antondrroid/V_meter_013/soft_MCU/multimeter/drawings/Untitled 1.odt

# Описание работы импульсного блока бесперебойного питания

Архитектура блока основана на двойном преобразовании энергии — сначала сетевое напряжение 220 -90 В преобразуется в напряжение 5В, используемое для заряда Li+ion аккуммулятора, состоящего из параллельно подключенных элементов. Преимущество такого подключения в том, что

1. отсутствует необходимость балансировки последовательно подключенных аккуммуляторов.

2. Возможность наращивания емкости неограниченно без изменения конструкции.

Затем напряжение 5В преобразуется импульсным регулятором напряжения
