antondrroid/V_meter_013/soft_MCU/multimeter/Служебные/TZv1.odt

Проект ТЗ на доработку узла ТГС Н2

1. интегрировать Детектор Отбоя (ДО) в печатную плату (ПП)
2. Присвоить название новой ПП — Плата управления узлом ТГС Н2 и занятие децимального номера (МАВЦ 467291.011)
3. Заменить на русские электрорадиоэлементы (ЭРИ) из перечня разрешенных либо по возможности на просто русские.
4. изменить установку микросхемы D7 на верхнюю сторону платы для увеличения просвета между платами на 15 мм (С учетом п.9 высотой 7 мм)
5. предусмотреть установку дополнительных разьемов для подключения платы управления.
6. Вывод световой индикации на разьем (4 вывода)
7. Решить вопрос по выводу световой индикации состояния устройства на лицевую панель. Светодиоды «Пит» и «Соед»
  ( Надо ли их выводить ?)
8. Решить вопрос по выводу кнопки ручного управления отключением «Отбой» устройства на лицевую панель. ( Надо ли их выводить ?)
9. Предусмотреть пространство для прохода кабелей между платами
10. Размещение отверстия в корпусе коробки для радиоэлементов для вывода гермоввода кабелей на корпузе узла в связи с новой разводкой плат.
11. Доработка узла ТГС Н2 МАВЦ 467291.010
12. Изменить разводку потенциометров R33 “Динамик” и R34 “Микрофон”, чтобы опустить их на поверхность ПП, для увеличения просвета между ПП на 4 мм.
13. Подбор потенциометров, допускающих регулировку через отверстие в ПП для увеличения просвета между платами на 22 мм (с учетом п.3)
14. Существует ли необходимость их многократной регулировки при эксплуатации? Тогда можно установить потенциометры модели с открытой ползунковой поверхностью.
15. Изменение конструкции радиатора МАВЦ 467291.010 (в соотв. с п. 3)
