antondrroid/V_meter_013/soft_MCU/multimeter/Служебные/TZv2.odt

ТЗ на конструирование узла ТГС Н2

1. интегрировать Детектор Отбоя (ДО) в печатную плату (ПП)
2. Присвоить название новой ПП — Плата управления узлом ТГС Н2 и занятие децимального номера (МАВЦ 467291.011)
3. Заменить на русские электрорадиоэлементы (ЭРИ) из перечня разрешенных либо по возможности на просто русские.
4. изменить установку микросхемы D7 на верхнюю сторону платы для увеличения просвета между платами на 15 мм (С учетом п.9 высотой 7 мм)
5. предусмотреть установку дополнительных разьемов для подключения платы управления.
6. Предусмотреть пространство для прохода кабелей между платами
7. Размещение отверстия в корпусе коробки для радиоэлементов для вывода гермоввода кабелей на корпусе узла в связи с новой разводкой плат.
8. Доработать узел ТГС Н2 МАВЦ 467291.010
9. Изменить разводку потенциометров R33 “Динамик” и R34 “Микрофон”, чтобы опустить их на поверхность ПП, для увеличения просвета между ПП на 4 мм.
10. Изменить конструкцию радиатора МАВЦ 467291.010 (в соотв. с п. 3)
11. Схема Э3 и перечень элементов в приложении.

Разработал Михайлов

Согласовано Елкин

Утвердил Крысин
