antondrroid/V_meter_013/soft_MCU/multimeter/Служебные/~Z.ODT

Проект ТЗ на доработку узла ТГС Н2

1. интегрировать Детектор Отбоя (ДО) в печатную плату (ПП)
2. Присвоить название новой ПП — Плата управления узлом ТГС Н2 и занятие децимального номера
3. изменить установку микросхемы на верхнюю сторону платы для увеличения просвета между платами на 15 мм (С учетом п.9 высотой 7 мм)
4. предусмотреть установку дополнительных разьемов для подключения платы управления.
5. Решить вопрос по выводу световой индикации состояния устройства на лицевую панель.( Надо ли их выводить или эта функция повлечет за собой дополнительную переделку всего устройства?)
6. Решить вопрос по выводу кнопки ручного управления отключением устройства на лицевую панель.( Надо ли их выводить или эта функция повлечет за собой дополнительную переделку всего устройства?)
7. Предусмотреть пространство для прохода кабелей между платами
8. Размещение отверстия для вывода гермоввода кабелей на корпузе узла.
9. Изменить разводку потенциометров, чтобы опустить их на поверхность ПП, для увеличения просвета между ПП на 4 мм.
10. Подбор потенциометров, допускающих регулировку через отверстие в ПП для увеличения просвета между платами на 22 мм (с учетом п.3)
