antondrroid/V_meter_013/soft_MCU/multimeter/Служебные/закупка/467291.010_v1.odt

Генеральному директору

ООО «ЛОТЕС ТМ»

Стыскину Б.М.

Служебная записка

Прошу приобрести комплектующие изделия для изготовления опытного образца узла ТГС Н2 МАВЦ.467291.010

Количество комплектов: 2 (два).

Начальник ОРТС

________________ / Ю.Д.Крысин /

Приложение:

  Перечень элементов — 8 листов.
