antondrroid/V_meter_013/soft_MCU/multimeter/Служебные/закупка/Служебная закупка УК48-4С.odt

Ген. Директору ООО «Лотес ТМ»

Стыскину Б М

СЛУЖЕБНАЯ ЗАПИСКА

Устройство контактное УК48-4С необходимо в процессе отладки печатной платы с применением микроконтроллера 1887ве4у для его оперативной замены и программирования.

Это служебное оборудование и в изделие, поставляемое заказчику, оно устанавливаться не будет.

Ведущий инженер ОРТС С.И.Тимкин
