antondrroid/V_meter_013/soft_MCU/multimeter/Служебные/ЗАявка на монтаж/Бланк заявки на изготовление печатных плат1.odt

Начальнику производственного

управления ООО Лотес ТМ

Непорада Ю.А.

Служебная записка

Прошу изготовить опытный образец изделия «Модуль 1887»

Применяемость: ТГС Н2

Наименование: модуль 1887 МАВЦ.467291.012

Начальник ОРТС Крысин Ю Д _________

Приложение

1.Печатная плата 758725.032 = 1 шт.

2.Перечень элементов – 3 листа

3.Сборочный чертеж -1лист

4.Электрическая схема – 1 лист.
