antondrroid/V_meter_013/soft_MCU/multimeter/Служебные/ЗАявка на монтаж/изготовление OPTC758725001.odt

Начальнику производственного

управления ООО Лотес ТМ

Непорада Ю.А.

Служебная записка

Прошу дать указание изготовить опытный образец изделия .

Применяемость: УКС АОС

Наименование: ОРТС 758725.001 V3

Начальник ОРТС Крысин Ю Д _________

тел.155

Приложение

1.Печатная плата 758725.033 …………………………………………. 2 шт.

2.Перечень элементов ОРТС 758725.001 V3………………...1 лист

3.Сборочный чертеж ОРТС 758725.001 СБ……………………..1 листа

4.Электрическая схема ОРТС 758725.001 Э3…………………..1 листа
