antondrroid/V_meter_013/soft_MCU/multimeter/Служебные/ЗАявка на монтаж/изготовление печатных плат467291013.odt

Начальнику производственного

управления ООО Лотес ТМ

Непорада Ю.А.

Служебная записка

Прошу дать указание изготовить опытный образец изделия .

Применяемость: ТГС Н2

Наименование: Узел процессора ТГС Н2 МАВЦ.467291.013

Начальник ОРТС Крысин Ю Д _________

Приложение

1.Печатная плата 758725.033 …………………………………………. 1 шт.

2.Перечень элементов МАВЦ.467291.013ПЭ3………………...3 листа

3.Сборочный чертеж МАВЦ.467291.013СБ……………………..3 листа

4.Электрическая схема МАВЦ.467291.013Э3…………………..2 листа
