antondrroid/V_meter_013/soft_MCU/multimeter/Служебные/Протокол испытаний ТГС Н2/предложения по клавиатуре.odt

Утверждаю

Начальник ОРТС

Крысин Ю.Д.

Предложения

по вариантам исполнения подложки

для сенсорной клавиатуры

###### Разработал

###### Михайлов С.Л.

# 1. Технические требования.

## 1.1. Материалы используемые в подложке, должны обеспечивать срабатывание сенсора

## 1.2. Должна обеспечиваться видимость излучения светодиодов сквозь материал подложки.

  3. Должна обеспечиваться возможность записи имени абонента рукой, стирание текста и новая перезапись.
  4. Должна обеспечиваться возможность подкладывания заранее напечатанных этикеток с номерами абонента.
  5. Должна обеспечиваться защита надписей от случайного стирания и загрязнения.
  6. Должна обеспечиваться защита печатной платы с сенсорами от непосредственного контакта с пользователем.

2.Описание конструкции

2.1 Подложка изделия является многослойной и содержит 3 слоя:

а) наклейка из пластика предназначенного для печати на лазерном принтере, на которую наносится сетка с расположением сенсорных кнопок и выполнены просечки для пропускания света от диодов индикации.

Наклейка допускает возможность ручной записи маркером имени абонента в соответствующую ячейку и стирание при необходимости ватным тампоном со спиртовым раствором (специальными салфетками для ухода за оргтехникой)

При этом смываются только следы от маркера, в то время как лазерный порошок является нерастворимым в спирте и координатная сетка остается нетронутой.

Возможно также приклеивание к ней заранее напечатанных самоклеющихся этикеток с последующим многократным отклеиванием и приклеиванием.

б) опционально: бумажная одноразовая этикетка, повторяющая форму наклейки из пункта а) и предназначенная для заполнения пользователем на месте. Можно включить в комплект несколько штук.

в) Защитный прозрачный слой, толщиной 250-350 мкм, гладкий либо с пуклевками диаметром 12 мм для имитации нажатия.

Можно комплектовать изделие накладками обоих видов, по выбору пользователя.

2.2 Варианты защитного слоя с пуклевками

A. Пуклевка для нажатия расположенная по центру клавиши. Поверхность может быть прозрачная, либо матовая.
  Позволяет просматривать надписи на подложке без значительных искажений как на прозрачной, так и на покрытой матовым слоем поверхности.
B. Пуклевка для светодиода (рассеиватель) выполненный в виде множества мелких выпуклостей для увеличения светового пятна на поверхности панели.
C. Пуклевка для светодиода (рассеиватель) поднятая над поверхностью, для обеспечения более широкого угла обзора индикации (до 180о).

Нажимаемые пуклевки возможно изготовить на пленках толщиной до 300мкм, так как на более толстых пленках возможно обламывание при нажатии.

На пленках толщиной более 300мкм возможно изготовление ненажимаемых пуклевок для рассеивателей светового потока, при оставлении сенсорной площадки гладкой.

2.3 Толщина покрытия

Толщина покрытия 2000мкм препятствует срабатыванию сенсора, используемого в данной конструкции.

В макете использованы панели толщиной 500 — 2000 мкм, дающие представление о затруднении срабатывания с ростом толщины защитного слоя.

Приемлемое время срабатывания получается при толщине покрытия 500 — 1000 мкм, при толщине 1500мкм срабатывание затруднено, при 2000мкм срабатывание не происходит.

Таблица 1

Наименование испытаний и проверок | № пункта методики испытаний | Примечание
1 Проверка входящего вызова от абонента ТА к абоненту ТГС Н2 | 2.1
2 Проверка исходящего вызова от абонента ТГС Н2 к абоненту ТА | 2.2
3 Проверка отбоя соединения со стороны абонента ТА при изменении сопротивления абонентской линии | 2.3
4 Проверка отбоя соединения по таймеру при отсутствии голосовой активности | 2.4
5 Проверка входящего вызова от абонента ТА к ТГС Н2 при изменении амплитуды вызывного сигнала | 2.5
6. Проверка входного сопротивления ТГС Н2 в режиме «Соединение» | 2.6

Испытания проводятся рабочей группой, в составе представителей ОРТС ООО «ЛОТЕС ТМ» и по согласованию представителей ПУ.

Методики, условия и порядок проведения проверок могут уточняться и дополняться решением комиссии по проведению испытаний.

Допускается проведение проверок по отдельным компонентам и дополнительных тестов.

1.5. Условия и порядок проведения испытаний

Все испытания проводятся согласно пункту 1.4 в различных климатических условиях, с оформлением отдельного протокола по каждому пункту настоящего раздела.

- 1.5.1 в нормальных климатических условиях:
- температуры окружающего воздуха от 288 до 298 К (от плюс 15 до плюс 25 С);
- относительной влажности воздуха не более 75 % при температуре не выше 298 К (25 С);

атмосферного давления от 86 до 106 кПа (от 645 до 795 мм рт.ст.).

- 1.5.2 на пониженную температуру
- температуры окружающего воздуха от -40 ºС до - 10 С;
- 1.5.1 на повышенную температуру

- температуры окружающего воздуха от плюс 25 до плюс 40 С;

# 2. Методика испытаний.

Перед началом испытаний собрать схему согласно приложению 1.

## 2.1 Проверку входящего вызова от абонента ТА к абоненту ТГС Н2 проводят следующим методом:

а) установить на имитаторе линии ноль км;

б) Поднять трубку на ТА и набрать вызывной номер ТГС Н2. Должно установиться соединение;

в) Абонент ТА передает сообщение абоненту ТГС Н2. Контролировать воспроизведение этого сообщения в динамике ТГС Н2;

г) нажать и удерживать кнопку «Микрофон» на ТГС Н2. Абонент ТГС Н2 передает сообщение абоненту ТА. Контролировать воспроизведение этого сообщения в динамике трубки ТА.

д) положить трубку на ТА. Контролировать что через время не более 4 с должен произойти отбой соединения, воспроизведение акустического сигнала «Отбой» в динамике ТГС Н2 должно прекратиться;

Изделие считают выдержавшим проверку если:

- при входящем вызове на ТГС Н2 соединение автоматически устанавливается;

- контрольный текст прослушивается без искажений, провалов и изменения тембра;

- отбой соединения со стороны абонента ТА производится за время не более 4 с.

## 2.2 Проверку исходящего вызова от абонента ТГС Н2 к абоненту ТА проводят следующим методом:

а) установить на имитаторе линии 0 км;

б) нажать кнопку на ТГС Н2 «Вызов», контролировать наличие акустического сигнала «Ответ станции»;

в) через время приблизительно 10с контролировать наличие акустического сигнала «Отбой». Контролировать что через время не более 4 с должен произойти отбой соединения, воспроизведение акустического сигнала «Отбой» в динамике ТГС Н2 должно прекратиться.

г) повторить проверку по п.п. б) и в) для сопротивления линии 1-8 км

Изделие считают выдержавшим проверку если:

- при исходящем вызове на ТГС Н2 прослушивается сигнал «Ответ станции»;

- отбой соединения со стороны абонента ТГС производится за время не более 4 с.

## 2.3 Проверку входящего вызова от абонента ТА к ТГС Н2 при изменении (снижении) амплитуды вызывного сигнала в связи с увеличением длины линии и отбоя соединения со стороны абонента ТА при изменении сопротивления абонентской линии (далее - АЛ) проводят следующим методом:

а) установить на имитаторе линии 1 км;

б) провести проверку согласно п.2.1 а), б), д);

в) последовательно устанавливая на имитаторе линии от 2 до 8 км, повторить проверку согласно п.2.1 а), б), д);

Изделие считают выдержавшим проверку если отбой соединения производится за время не более 4 с.

## 2.4 Проверку отбоя соединения по таймеру при отсутствии голосовой активности проводят следующим методом:

а) установить на имитаторе линии 0 км;

б) поднять трубку на ТА и набрать вызывной номер ТГС Н2. Должно установиться соединение;

в) если в течении 1 минуты на ТГС Н2 не нажимают кнопку «Микрофон», а на ТА отключен (приглушен) микрофон, то соединение должно отбиться, абонент ТА должен услышать акустический сигнал «Отбой» (короткие гудки);

г) положить трубку на ТА;

д) установить на имитаторе линии 8 км и повторить проверку по п.п.2.4 б) - г).

Изделие считают выдержавшим проверку если при отсутствии голосовой активности в режиме соединения автоматический отбой соединения производится за время не более 60 с.

2.5 Проверку входного сопротивления ТГС Н2 в режиме «Соединение» проводят следующим методом:

а) установить сопротивление линии 0 км;

б) установить исходящее соединение, нажав на ТГС Н2 кнопку «Вызов»;

г) измерить напряжение постоянного тока на входе ТГС Н2;

д) вычислить входное сопротивление по формуле: Rвх =U/Iлин, где Iлин=20 мА.

Изделие считают выдержавшим проверку, если значение Rвх от 300 до 850 Ом.

# Протокол испытаний 1.5.1

Узла процессора ТГС Н2 МАВЦ.467291.013

Пункт | № попытки | Расстояние (эквивалент линии, км)
| | 0 | 1 | 2 | 3 | 4 | 5 | 6 | 7 | 8 | 9 | 10
2.1 | 1
2.2 | 1
2.3 | 1
2.4 | 1
2.5 | 1 | Uвх = ……...В Rвх = ……....В / 20 мA = ….…...Ом

Вывод:

Изделие МАВЦ.467291.013 узел процессора ТГС Н2 соответствует требованиям

- ТЗ на ТГС Н2;
- Технические требования на ПО ТГС Н2
- ПМИ ТГС Н2.

Может быть внедрено для серийного производства.

Испытания изделия проводила комиссия в составе :

Кротов Б.Г. — председатель комиссии…………………………./ /

Михайлов С.Л. - член комиссии…………………………………/ /

ТГС Н2 зав.№____________

Протокол № 1.5.2

Испытания на пониженную температуру

## 1 Время проведения испытаний

- Дата 28.05.18 г. Начало испытаний 09-40 Завершение испытаний 18-00

## 2 Состав испытываемого оборудования

СЧ изделия участвующие в испытаниях вне климатической камеры:

Наименование и обозначение изделия | Кол-во (шт.) | Группа исполн. (ВВФ) | Зав.№
1.1 Терминал громкоговорящей связи «НАБАТ» Н2, МАВЦ.465482.016 (ТГС Н2) | 1 | 1.3

- Модуль базовый «НАБАТ» А2,

- Аппарат телефонный ВЕКТОР ST-555/01

- СОДС «Набат»

## 3 Этапы испытаний:

1) НКУ – проверка;

2) Предельная пониженная температура – выдержка в выключенном состоянии 3 ч;

3) Рабочая пониженная температура – выдержка в выключенном состоянии 3 ч – включение –проверка;

4) НКУ – выдержка в выключенном состоянии 3 ч – включение – проверка.

## 4 Результаты испытаний

Вид проверки | Содержание проверки | Этапы испытаний и время проверки | | | | | Примеч.
| | 1 НКУ | 2 -40 ºС | | 3 -10 ºС | 4 НКУ
Связь с ТГС Н2 | Вызов, | + | НП | | + | +
| соединение | + | НП | | + | +
| отбой | + | НП | | - | -

Замечания

Испытания проводили: Испытатель

ТГС Н2 зав.№____________

Протокол № 1.5.3

Испытания на повышенную температуру

## 1 Время проведения испытаний

- Дата 28.05.18 г. Начало испытаний 09-40 Завершение испытаний 18-00

## 2 Состав испытываемого оборудования

СЧ изделия участвующие в испытаниях вне климатической камеры:

Наименование и обозначение изделия | Кол-во (шт.) | Группа исполн. (ВВФ) | Зав.№
1.1 Терминал громкоговорящей связи «НАБАТ» Н2, МАВЦ.465482.016 (ТГС Н2) | 1 | 1.3

- Модуль базовый «НАБАТ» А2,

- Аппарат телефонный ВЕКТОР ST-555/01

- СОДС «Набат»

## 3 Этапы испытаний:

1) НКУ – проверка;

2) Рабочая повышенная температура – выдержка во включенном состоянии 2 ч – проверка;

3) Предельная повышенная температура – выдержка в выключенном состоянии 2 ч;

4) Рабочая повышенная температура – выдержка 2 ч – включение – проверка;

5) НКУ – выдержка во включенном состоянии 2 ч – проверка.

## 4 Результаты испытаний

Вид проверки | Содержание проверки | Этапы испытаний и время проверки | | | | | Примеч.
| | 1 НКУ | 2 +40 ºС | 3 +40 ºС | 4 +40 ºС | 5 НКУ
Связь с ТГС Н2 | Вызов, | + | НП | | + | +
| соединение | + | НП | | + | +
| отбой | + | НП | | - | -

Замечания

Испытания проводили: Испытатель

Приложение 2

Протокол cравнительных испытаний

# ТГС Н2 Версия 1 (с установленным модулем DCPC1)

# ТГС Н2 Версия 2 (с контроллером 1887ВЕ4У)

Пункт методики | | Расстояние (эквивалент линии, км)
| | 0 | 1 | 2 | 3 | 4 | 5 | 6 | 7 | 8 | 9 | 10
2.1 | 1
| 2
| 3
| 1
| 2
| 3
2.2 | 1
| 2
| 3
| 1
| 2
| 3
2.3 | 1
| 2
| 3
| 1
| 2
| 3
2.4 | 1
| 2
| 3
| 1
| 2
| 3
2.5 | 1
