antondrroid/V_meter_013/stend_e3/stend_main4_dummy/~D/~02_PE3/element_list_v0.odt

| | | | | xxxx.xxxxxx.xxxПЭ3
Изм. | Лист | № докум. | Подп. | Дата
Разраб. | | | | | Перечень элементов | Лит. | | | Лист | Листов
Пров. | | | | | | | | | 1 | 5
Н.контр.
Утв.

Подп. и дата
Инв. № дубл.
Взам. инв. №
Подп. и дата
Инв. № подл.

Перв. примен. | xxxx.xxxxxx.xxx
Справ. №

Зона | Поз. обозначе- ние | Наименование | Кол. | Примечание
| | | Утвержден
| | | xxxx.xxxxxx.xxx -УД

Копировал

Формат А4

| | | | | xxxx.xxxxxx.xxxПЭ3 | Лист
| | | | | | 2
Изм. | Лист | № докум. | Подп. | Дата

Подп. и дата
Инв. № дубл.
Взам. инв. №
Подп. и дата
Инв. № подл.

Зона | Поз. обозначе- ние | Наименование | Кол. | Примечание

Копировал

Формат А4

| | | | | xxxx.xxxxxx.xxxПЭ3 | Лист
| | | | | | 3
Изм. | Лист | № докум. | Подп. | Дата

Подп. и дата
Инв. № дубл.
Взам. инв. №
Подп. и дата
Инв. № подл.

Зона | Поз. обозначе- ние | Наименование | Кол. | Примечание

Копировал

Формат А4

| | | | | xxxx.xxxxxx.xxxПЭ3 | Лист
| | | | | | 4
Изм. | Лист | № докум. | Подп. | Дата

Подп. и дата
Инв. № дубл.
Взам. инв. №
Подп. и дата
Инв. № подл.

Зона | Поз. обозначе- ние | Наименование | Кол. | Примечание

Копировал

Формат А4

| | | | | xxxx.xxxxxx.xxxПЭ3 | Лист
| | | | | | 5
Изм. | Лист | № докум. | Подп. | Дата

Подп. и дата
Инв. № дубл.
Взам. инв. №
Подп. и дата
Инв. № подл.

Копировал

Формат А4

Лист регистрации изменений
Изм. | Номера листов (страниц) | | | | Всего листов (страниц) в докум. | № докум. | Входящий № сопрово- дительного докум. и дата | Подп. | Дата
| изме- ненных | заме- ненных | новых | аннули- рованных
