antondrroid/V_meter_013/voltmeter_docs/M3500A_DM.pdf

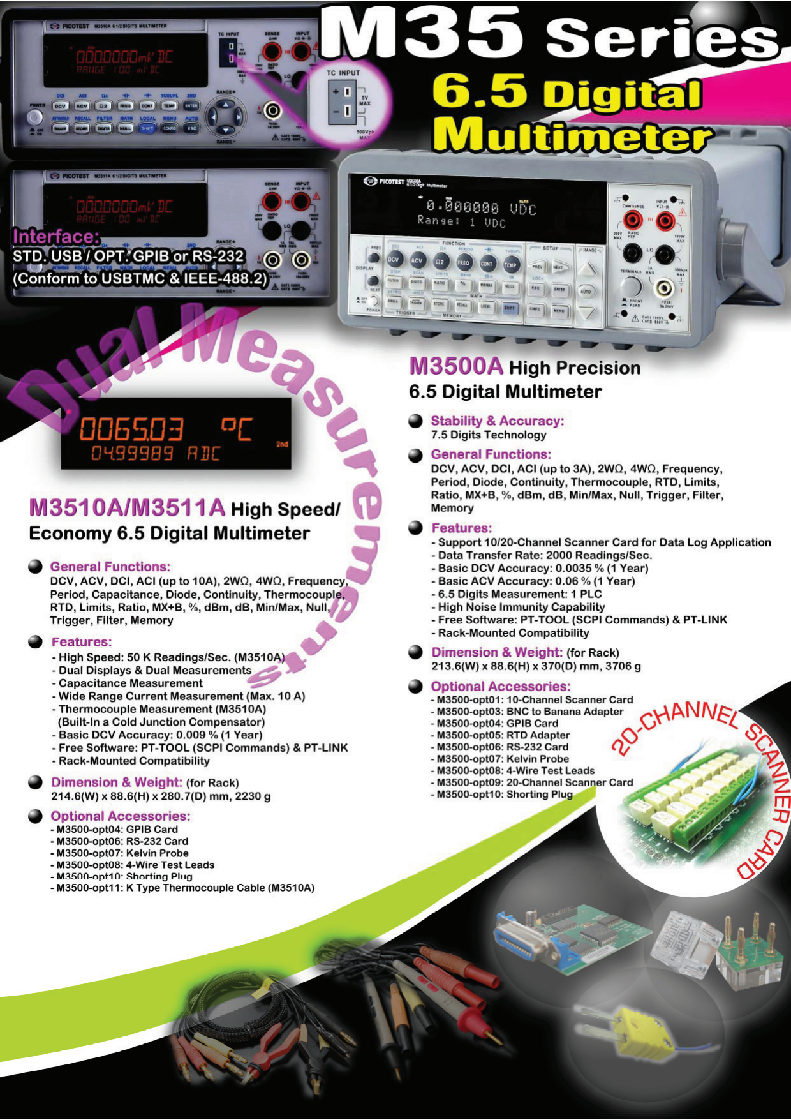
[picture p3: page 1]
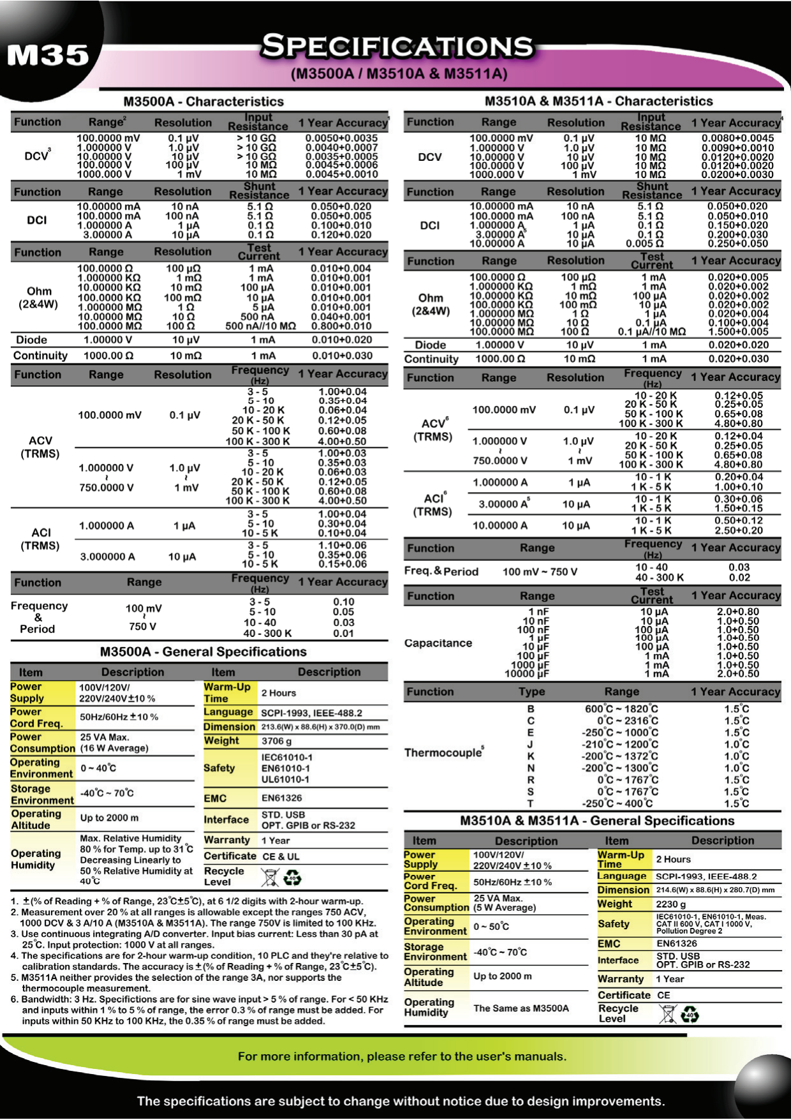
[picture p4: page 2]
