antondrroid/V_meter_013/samples/file sample.jpg

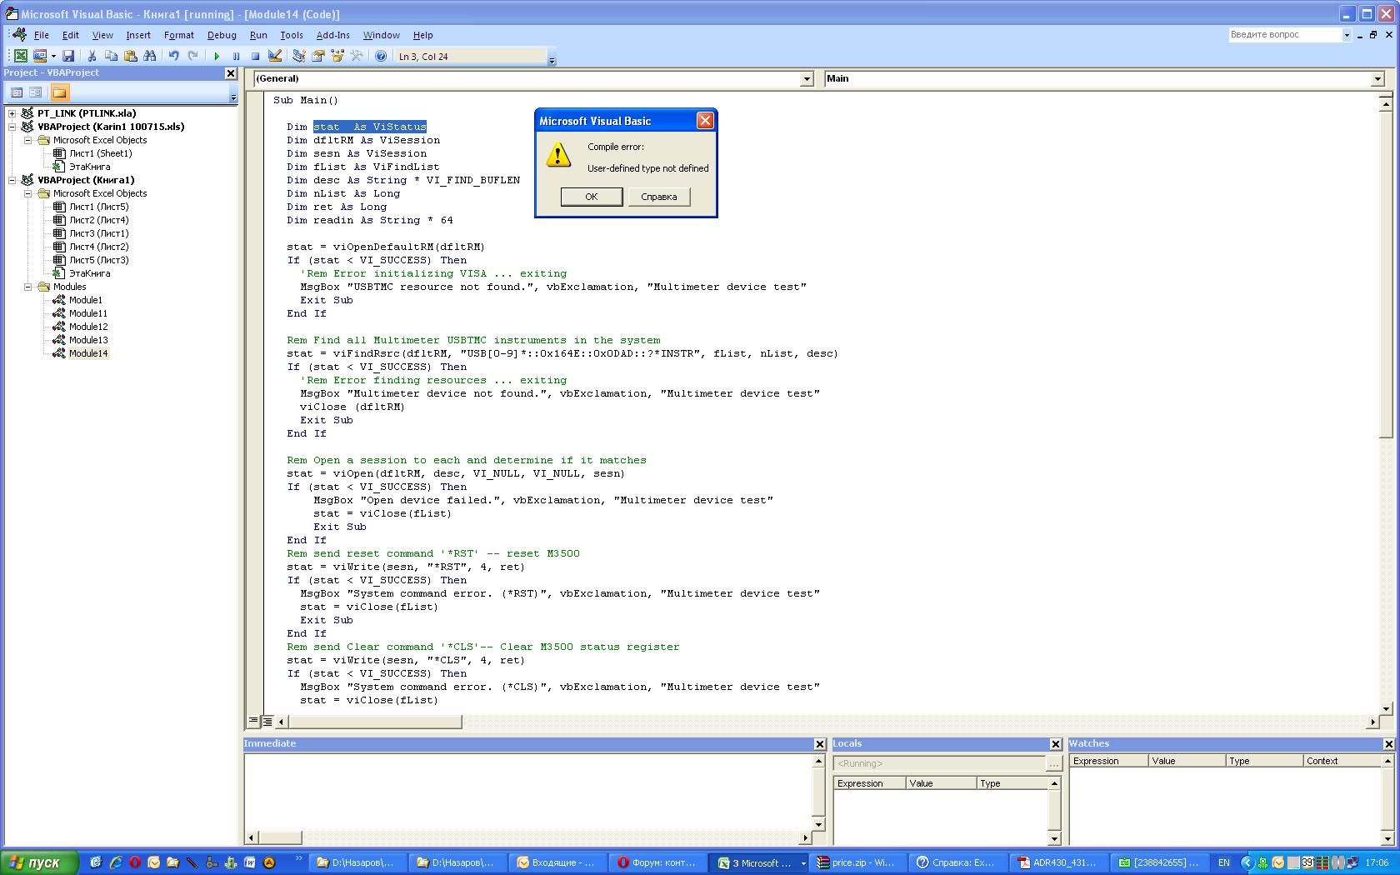
samples/file sample.jpg
