antondrroid/V_meter_013/screen/2021-07-02 12_02_32-NI-VISA - NI — Mozilla Firefox.png

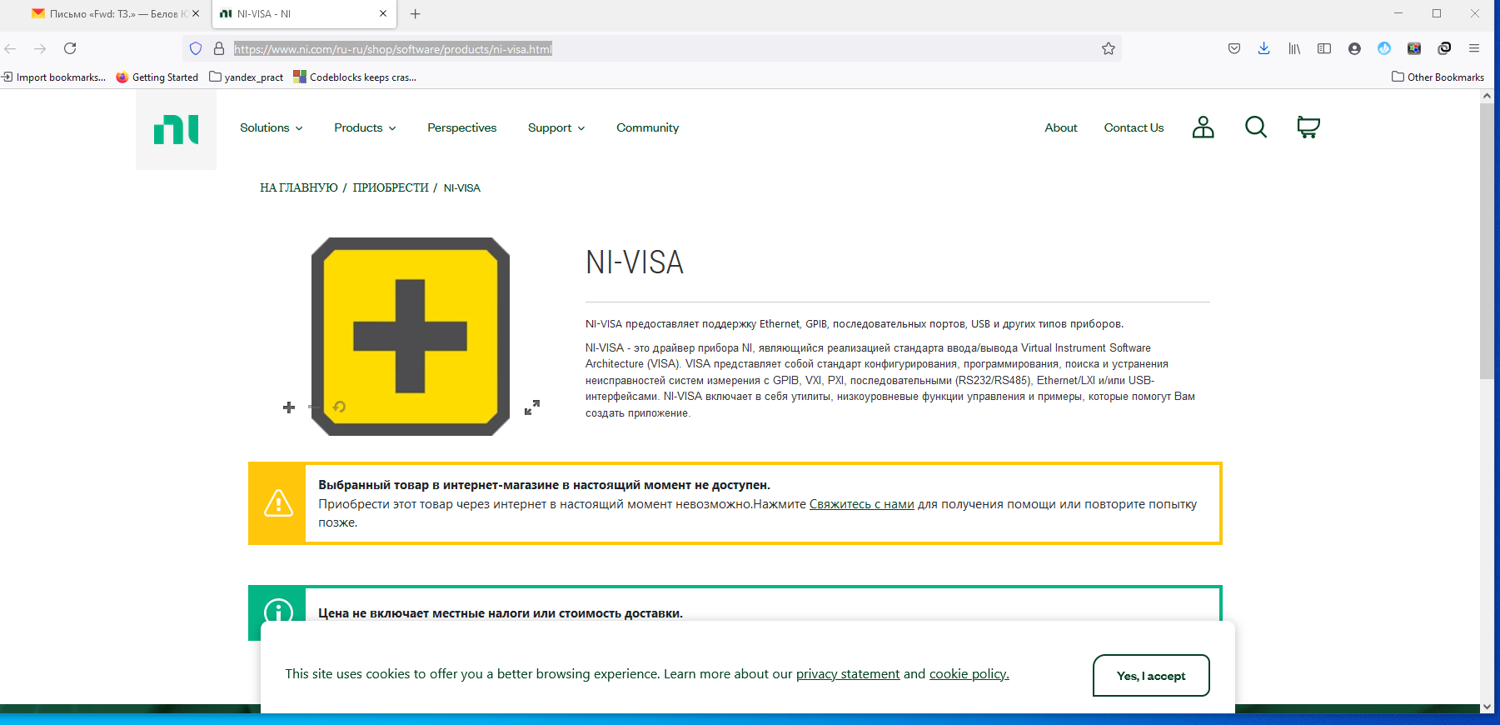
screen/2021-07-02 12_02_32-NI-VISA - NI — Mozilla Firefox.png
