antondrroid/V_meter_013/screen/2021-07-02 12_22_44-Письмо «Fwd_ ТЗ.» — Белов Юрий Максимович — Яндекс.Почта — Mozilla Firefox.png

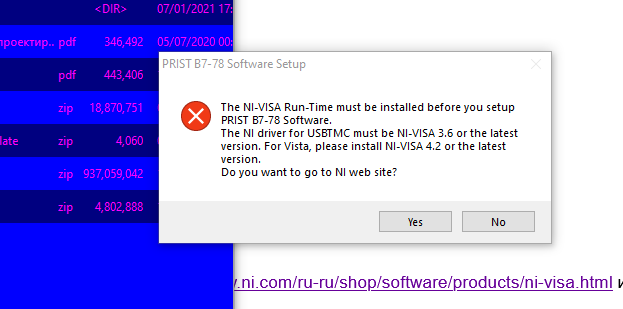
screen/2021-07-02 12_22_44-Письмо «Fwd_ ТЗ.» — Белов Юрий Максимович — Яндекс.Почта — Mozilla Firefox.png
