antondrroid/V_meter_013/screen/2021-07-09 12_47_10-Найди пару - BrainApps.ru — Mozilla Firefox.png

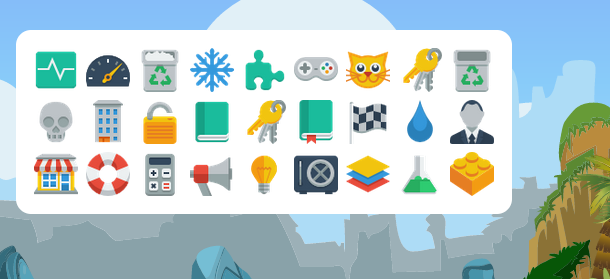
screen/2021-07-09 12_47_10-Найди пару - BrainApps.ru — Mozilla Firefox.png
