antondrroid/V_meter_013/screen/2021-08-05 19_15_09-Total Commander (x64) 9.51 - NOT REGISTERED.png

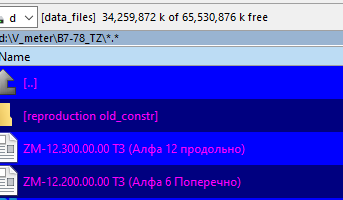
screen/2021-08-05 19_15_09-Total Commander (x64) 9.51 - NOT REGISTERED.png
