antondrroid/V_meter_013/screen/2021_08_03_13_34_38_Письмо_Re_производство_старой_конструкции._Белов_Юрий_Максимович_Яндекс.П.png

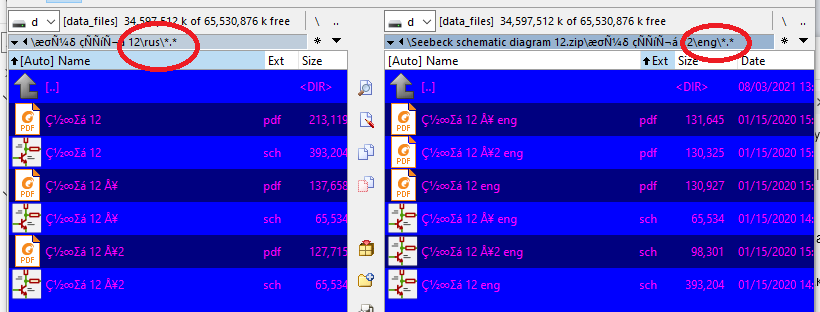
screen/2021_08_03_13_34_38_Письмо_Re_производство_старой_конструкции._Белов_Юрий_Максимович_Яндекс.П.png
