antondrroid/V_meter_013/screen/didnt_reset.png

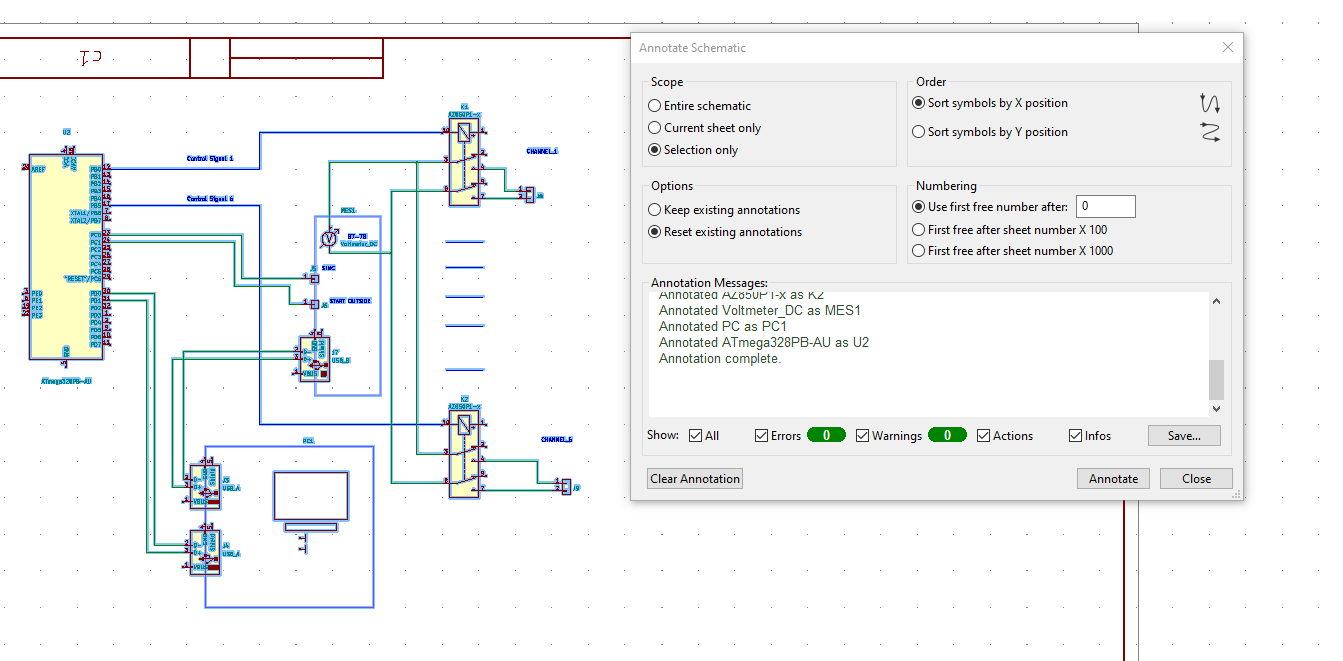
screen/didnt_reset.png
