antondrroid/V_meter_013/screen/~ithub/2021-09-30 17_05_55-GitHub Desktop.png

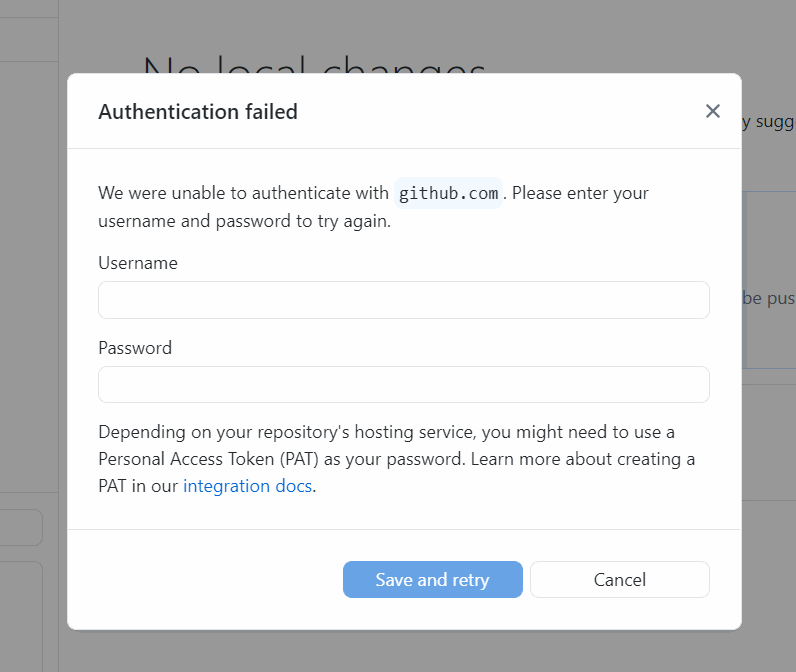
screen/~ithub/2021-09-30 17_05_55-GitHub Desktop.png
