antondrroid/V_meter_013/screen/~ithub/~atal.png

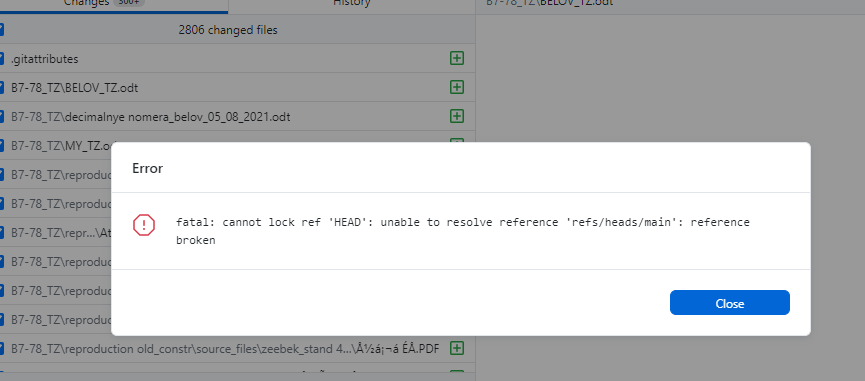
screen/~ithub/~atal.png
