antondrroid/V_meter_013/soft_PC/2021-08-24 23_07_46-ResourceVisa-2.vi Block Diagram.png

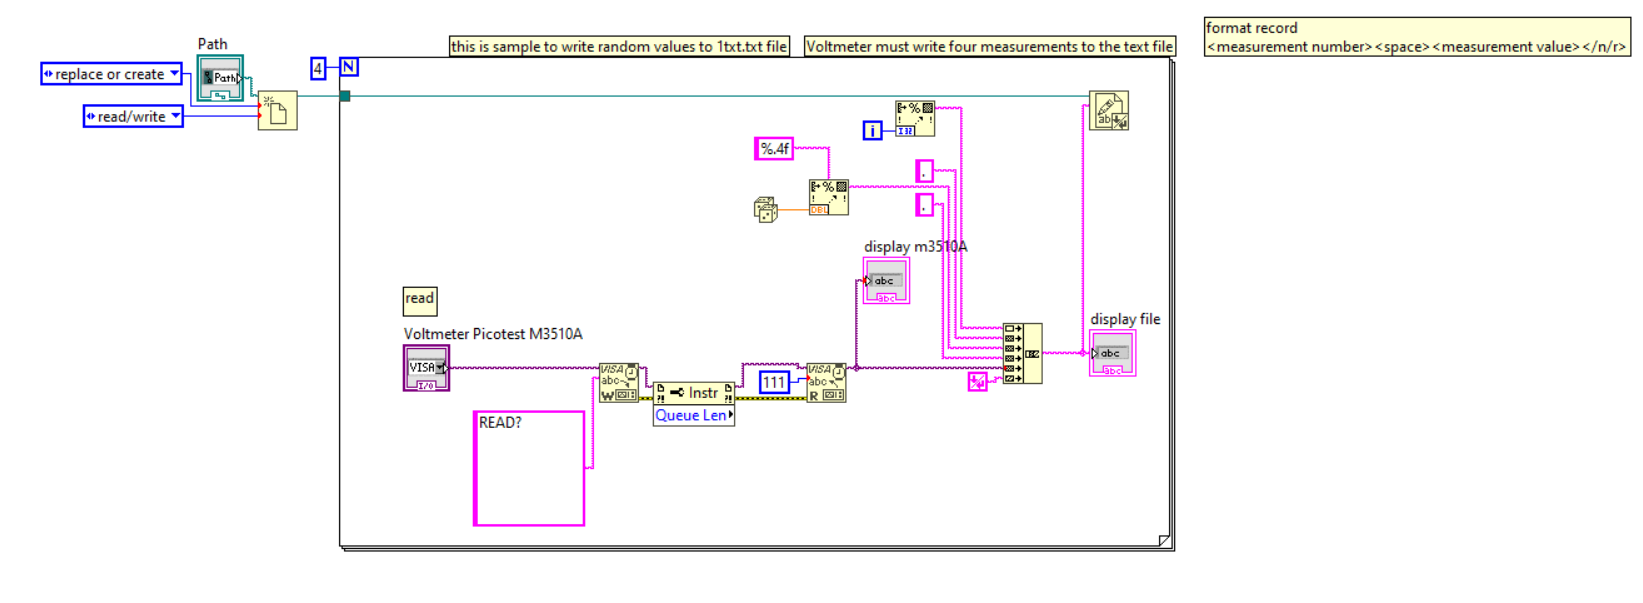
soft_PC/2021-08-24 23_07_46-ResourceVisa-2.vi Block Diagram.png
