antondrroid/V_meter_013/soft_PC/labview/labview_projects/~CREEN/2021-08-02 11_19_23-ResourceVisa.vi Block Diagram _.png

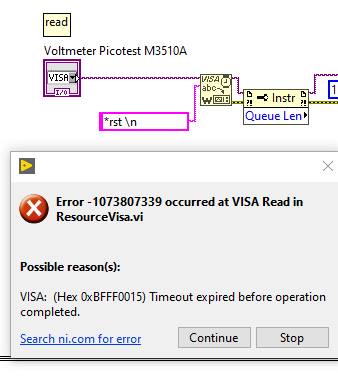
soft_PC/labview/labview_projects/~CREEN/2021-08-02 11_19_23-ResourceVisa.vi Block Diagram _.png
