antondrroid/V_meter_013/soft_PC/labview/labview_projects/~CREEN/2021-08-02 11_25_46-ResourceVisa.vi Block Diagram _.png

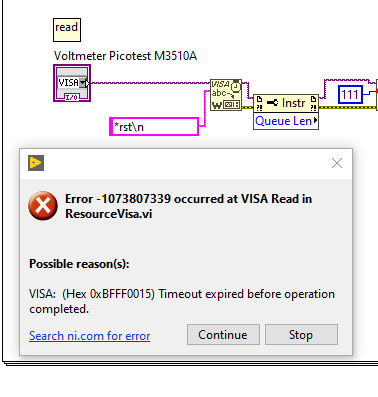
soft_PC/labview/labview_projects/~CREEN/2021-08-02 11_25_46-ResourceVisa.vi Block Diagram _.png
