antondrroid/V_meter_013/soft_PC/labview/labview_projects/~CREEN/2021-08-02 16_50_31-ResourceVisa_write_read_to_txt.vi Block Diagram _.png

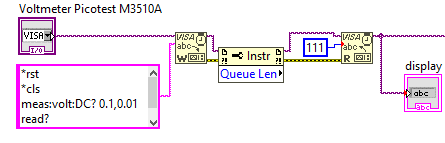
soft_PC/labview/labview_projects/~CREEN/2021-08-02 16_50_31-ResourceVisa_write_read_to_txt.vi Block Diagram _.png
