antondrroid/V_meter_013/soft_PC/labview/labview_projects/~CREEN/2021-08-02 17_37_37-PICOTEST M351XA Series.lvlib_Read (Single Point).vi Block Diagram _.png

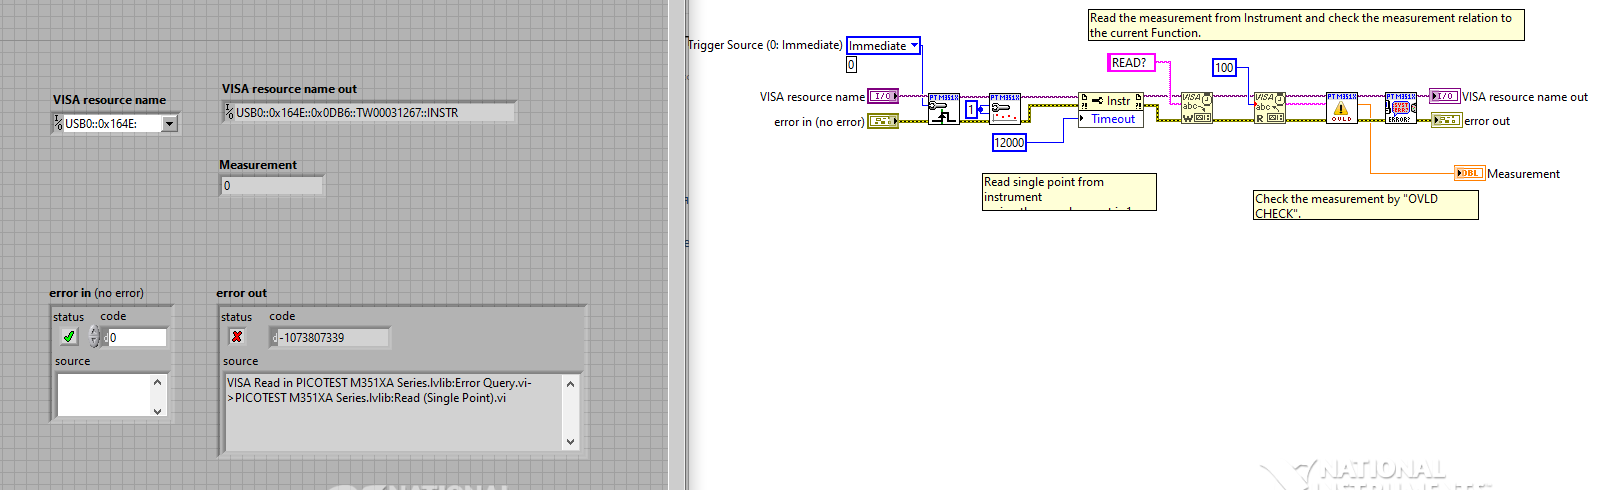
soft_PC/labview/labview_projects/~CREEN/2021-08-02 17_37_37-PICOTEST M351XA Series.lvlib_Read (Single Point).vi Block Diagram _.png
