antondrroid/V_meter_013/soft_PC/labview/labview_projects/~CREEN/2021-08-02 19_30_19-Mozilla Firefox.png

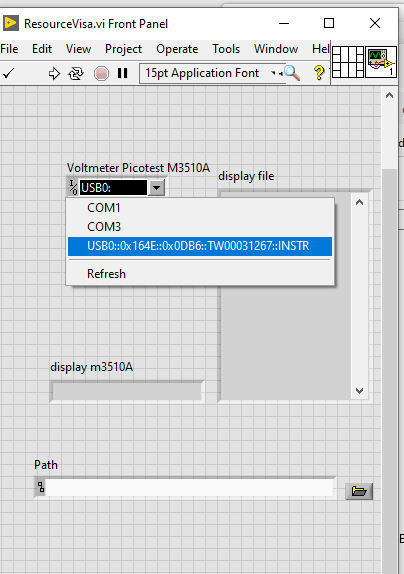
soft_PC/labview/labview_projects/~CREEN/2021-08-02 19_30_19-Mozilla Firefox.png
