antondrroid/V_meter_013/soft_PC/labview/labview_projects/~CREEN/2021-08-03 22_58_19-ResourceVisa.vi Block Diagram _.png

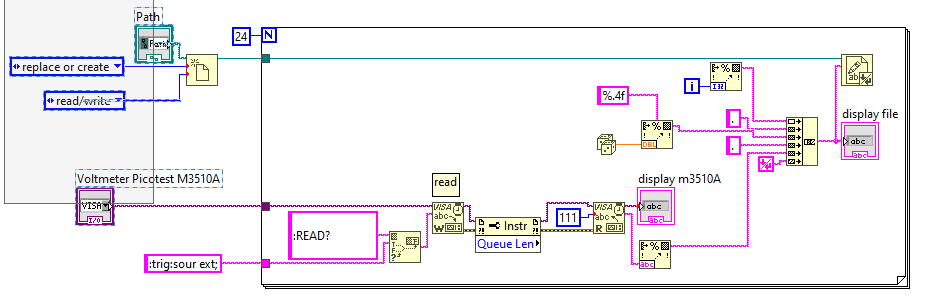
soft_PC/labview/labview_projects/~CREEN/2021-08-03 22_58_19-ResourceVisa.vi Block Diagram _.png
