antondrroid/V_meter_013/soft_PC/labview/labview_projects/~CREEN/2021-08-03 23_07_04-PICOTEST M351XA Series.lvlib_Configure Trigger.vi Block Diagram _.png

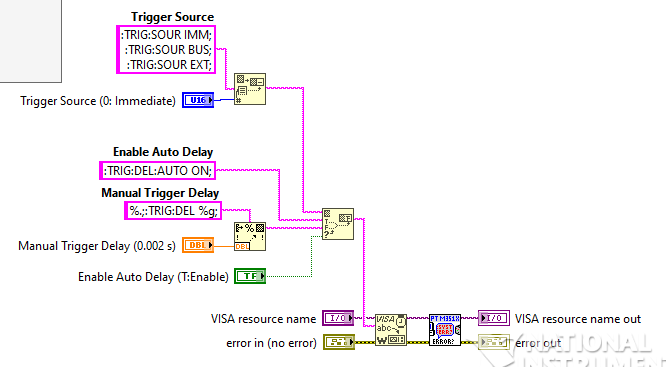
soft_PC/labview/labview_projects/~CREEN/2021-08-03 23_07_04-PICOTEST M351XA Series.lvlib_Configure Trigger.vi Block Diagram _.png
