antondrroid/V_meter_013/soft_PC/labview/labview_projects/~CREEN/2021-08-05 19_05_42-Total Commander (x64) 9.51 - NOT REGISTERED.png

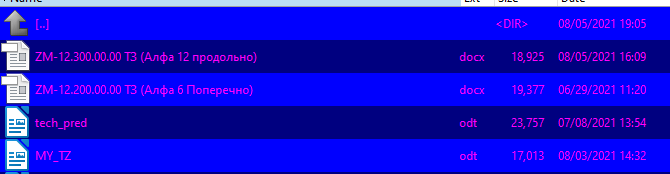
soft_PC/labview/labview_projects/~CREEN/2021-08-05 19_05_42-Total Commander (x64) 9.51 - NOT REGISTERED.png
