antondrroid/V_meter_013/soft_PC/labview/labview_projects/~CREEN/public data.png

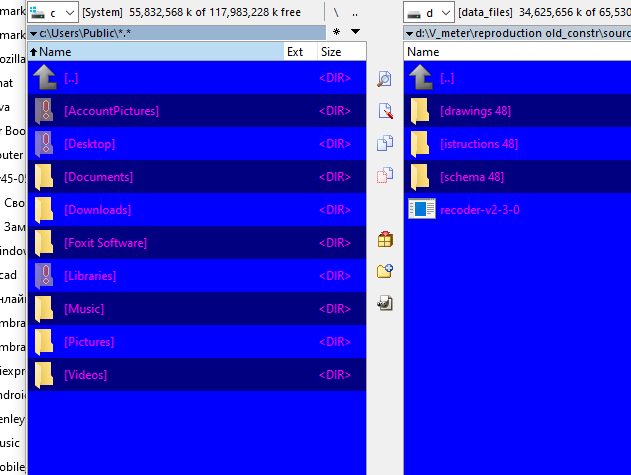
soft_PC/labview/labview_projects/~CREEN/public data.png
