antondrroid/V_meter_013/soft_PC/Soft_choice/activation/2021-07-18 12_49_21-Window.png

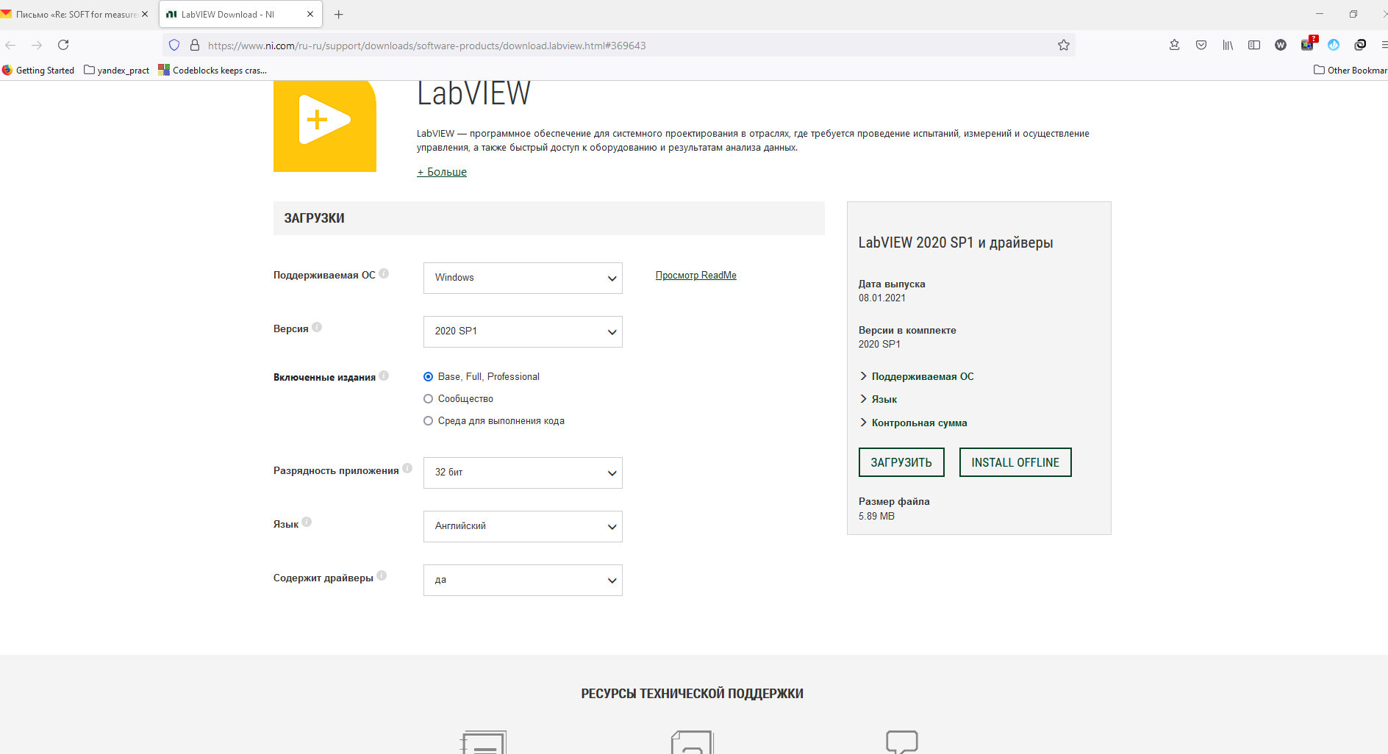
soft_PC/Soft_choice/activation/2021-07-18 12_49_21-Window.png
