antondrroid/V_meter_013/stend_e3/stend_main1/~rawings/plugin error2.png

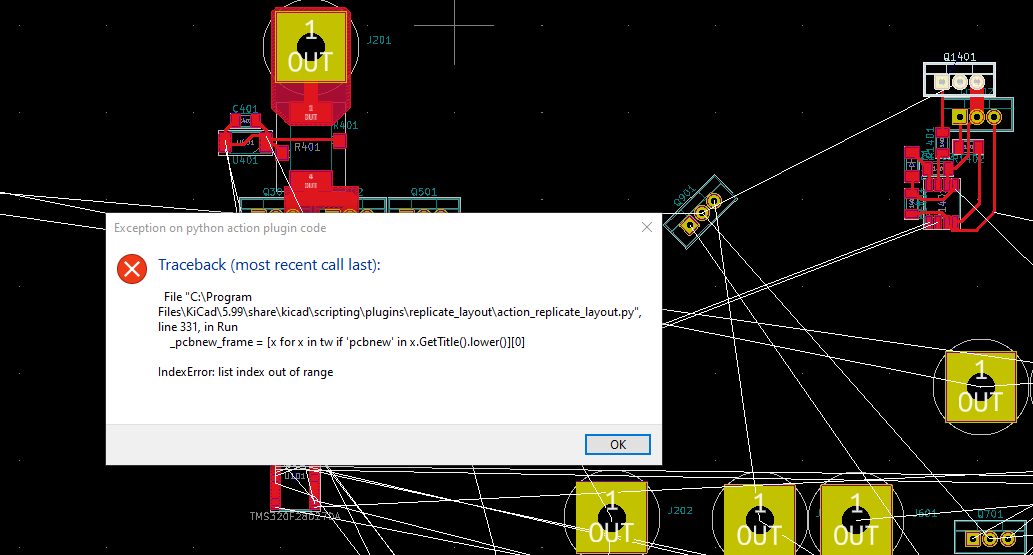
stend_e3/stend_main1/~rawings/plugin error2.png
