antondrroid/V_meter_013/stend_e3/stend_main1/~rawings/plugin error.png

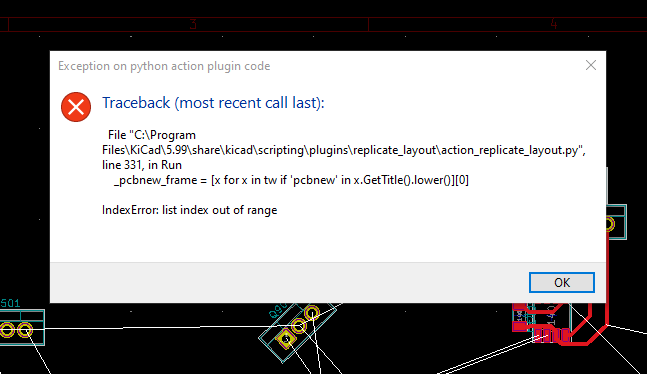
stend_e3/stend_main1/~rawings/plugin error.png
