antondrroid/V_meter_013/stend_e3/stend_main1/~rawings/replication_layout/20_4_sheets_superposition.png

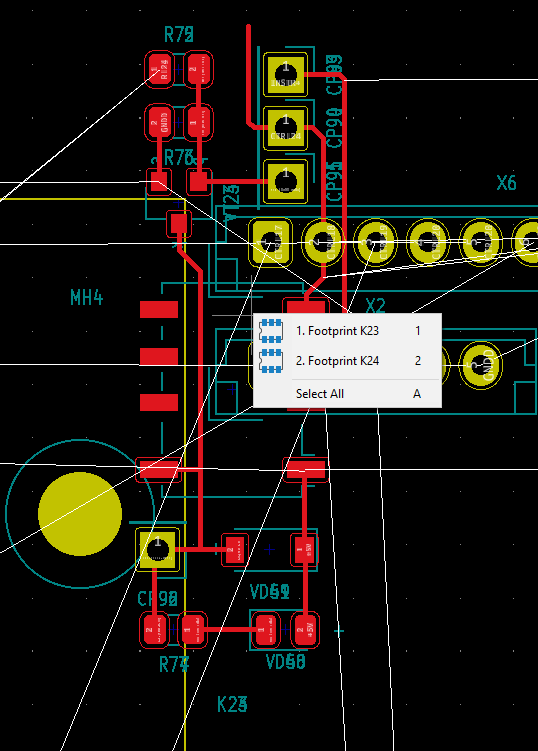
stend_e3/stend_main1/~rawings/replication_layout/20_4_sheets_superposition.png
