antondrroid/V_meter_013/stend_e3/stend_main1/~rawings/replication_layout/23_turn_around.png

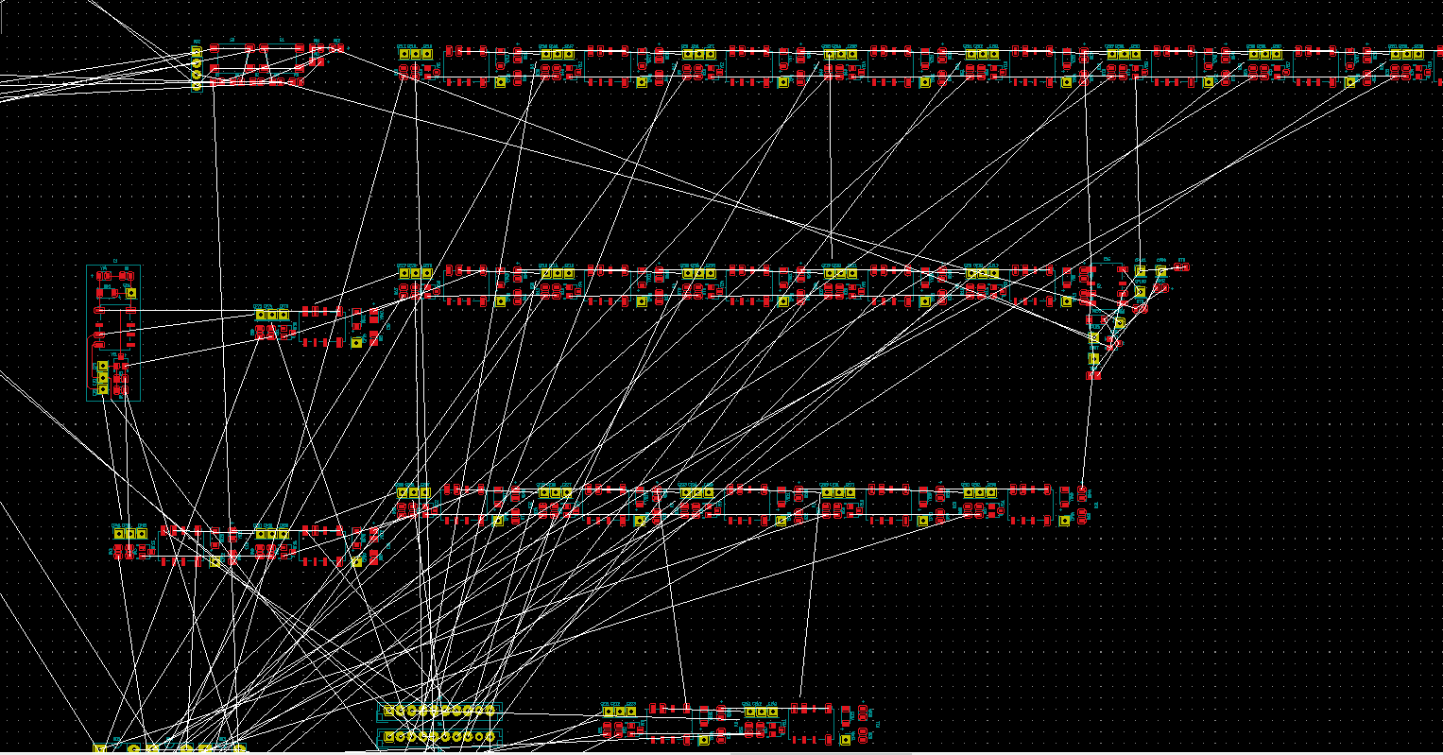
stend_e3/stend_main1/~rawings/replication_layout/23_turn_around.png
