antondrroid/V_meter_013/stend_e3/stend_main1/~rawings/replication_layout/24_tracksd.png

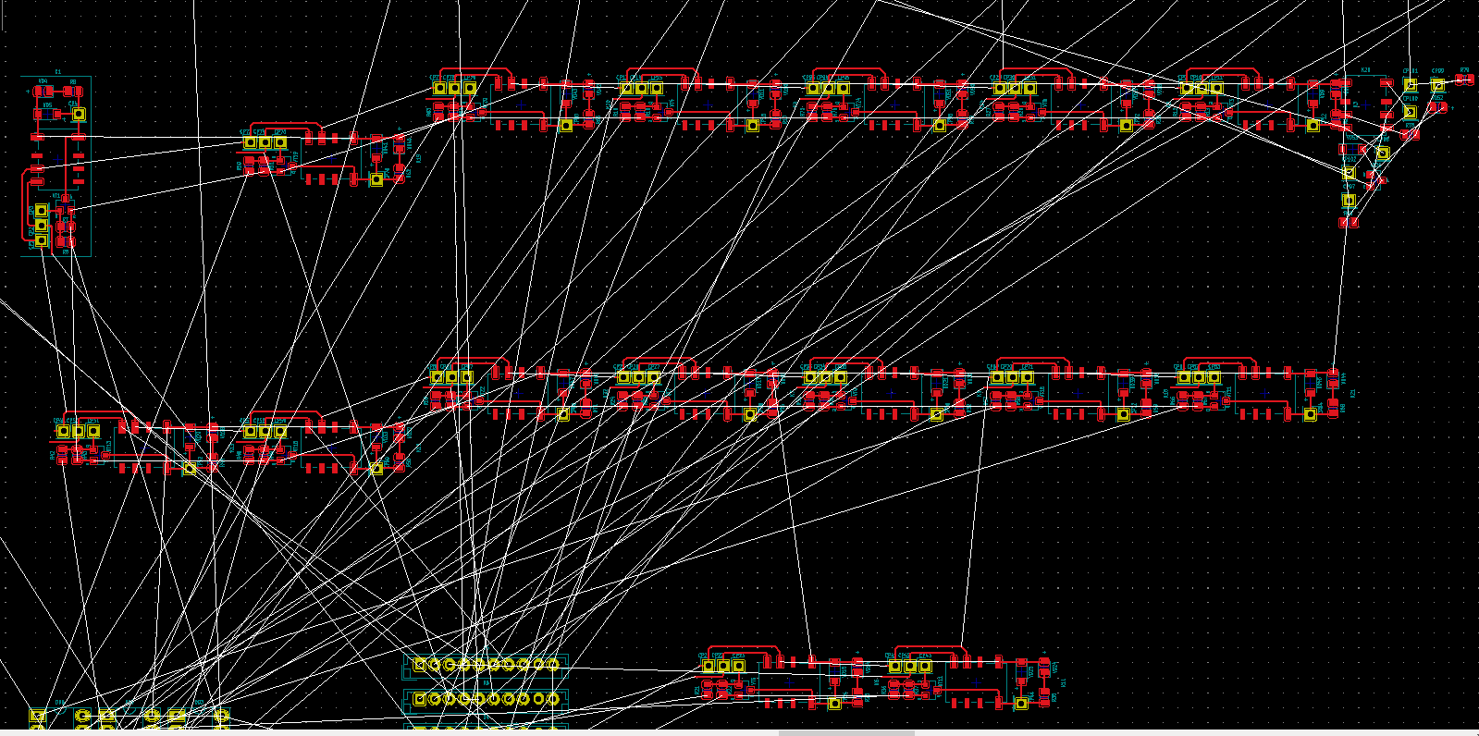
stend_e3/stend_main1/~rawings/replication_layout/24_tracksd.png
