antondrroid/V_meter_013/stend_e3/stend_main1/~rawings/replication_layout/layout_sample1250x560mils.bmp

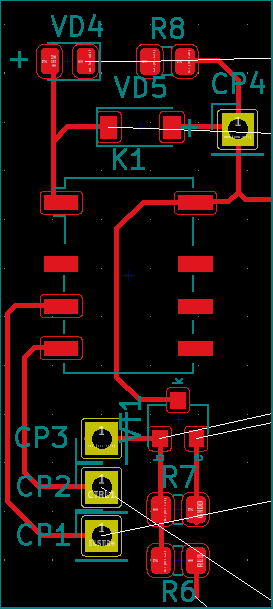
stend_e3/stend_main1/~rawings/replication_layout/layout_sample1250x560mils.bmp
