antondrroid/V_meter_013/stend_e3/stend_main1/~rawings/replication_layout/tracks remained.png

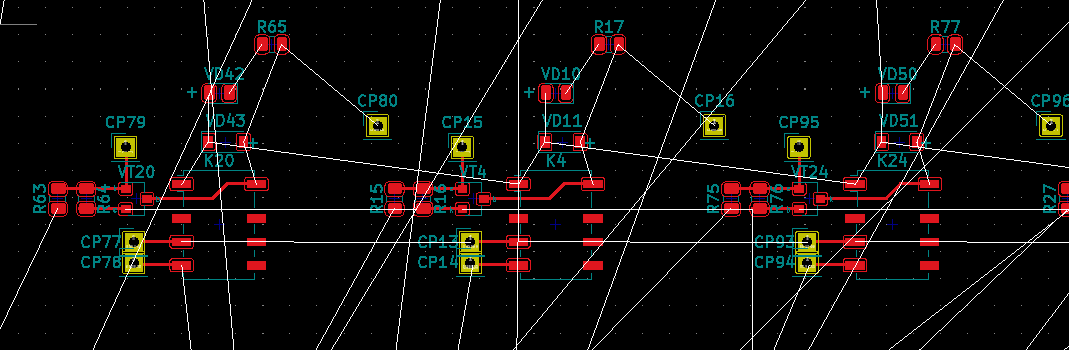
stend_e3/stend_main1/~rawings/replication_layout/tracks remained.png
