antondrroid/V_meter_013/stend_e3/stend_main1/~rawings/replication_layout/~4_error.png

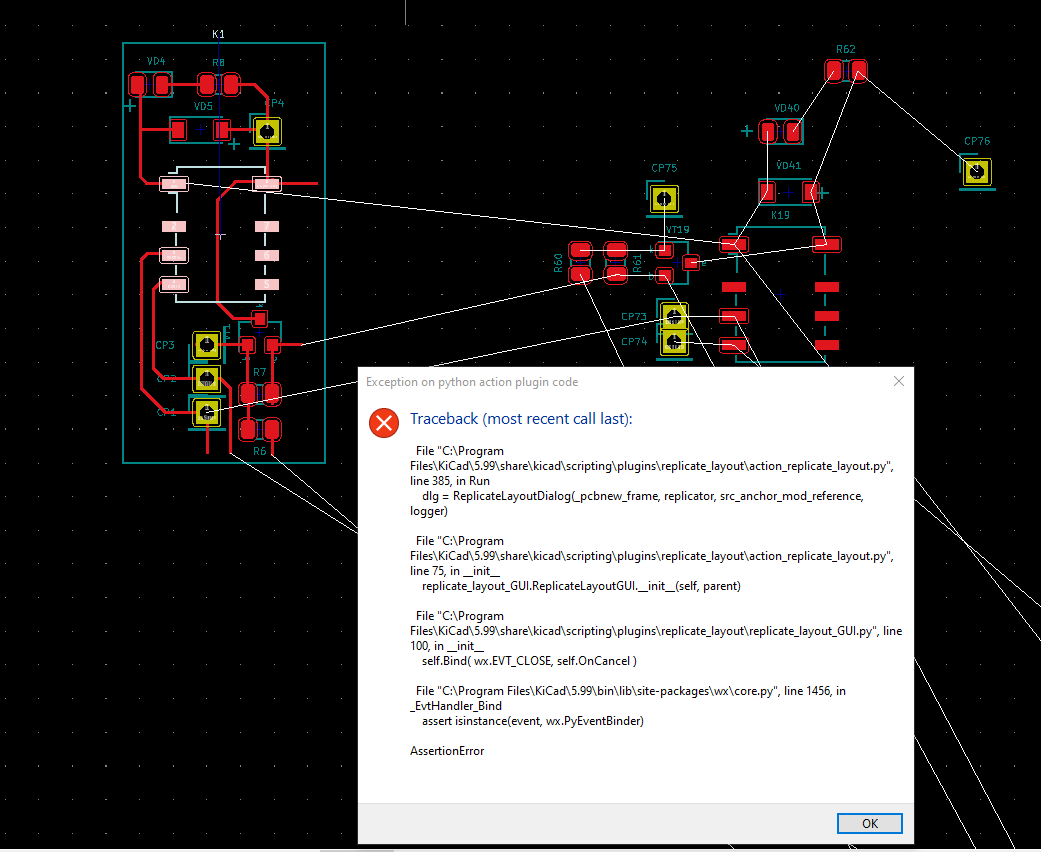
stend_e3/stend_main1/~rawings/replication_layout/~4_error.png
