antondrroid/V_meter_013/stend_e3/stend_main1/~rawings/replication_layout/~5.PNG

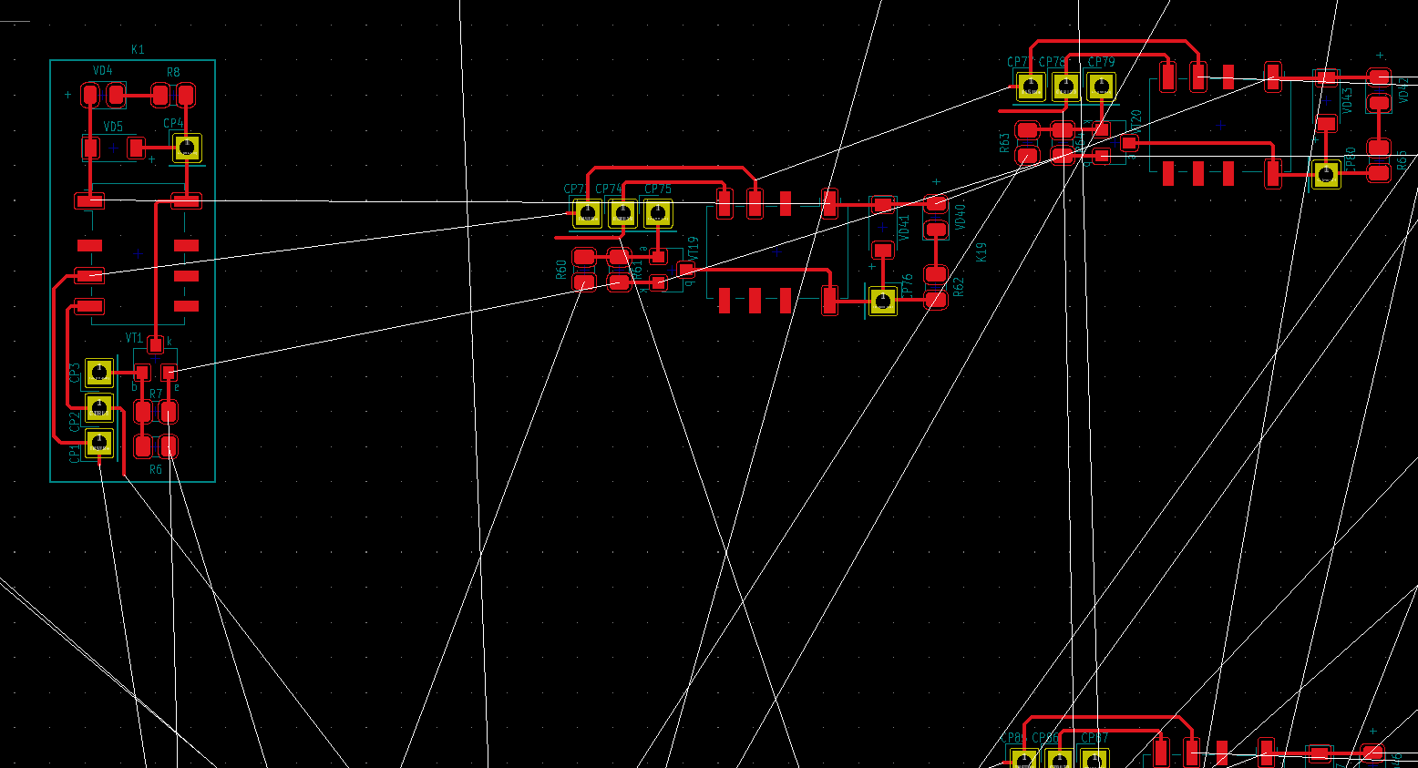
stend_e3/stend_main1/~rawings/replication_layout/~5.PNG
