antondrroid/V_meter_013/stend_e3/stend_main1/~rawings/SW_symbol.png

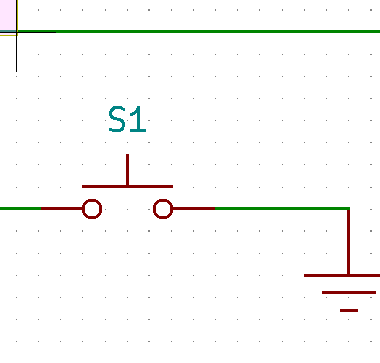
stend_e3/stend_main1/~rawings/SW_symbol.png
