antondrroid/V_meter_013/stend_e3/stend_main1/~rawings/~RROR_2.PNG

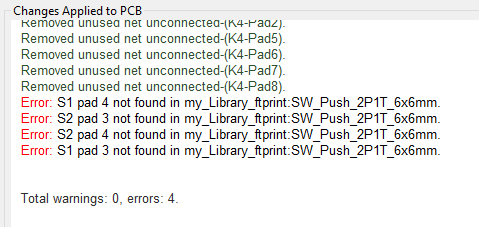
stend_e3/stend_main1/~rawings/~RROR_2.PNG
