antondrroid/V_meter_013/stend_e3/stend_main1/~rawings/~stsheet.png

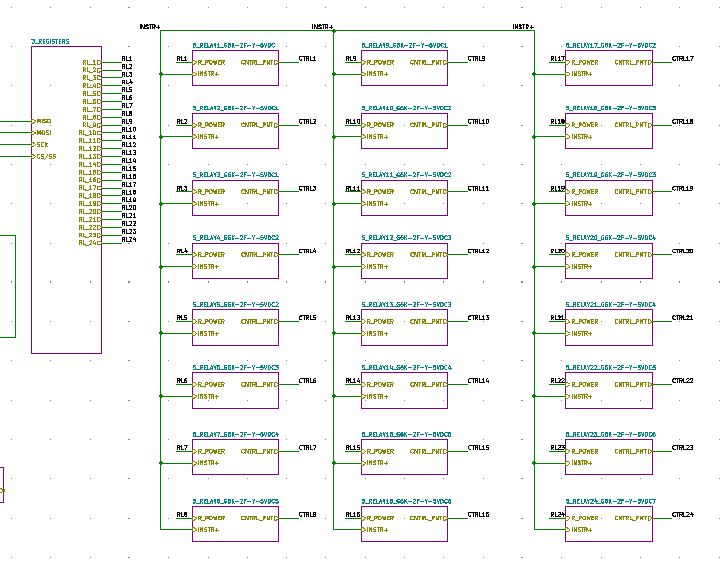
stend_e3/stend_main1/~rawings/~stsheet.png
