antondrroid/V_meter_013/stend_e3/stend_main1/~rawings/~W.PNG

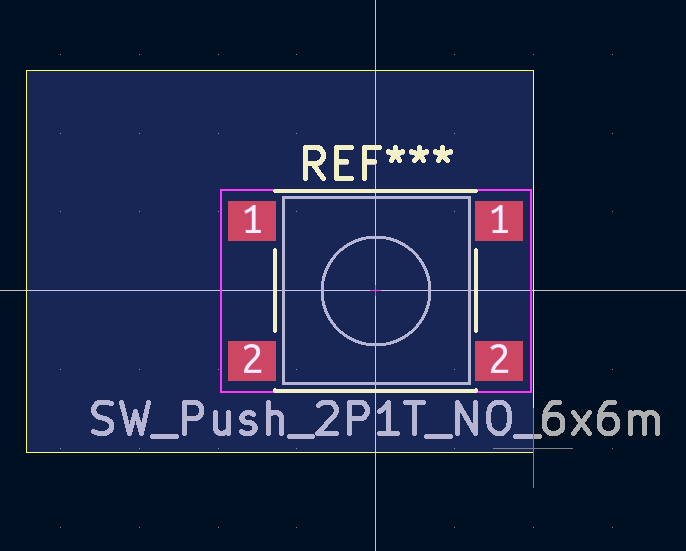
stend_e3/stend_main1/~rawings/~W.PNG
