antondrroid/V_meter_013/stend_e3/stend_main3/~rawings/~illing/3_after_filling.png

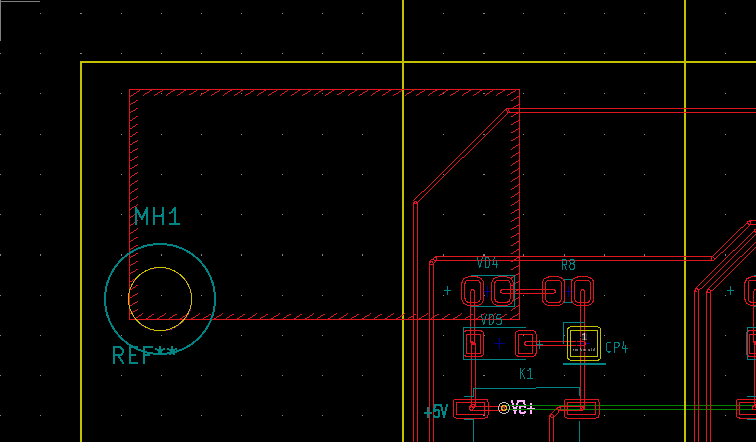
stend_e3/stend_main3/~rawings/~illing/3_after_filling.png
