antondrroid/V_meter_013/stend_e3/stend_main3/~rawings/~illing/3_allowed_all.png

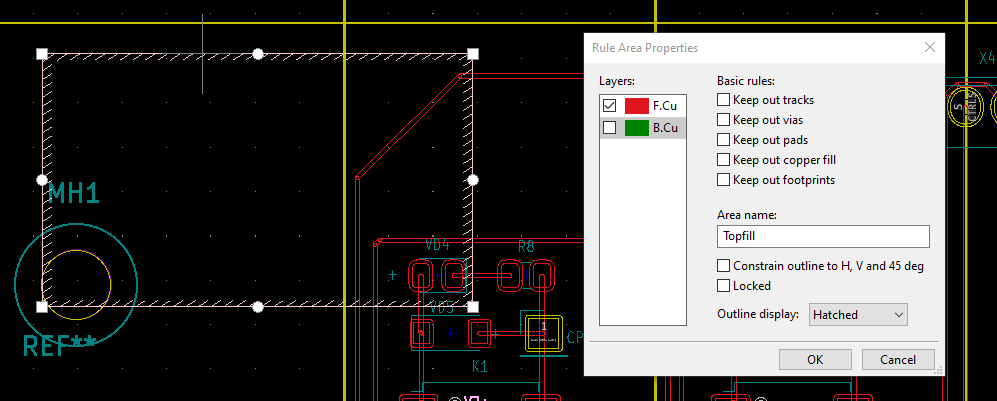
stend_e3/stend_main3/~rawings/~illing/3_allowed_all.png
