antondrroid/V_meter_013/stend_e3/stend_main3/~rawings/~illing/5_fill_F_silck.png

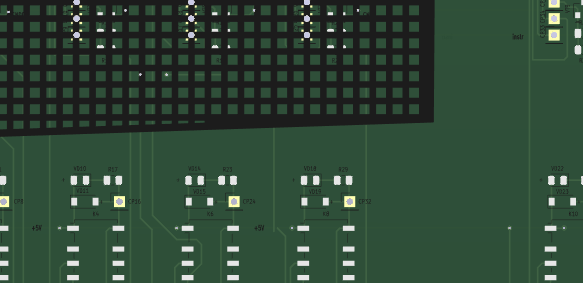
stend_e3/stend_main3/~rawings/~illing/5_fill_F_silck.png
