antondrroid/V_meter_013/stend_e3/stend_main3/~rawings/~illing/6_filling zone iside rule zone.png

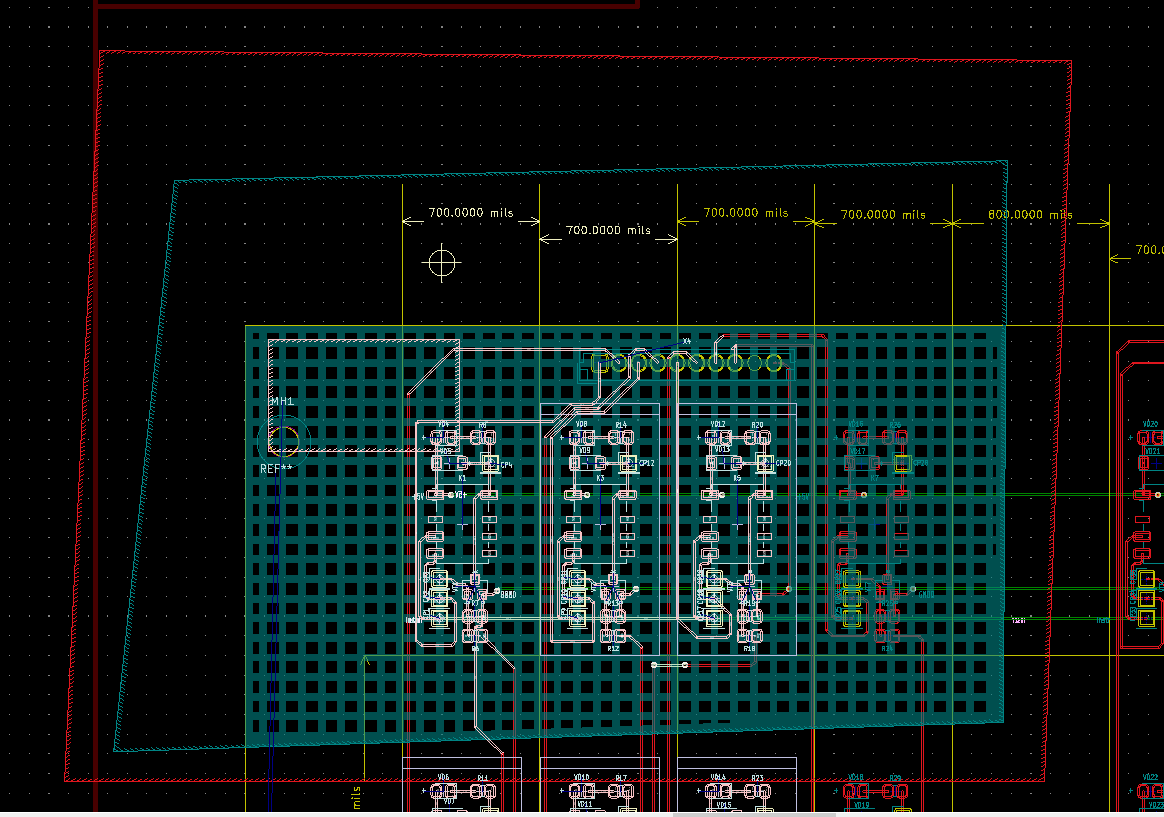
stend_e3/stend_main3/~rawings/~illing/6_filling zone iside rule zone.png
