antondrroid/V_meter_013/stend_e3/stend_main3/~rawings/~illing/7_filling _triangle y_by cutout.png

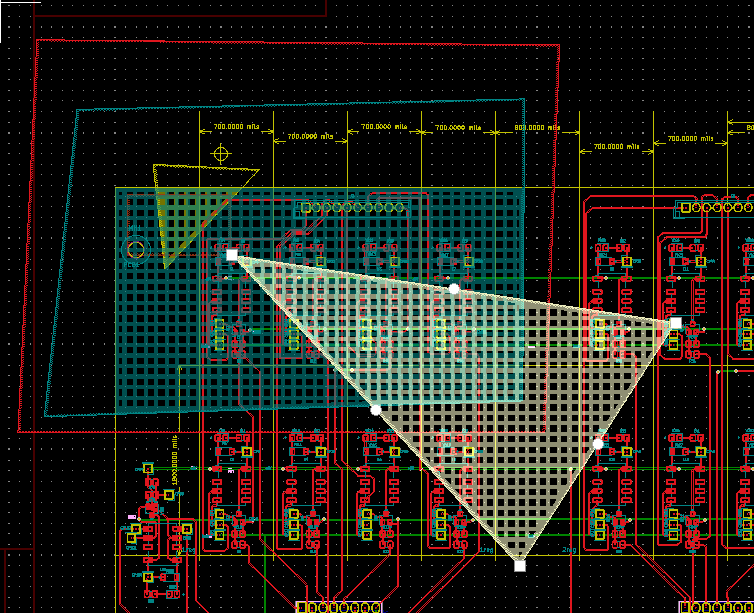
stend_e3/stend_main3/~rawings/~illing/7_filling _triangle y_by cutout.png
