antondrroid/V_meter_013/stend_e3/stend_main3/~rawings/~illing/8_success.png

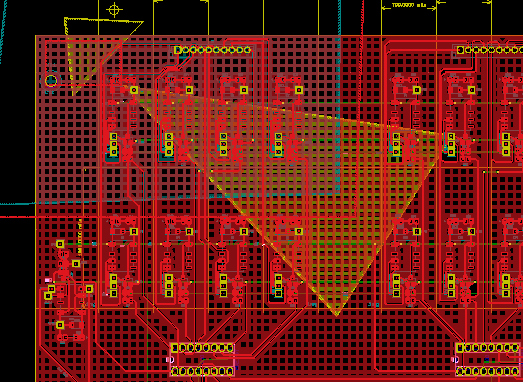
stend_e3/stend_main3/~rawings/~illing/8_success.png
