antondrroid/V_meter_013/stend_e3/stend_main3/~rawings/~illing/rules checks1.png

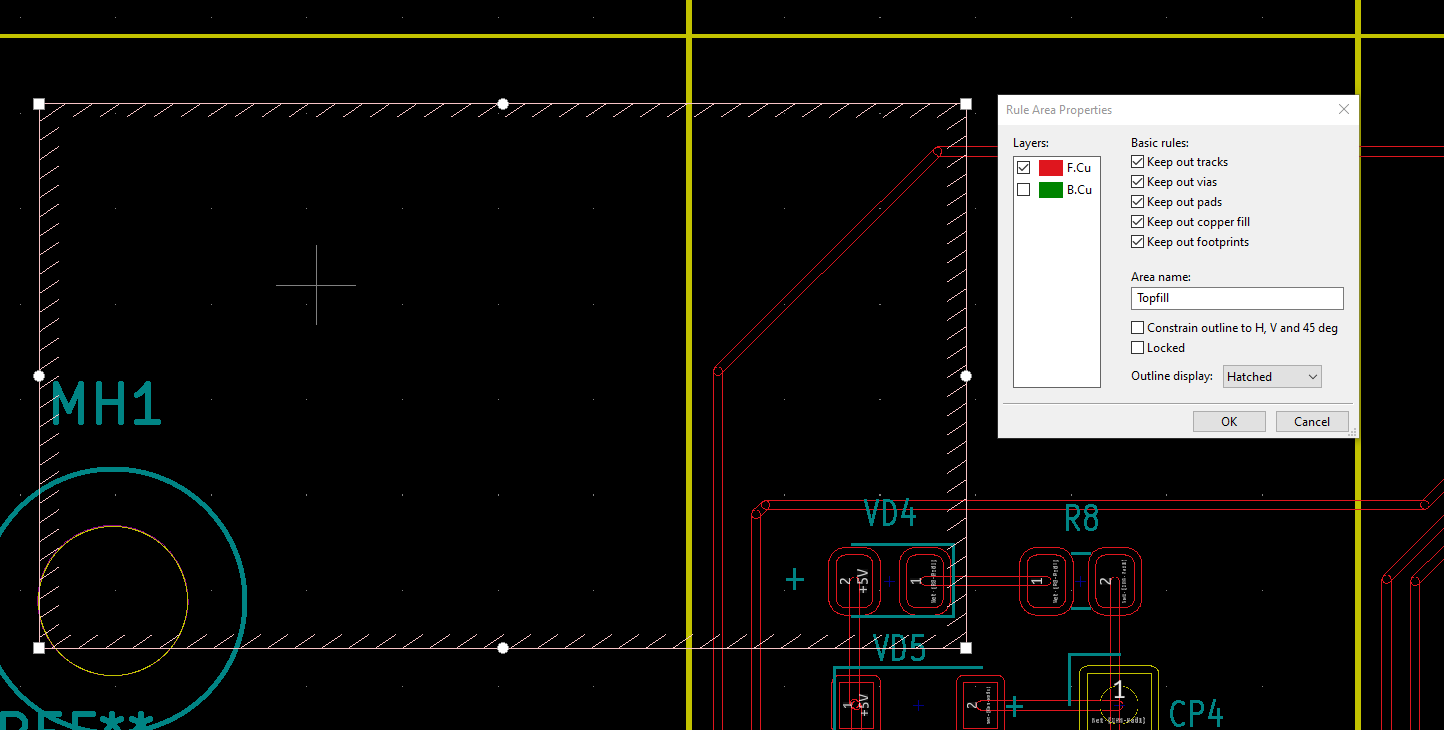
stend_e3/stend_main3/~rawings/~illing/rules checks1.png
