antondrroid/V_meter_013/stend_e3/stend_main3/~rawings/~lcpcb.png

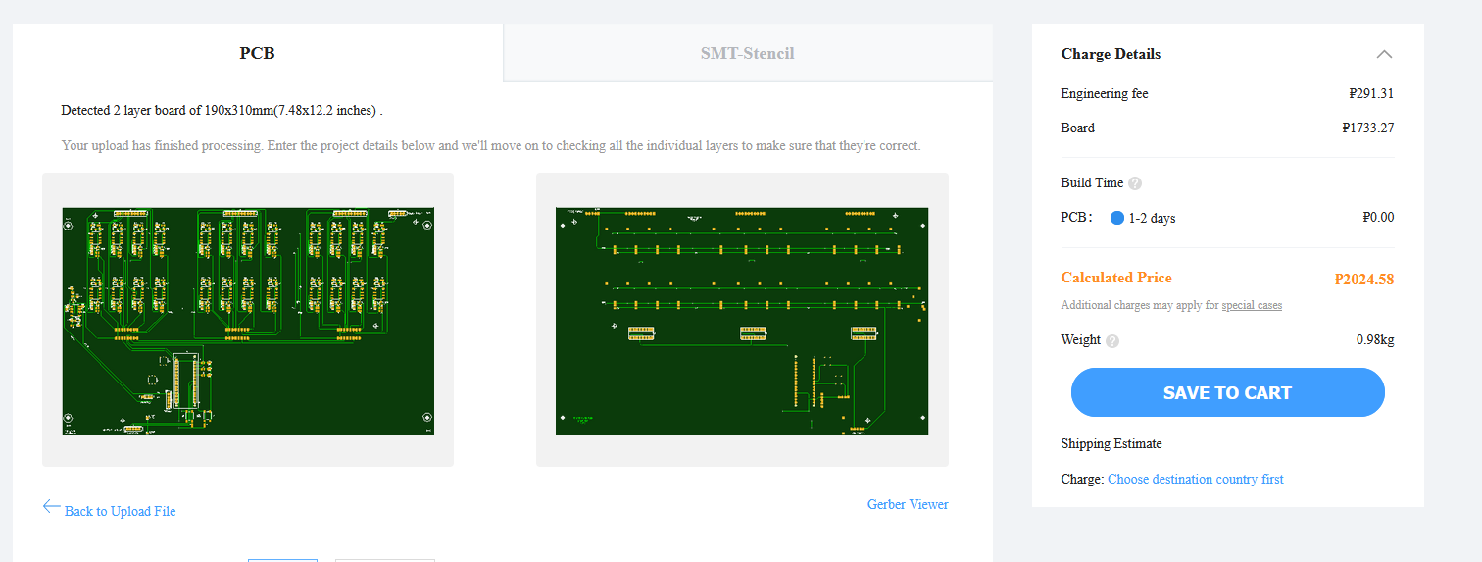
stend_e3/stend_main3/~rawings/~lcpcb.png
