antondrroid/V_meter_013/stend_e3/stend_main4_dummy/~rawings/resistor over head value/2021-09-22 09_53_16-Window.png

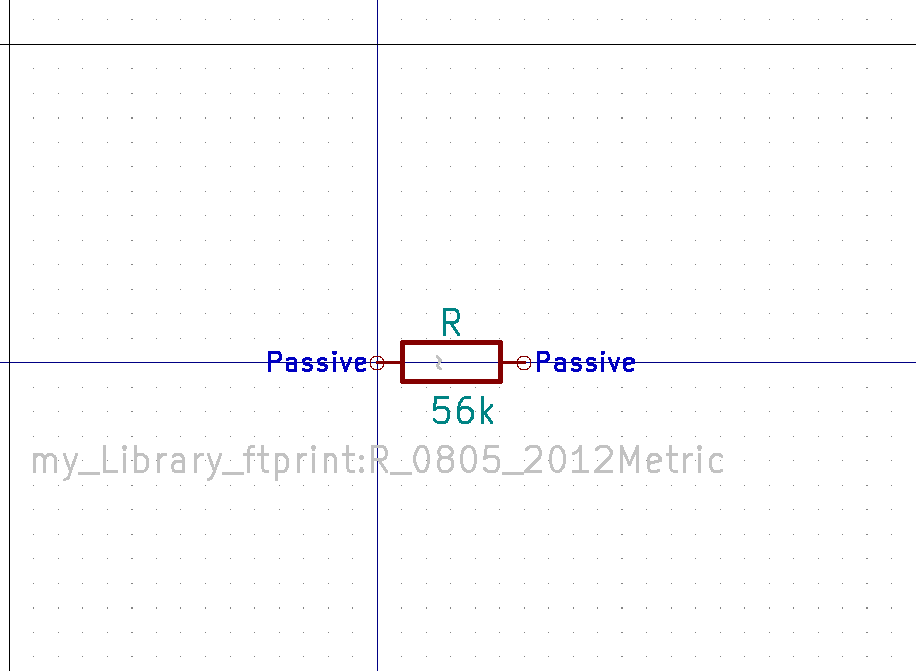
stend_e3/stend_main4_dummy/~rawings/resistor over head value/2021-09-22 09_53_16-Window.png
