antondrroid/V_meter_013/stend_e3/stend_main4_dummy/~rawings/spare_screenshots/~.PNG

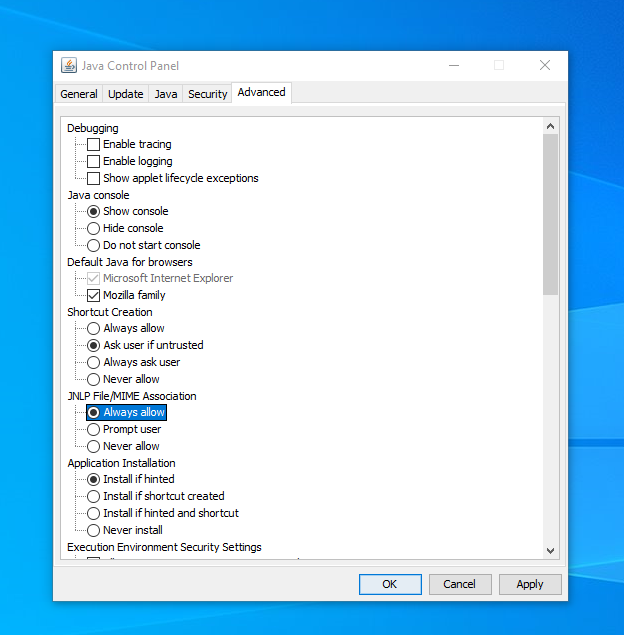
stend_e3/stend_main4_dummy/~rawings/spare_screenshots/~.PNG
