antondrroid/V_meter_013/stend_e3/stend_main4_dummy/~rawings/~3/registers.png

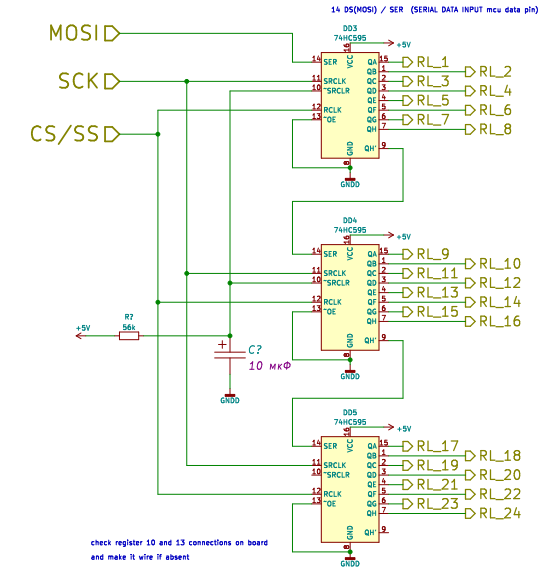
stend_e3/stend_main4_dummy/~rawings/~3/registers.png
