antondrroid/V_meter_013/stend_e3/stend_main/~rawings/replication_layout/layout_sample.png

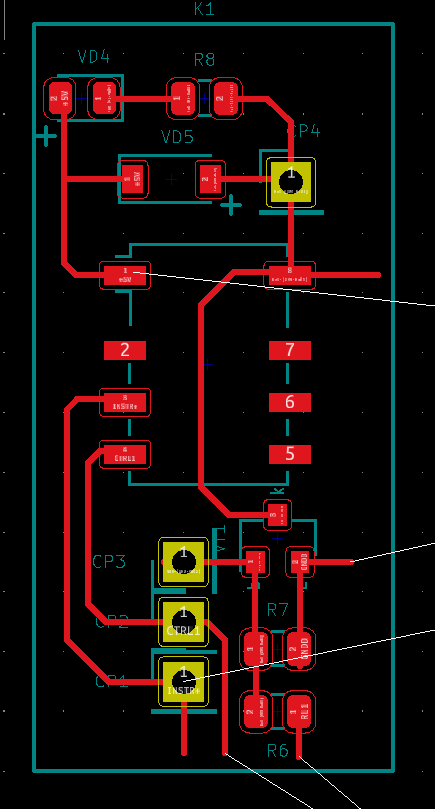
stend_e3/stend_main/~rawings/replication_layout/layout_sample.png
