antondrroid/V_meter_013/Spare_parts/orders _china_1st_board/order2_china_corrected_2.pdf

order2

Page 1

## Заказ 2

назначение | изделие RUST.ZM-12.402.00.00
наименование | Кол-во Цена руб
Модуль микроконтроллера | 2 | 520
Разьем BNC male | 5 | 262
кабель USB/USB B | 1 | 159
resistor 12kom 2 kom SMD (1 набор 300шт) | 1 | 130
resistor 12kom 2 kom углеродные (1 набор400шт)1 | 1 | 140
транзистор 2sc1815HF SOT23 набор 100шт1 | 1 | 105
| 1 | 147
XH2.54 /5/10 p 2,54 мм комплект разъем JST 10шт | 1 | 160
всего: | 1623

10 штук Разъем PBS-1x16 (PBS-16)шаг 2.54 мм
