antondrroid/V_meter_013/screen/~roteus/Component.png

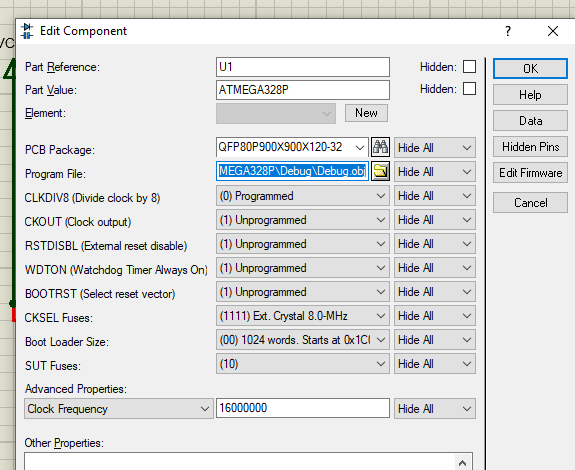
screen/~roteus/Component.png
