antondrroid/V_meter_013/Spare_parts/chipdip_vs_ali/2021-09-12 16_38_40-Window.png

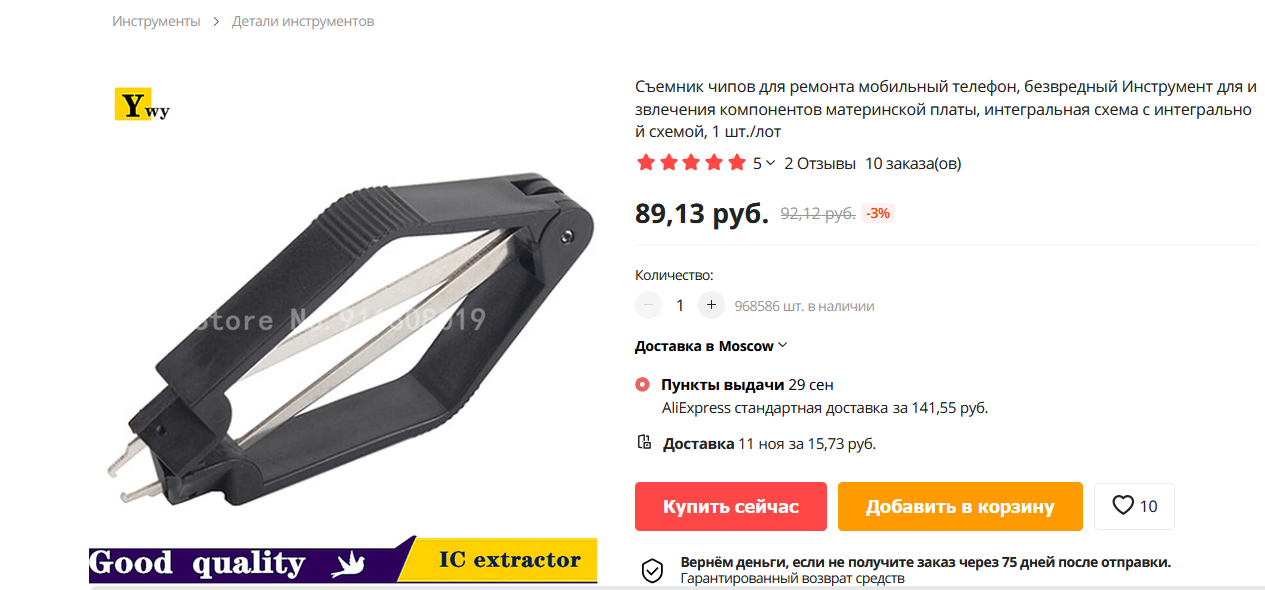
Spare_parts/chipdip_vs_ali/2021-09-12 16_38_40-Window.png
