antondrroid/V_meter_013/Spare_parts/orders _china_1st_board/2021-09-09 19_03_33-Припой Goot SE-06006 0,6 мм 60% олово 40% свинец 100г 48м, VNB _ купить в розниц.png

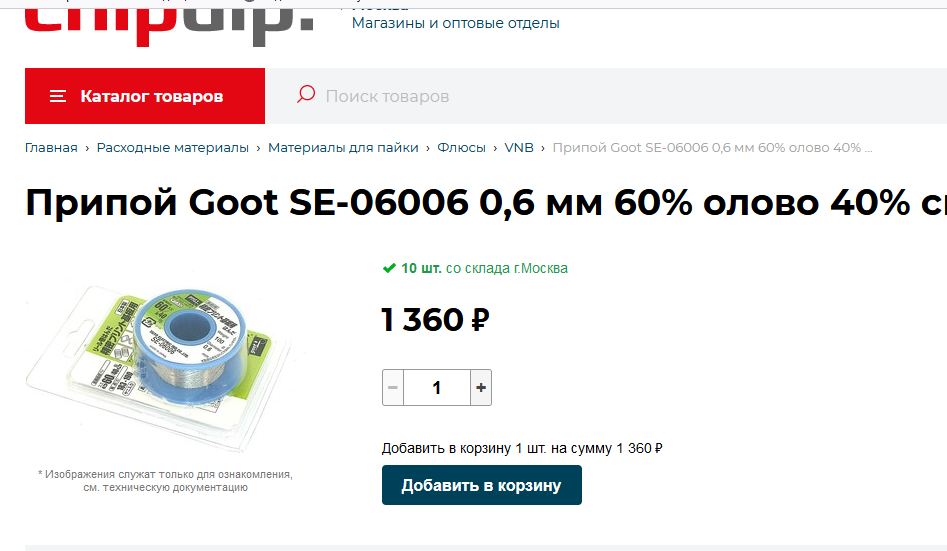
Spare_parts/orders _china_1st_board/2021-09-09 19_03_33-Припой Goot SE-06006 0,6 мм 60% олово 40% свинец 100г 48м, VNB _ купить в розниц.png
