antondrroid/V_meter_013/Spare_parts/orders _china_1st_board/2021-09-09 19_05_35-My AliExpress _ Manage Orders — Mozilla Firefox.png

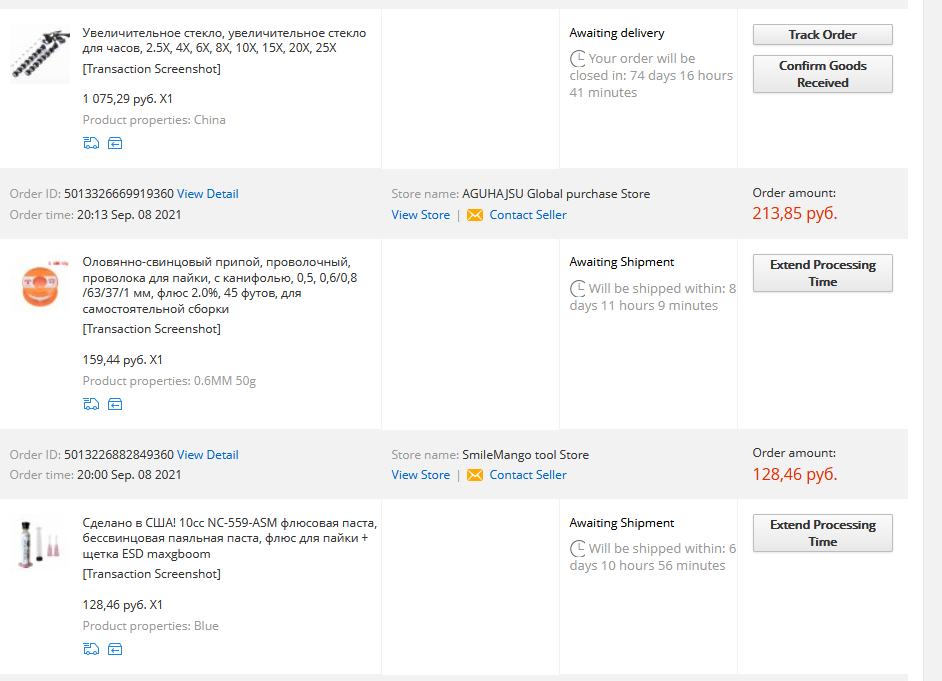
Spare_parts/orders _china_1st_board/2021-09-09 19_05_35-My AliExpress _ Manage Orders — Mozilla Firefox.png
