antondrroid/V_meter_013/Spare_parts/orders _china_1st_board/order2_russia.png

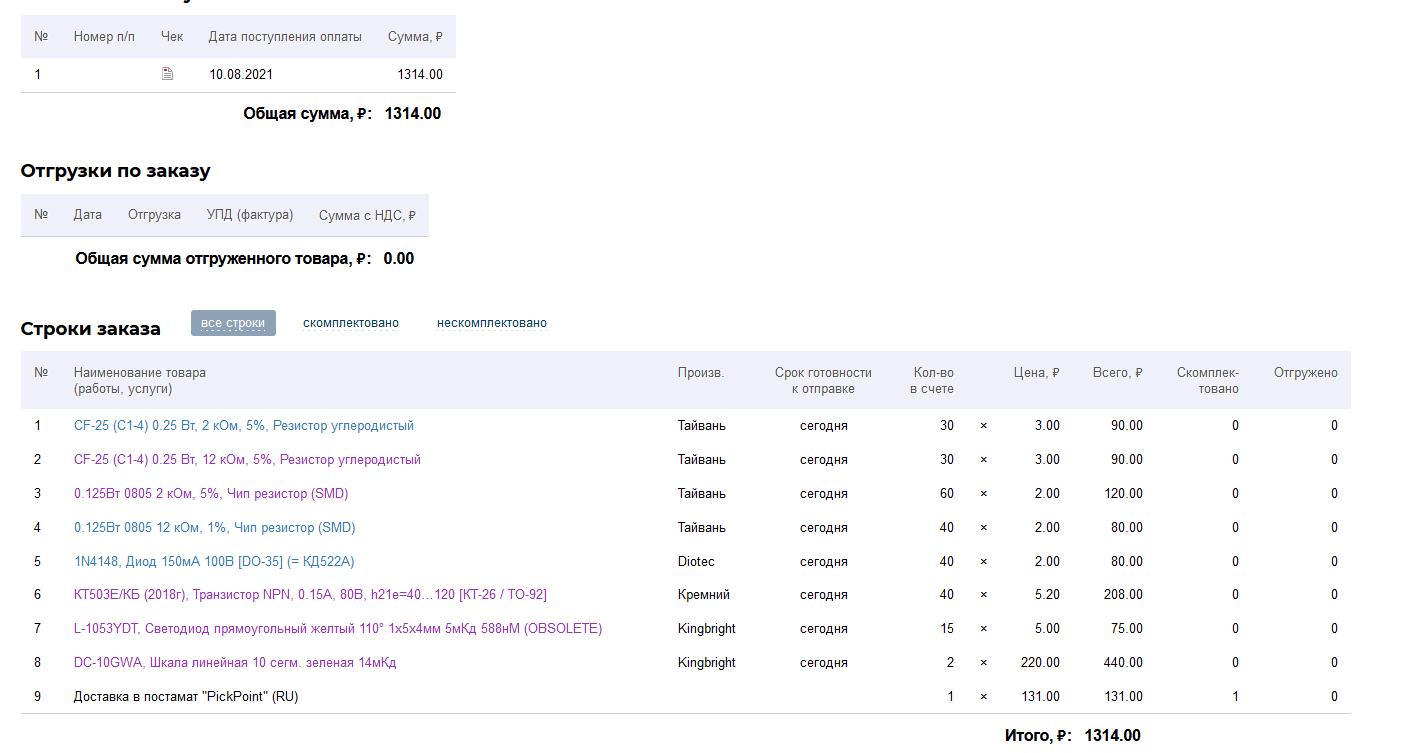
Spare_parts/orders _china_1st_board/order2_russia.png
