antondrroid/V_meter_013/Spare_parts/orders_china_2and3_boards/~3r.png

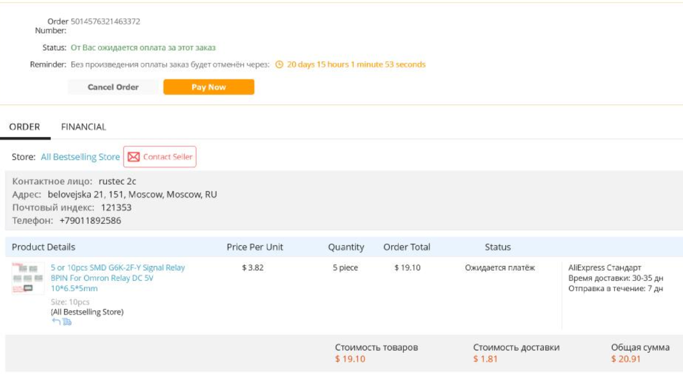
Spare_parts/orders_china_2and3_boards/~3r.png
