antondrroid/V_meter_013/Spare_parts/orders_china_2and3_boards/~nv.png

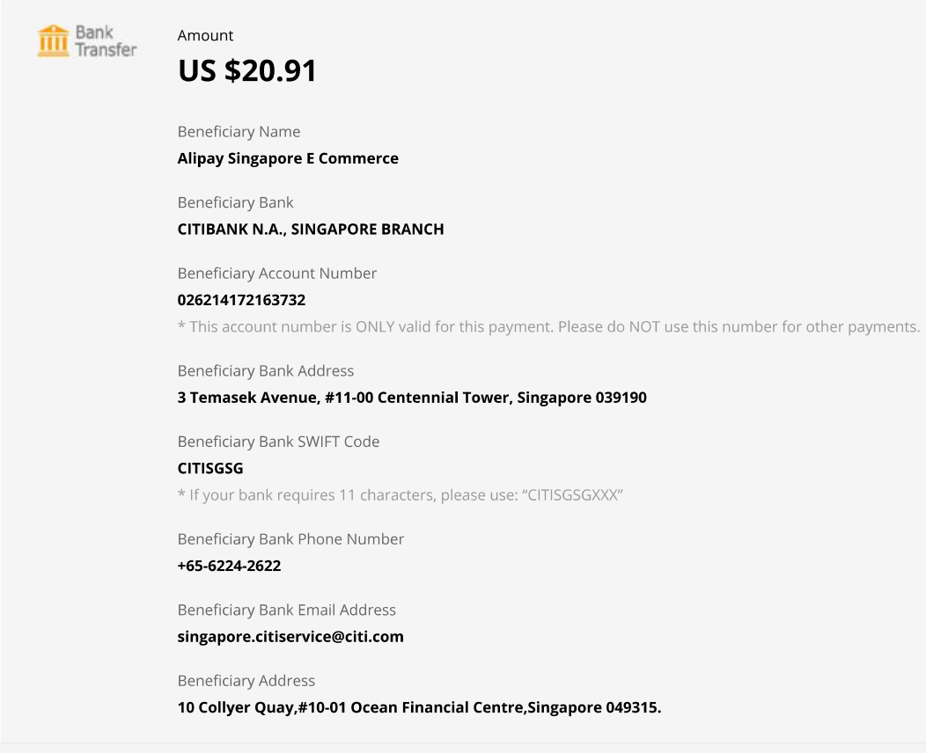
Spare_parts/orders_china_2and3_boards/~nv.png
