antondrroid/V_meter_013/Spare_parts/zacaz plat/board_china/invoice_sample.png

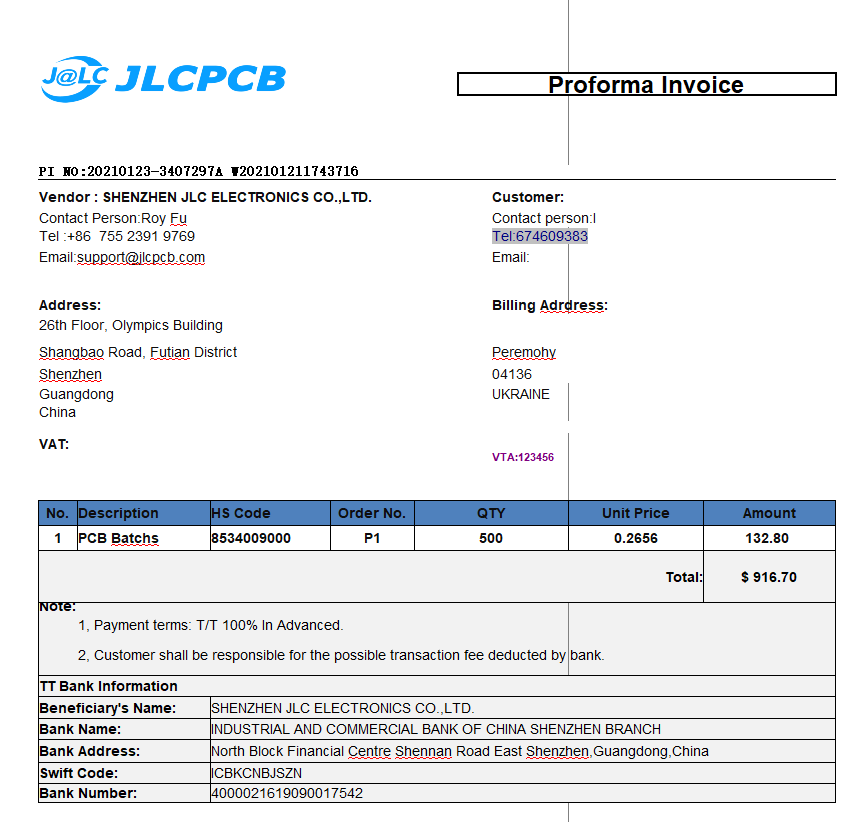
Spare_parts/zacaz plat/board_china/invoice_sample.png
