antondrroid/V_meter_013/Spare_parts/zacaz plat/board_china/screen_68_order.png

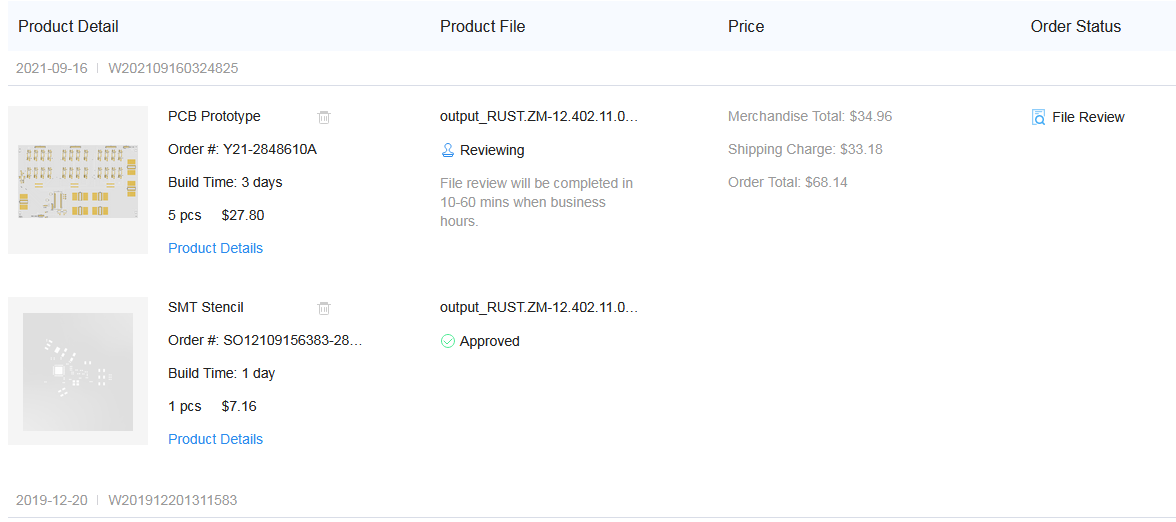
Spare_parts/zacaz plat/board_china/screen_68_order.png
