antondrroid/V_meter_013/Spare_parts/zacaz plat/invoice_resonit/invoice_resonit.png

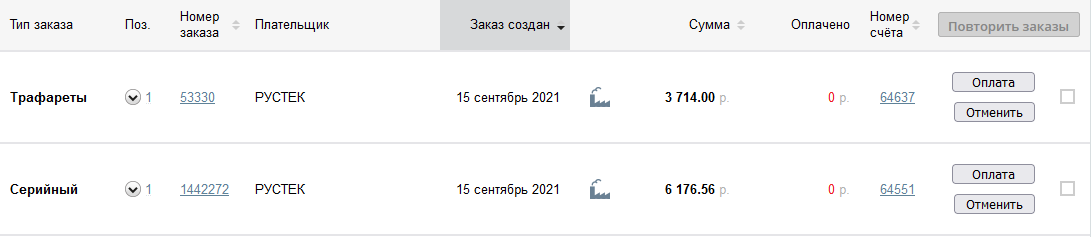
Spare_parts/zacaz plat/invoice_resonit/invoice_resonit.png
