antondrroid/V_meter_013/stend_e3/stend_main3/~rawings/order for choise/~lt.png

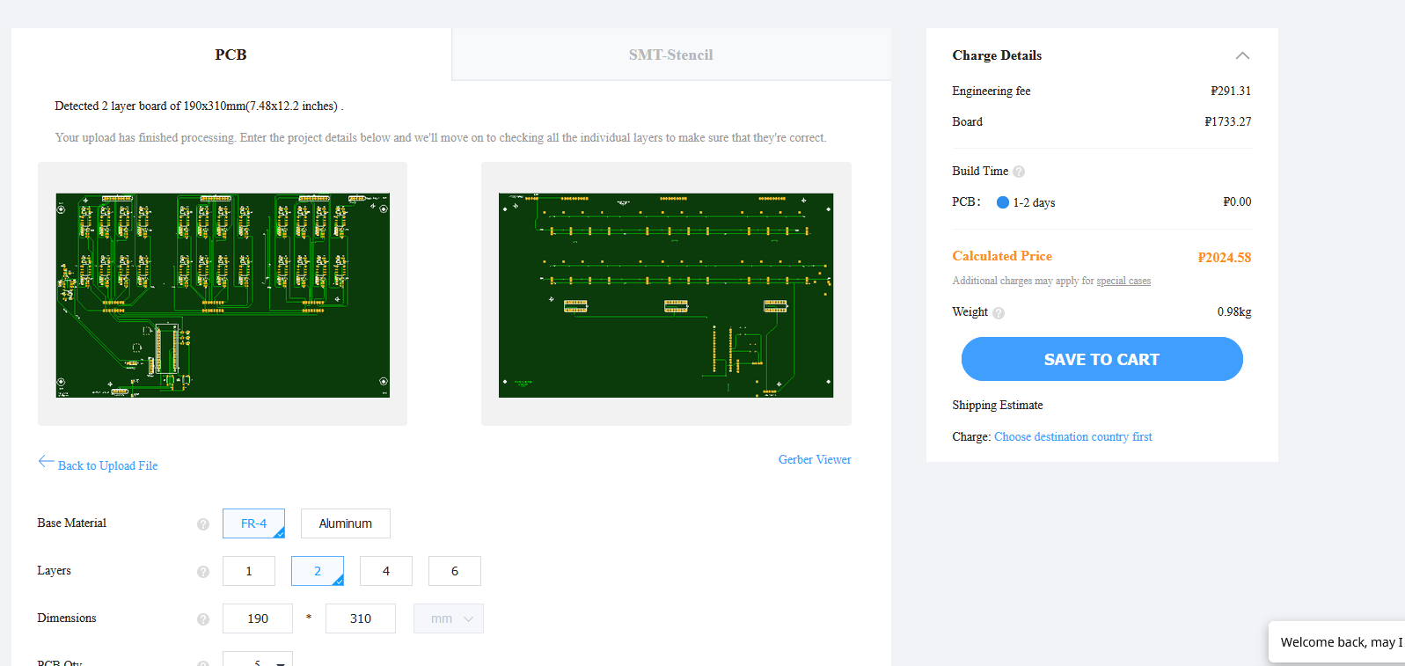
stend_e3/stend_main3/~rawings/order for choise/~lt.png
