antondrroid/V_meter_013/stend_e3/stend_main3_stencil/~rawings/order for choise/2021-09-15 19_34_15-Window.png

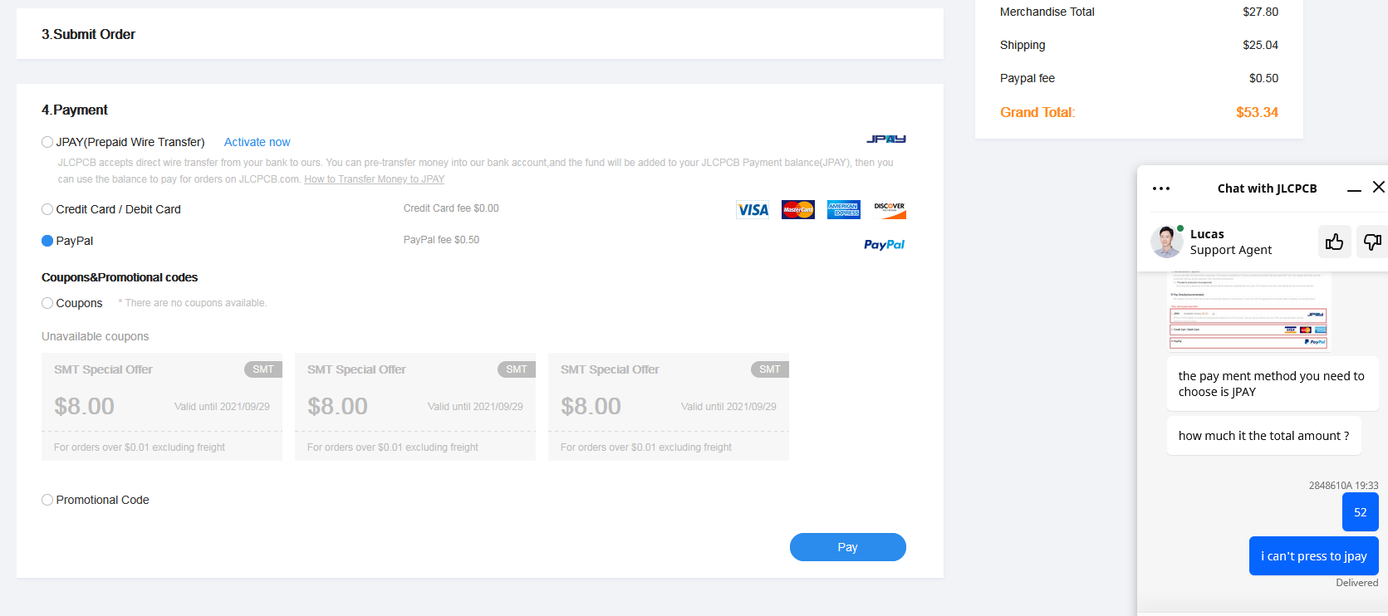
stend_e3/stend_main3_stencil/~rawings/order for choise/2021-09-15 19_34_15-Window.png
