antondrroid/V_meter_013/stend_e3/stend_main3_stencil/~rawings/order for choise/~rders.png

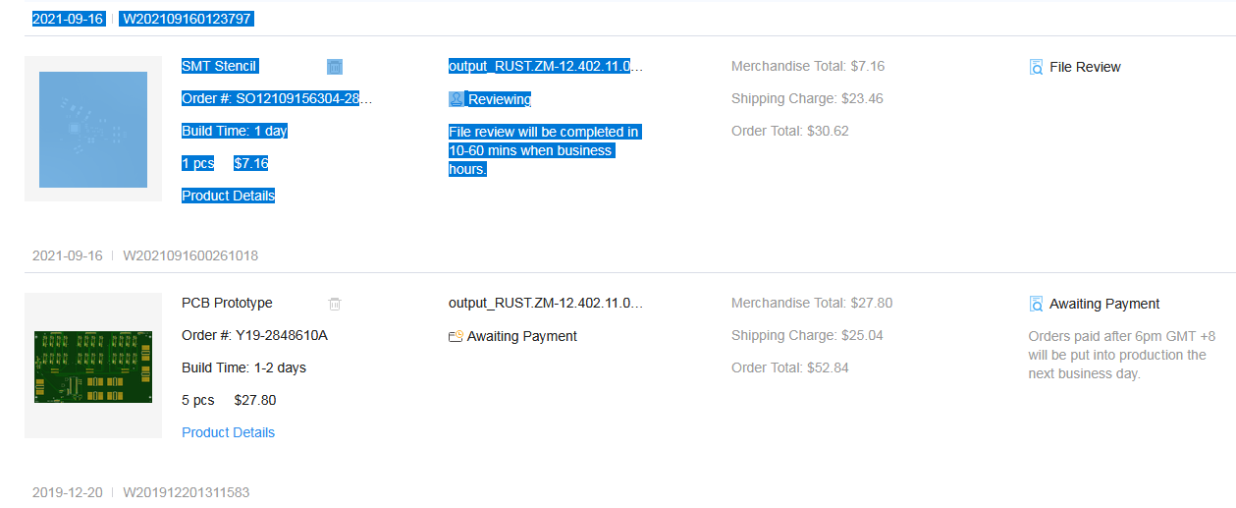
stend_e3/stend_main3_stencil/~rawings/order for choise/~rders.png
