antondrroid/V_meter_013/DATA/Register/758725.013Э3_V6.pdf

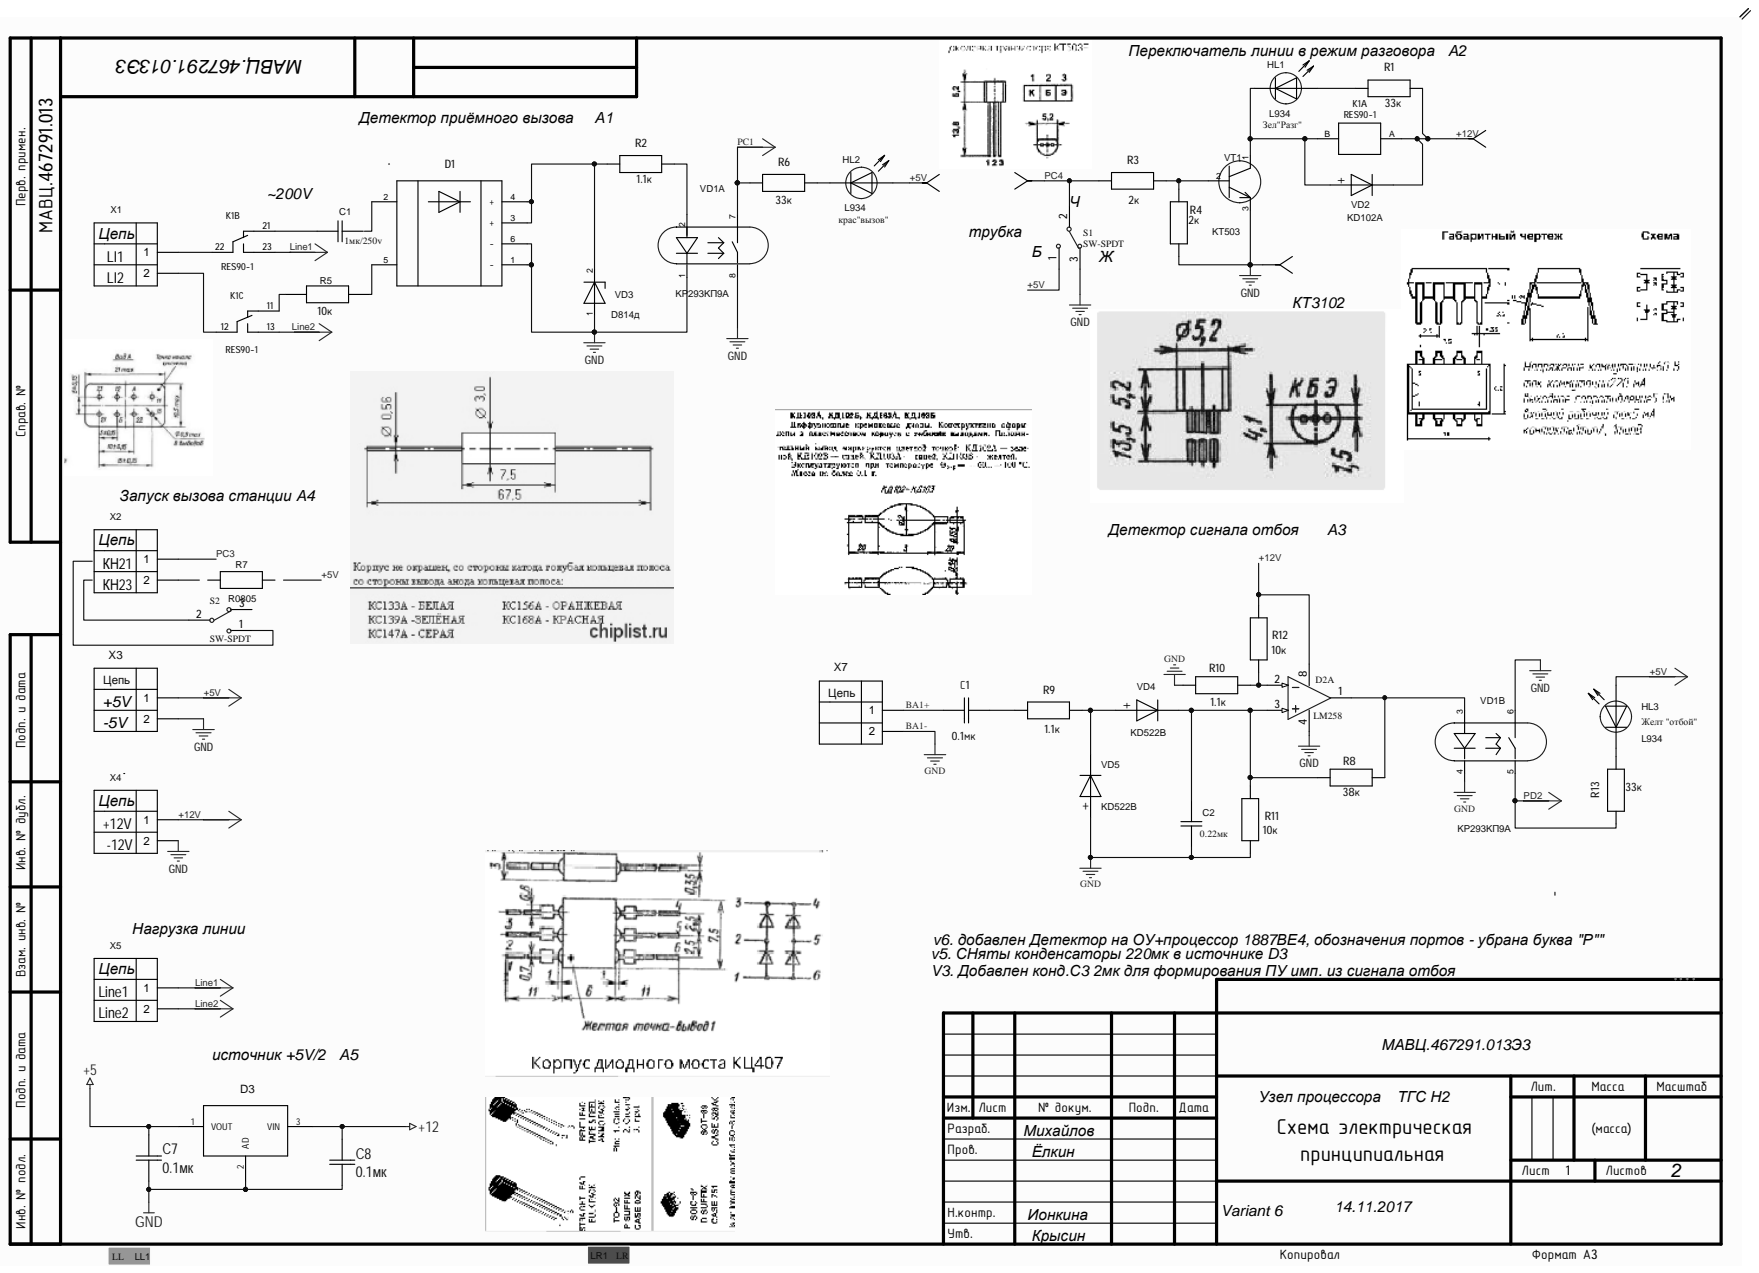
[picture p109: page 1]

Переключатель линии в режим разговора

Инв. № подл. Инв. № дубл. Подп. и дата Взам. инв. № Подп. и дата Перв. примен. Справ. №

Цепь
LI1 | 1
LI2 | 2

КН21 | 1
КН23 | 2

+5V | 1
-5V | 2

+12V | 1
-12V | 2

v6. добавлен Детектор на ОУ+процессор 1887ВЕ4, обозначения портов - убрана буква "Р""
v5. СНяты конденсаторы 220мк в источнике D3
V3. Добавлен конд.С3 2мк для формирования ПУ имп. из сигнала отбоя

Line1 | 1
Line2 | 2

МАВЦ.467291.013Э3

Узел процессора ТГС Н2 Схема электрическая принципиальная | Лит. | Масса | Масштаб

Изм. | Лист | № докум. | Подп. | Дата | | | | | (масса)
Разраб. | | Михайлов
Пров. | | Ёлкин

Лист 1 | 2 Листов

Н.контр. | Ионкина
Утв. | Крысин

14.11.2017 Variant 6
