antondrroid/V_meter_013/Spare_parts/orders_china_2and3_boards/relays_for2and3_boards.pdf

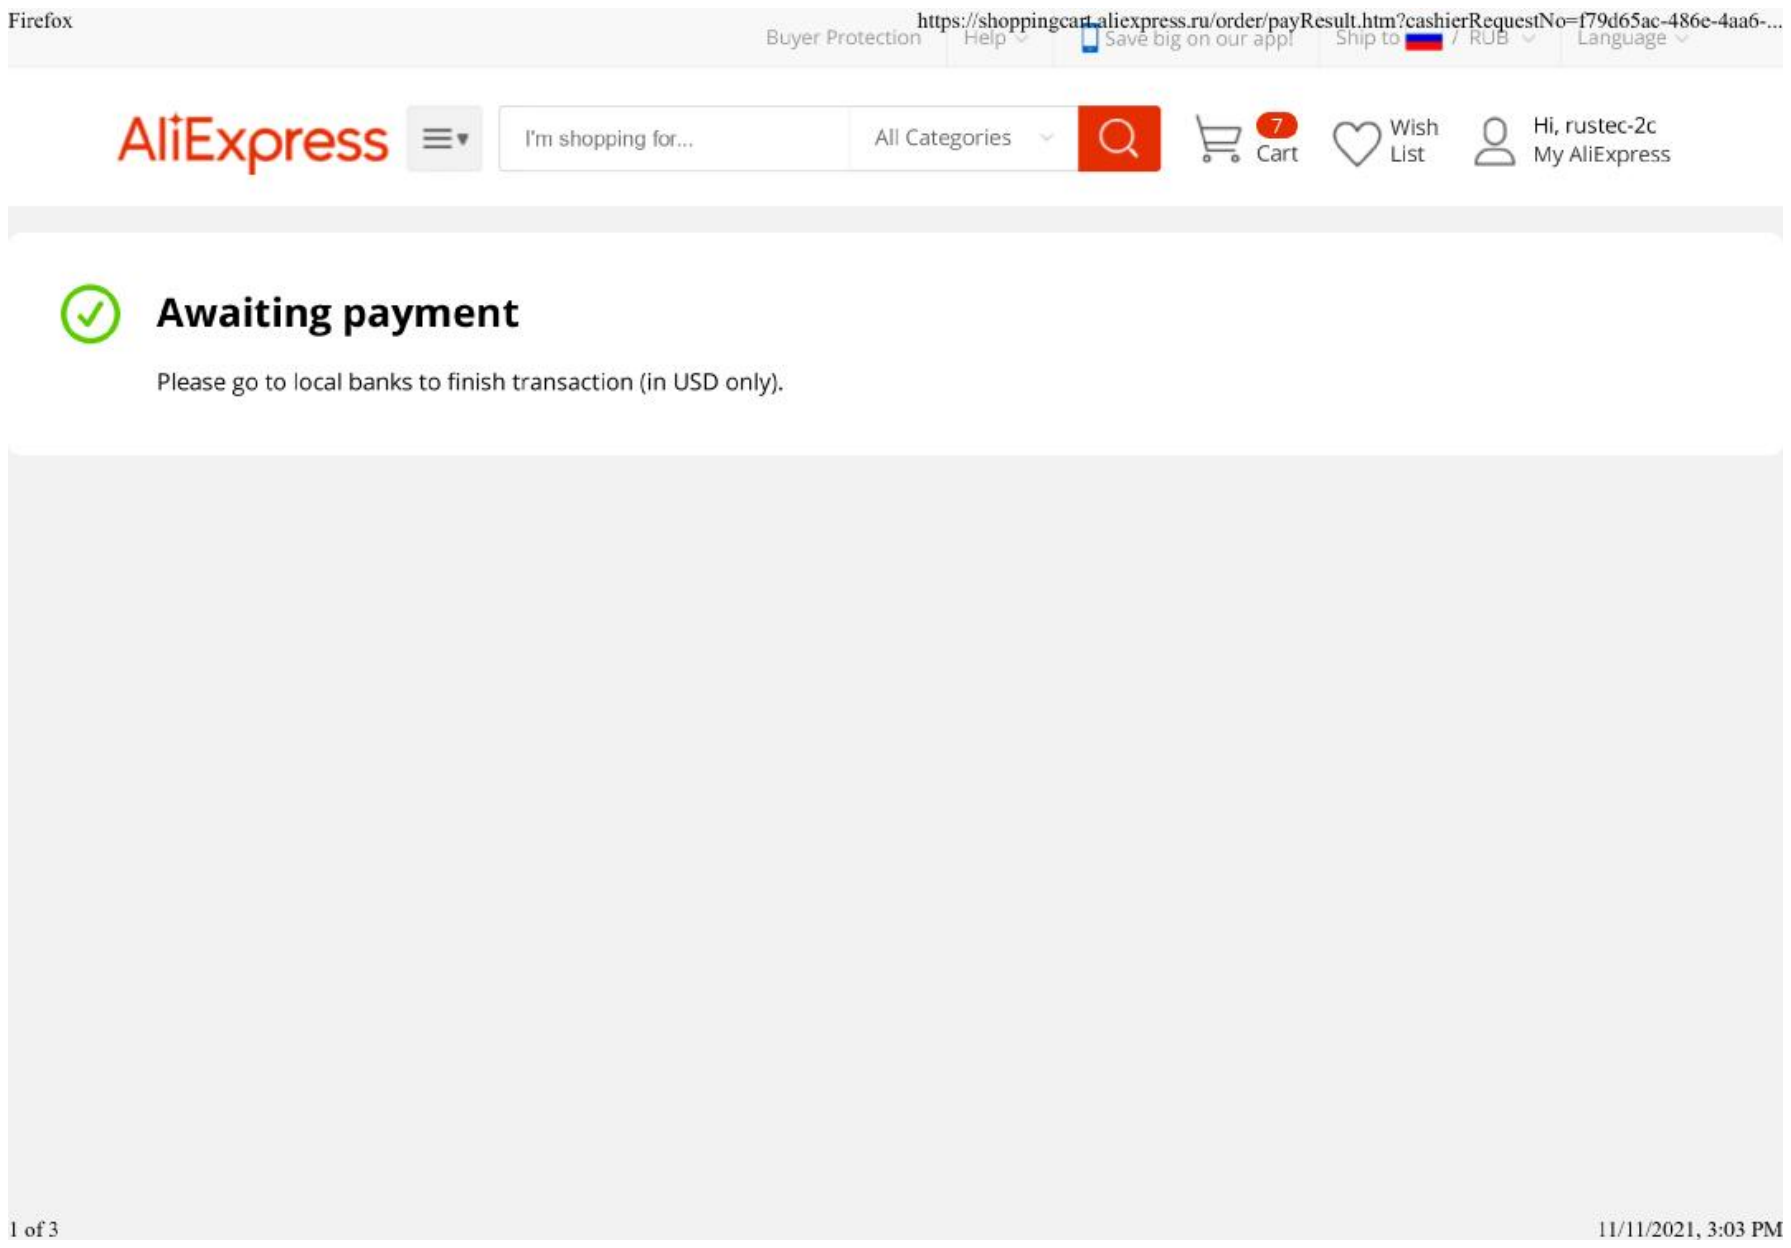
[picture p110: page 1]

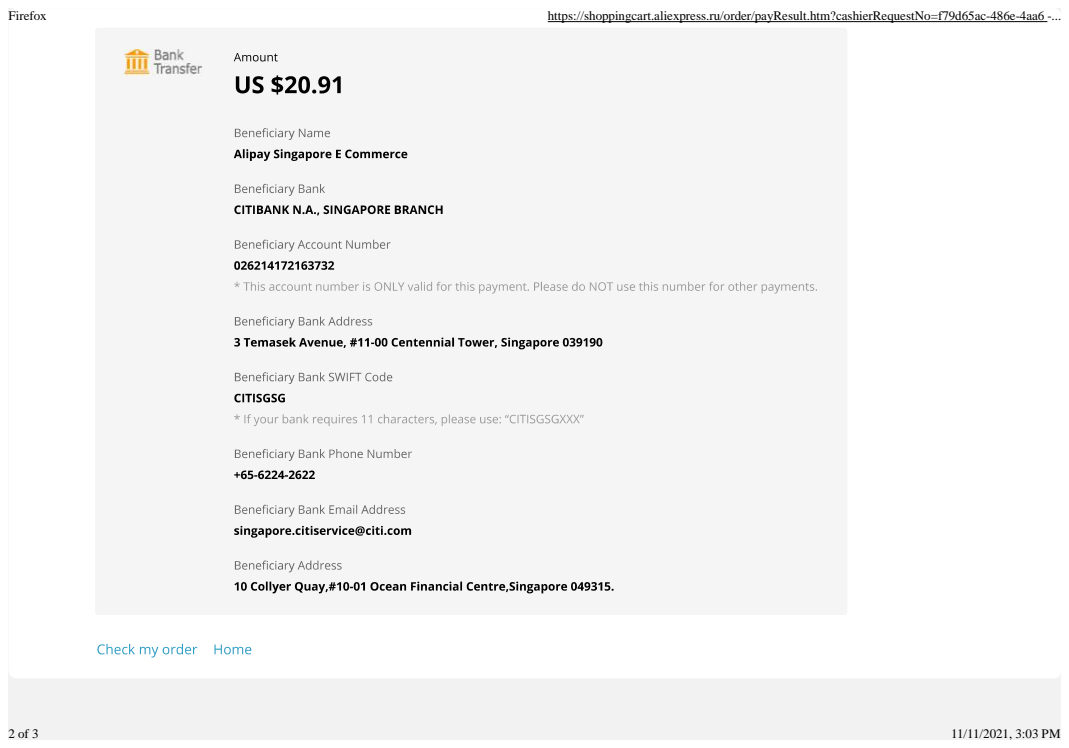
[picture p111: page 2]
Firefox; https://shoppingcart.aliexpress.ru/order/payResult.htm?cashierRequestNo=f79d65ac-486e-4aa6 -...

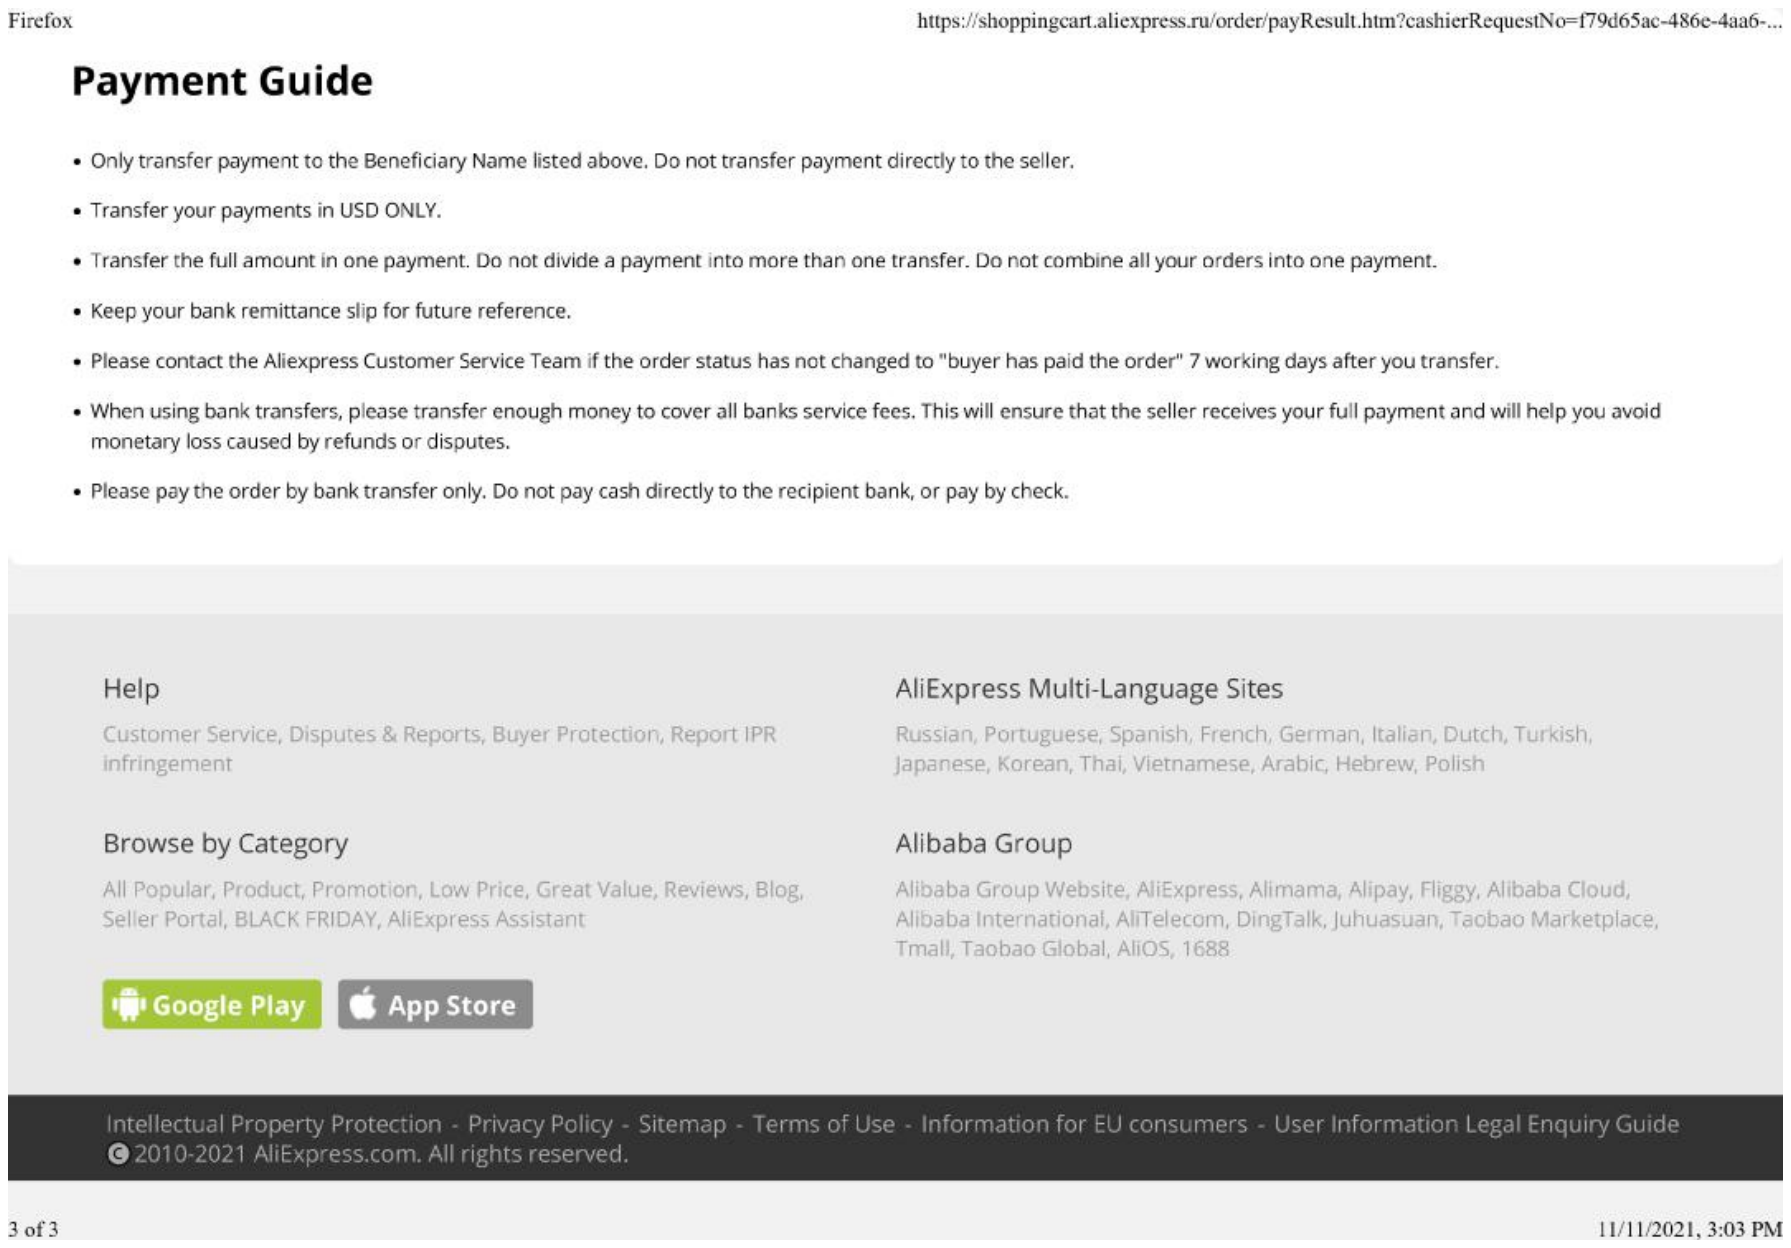
[picture p112: page 3]
