antondrroid/V_meter_013/Spare_parts/orders_china_2and3_boards/relays_for2and3_boards_withorder.pdf

Firefox; https://shoppingcart.aliexpress.ru/order/payResult.htm?cashierRequestNo=f79d65ac-486e-4aa6 -...


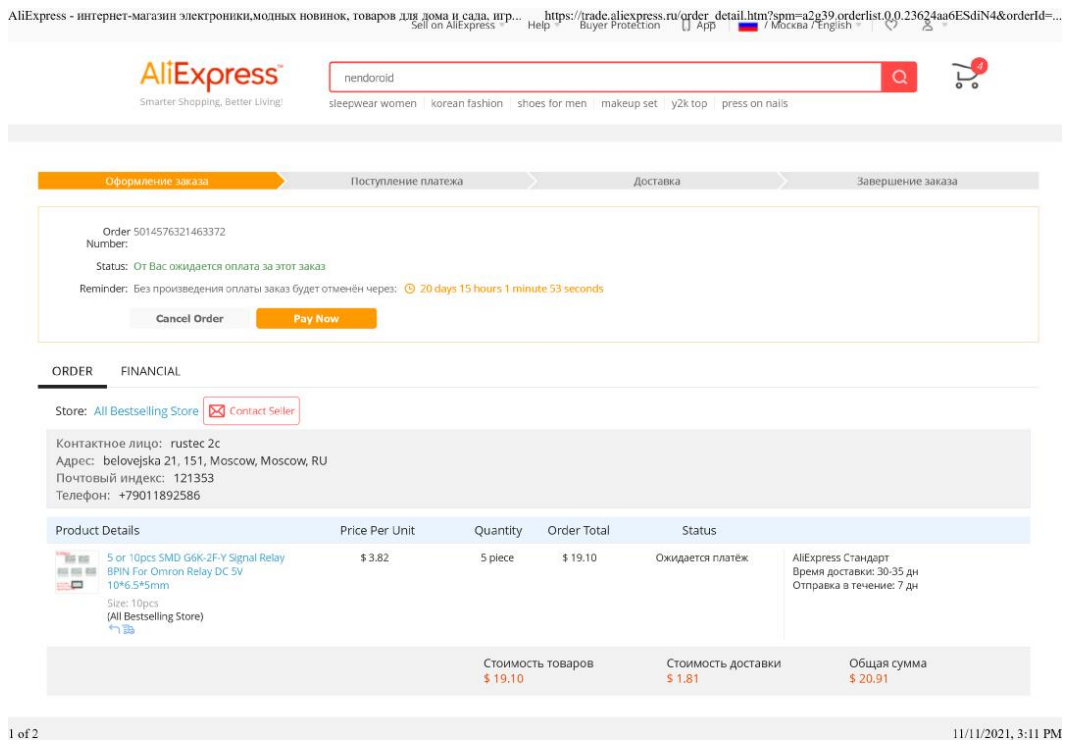
[picture p113: page 4]
Cancel Order; Pay Now

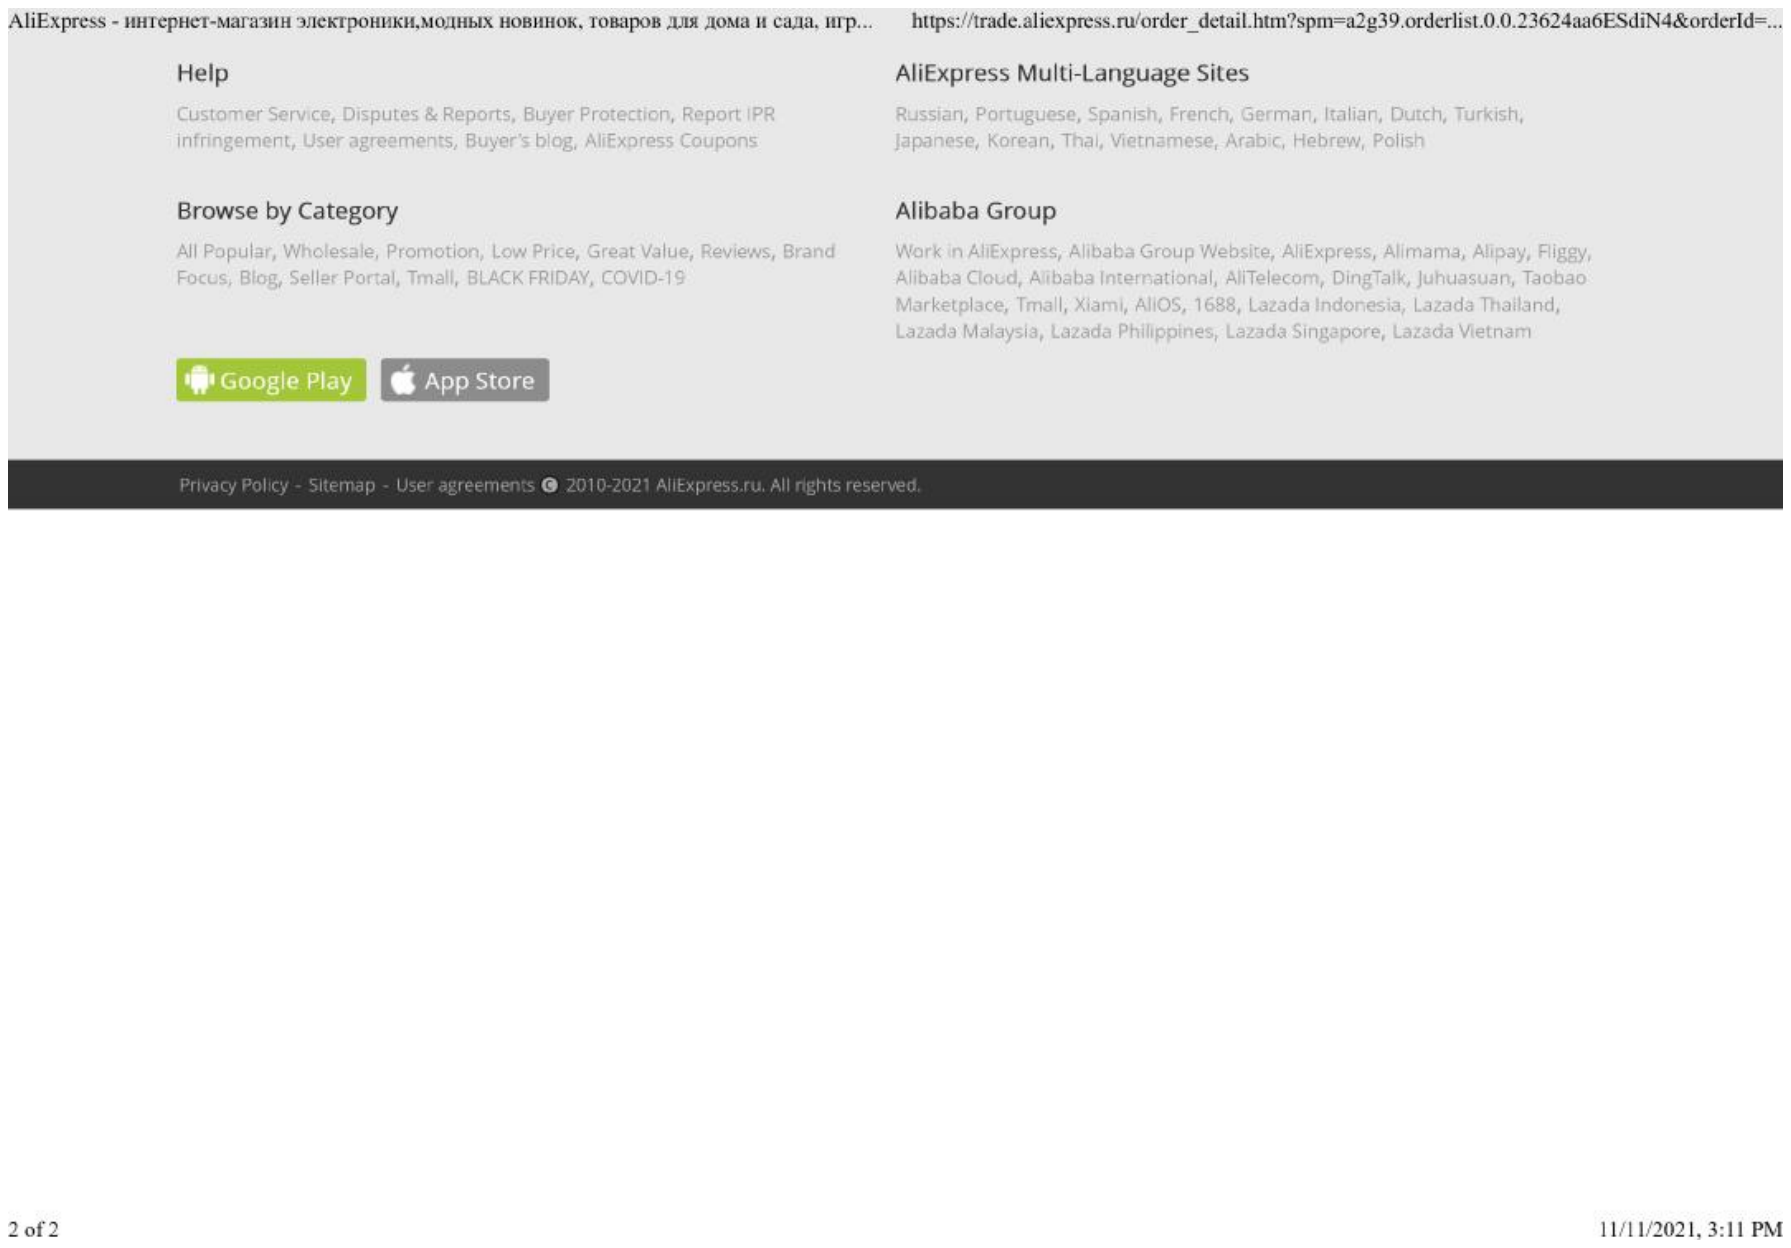
[picture p114: page 5]
