antondrroid/V_meter_013/stend_e4/pdf/stend_Schematic_v0.pdf

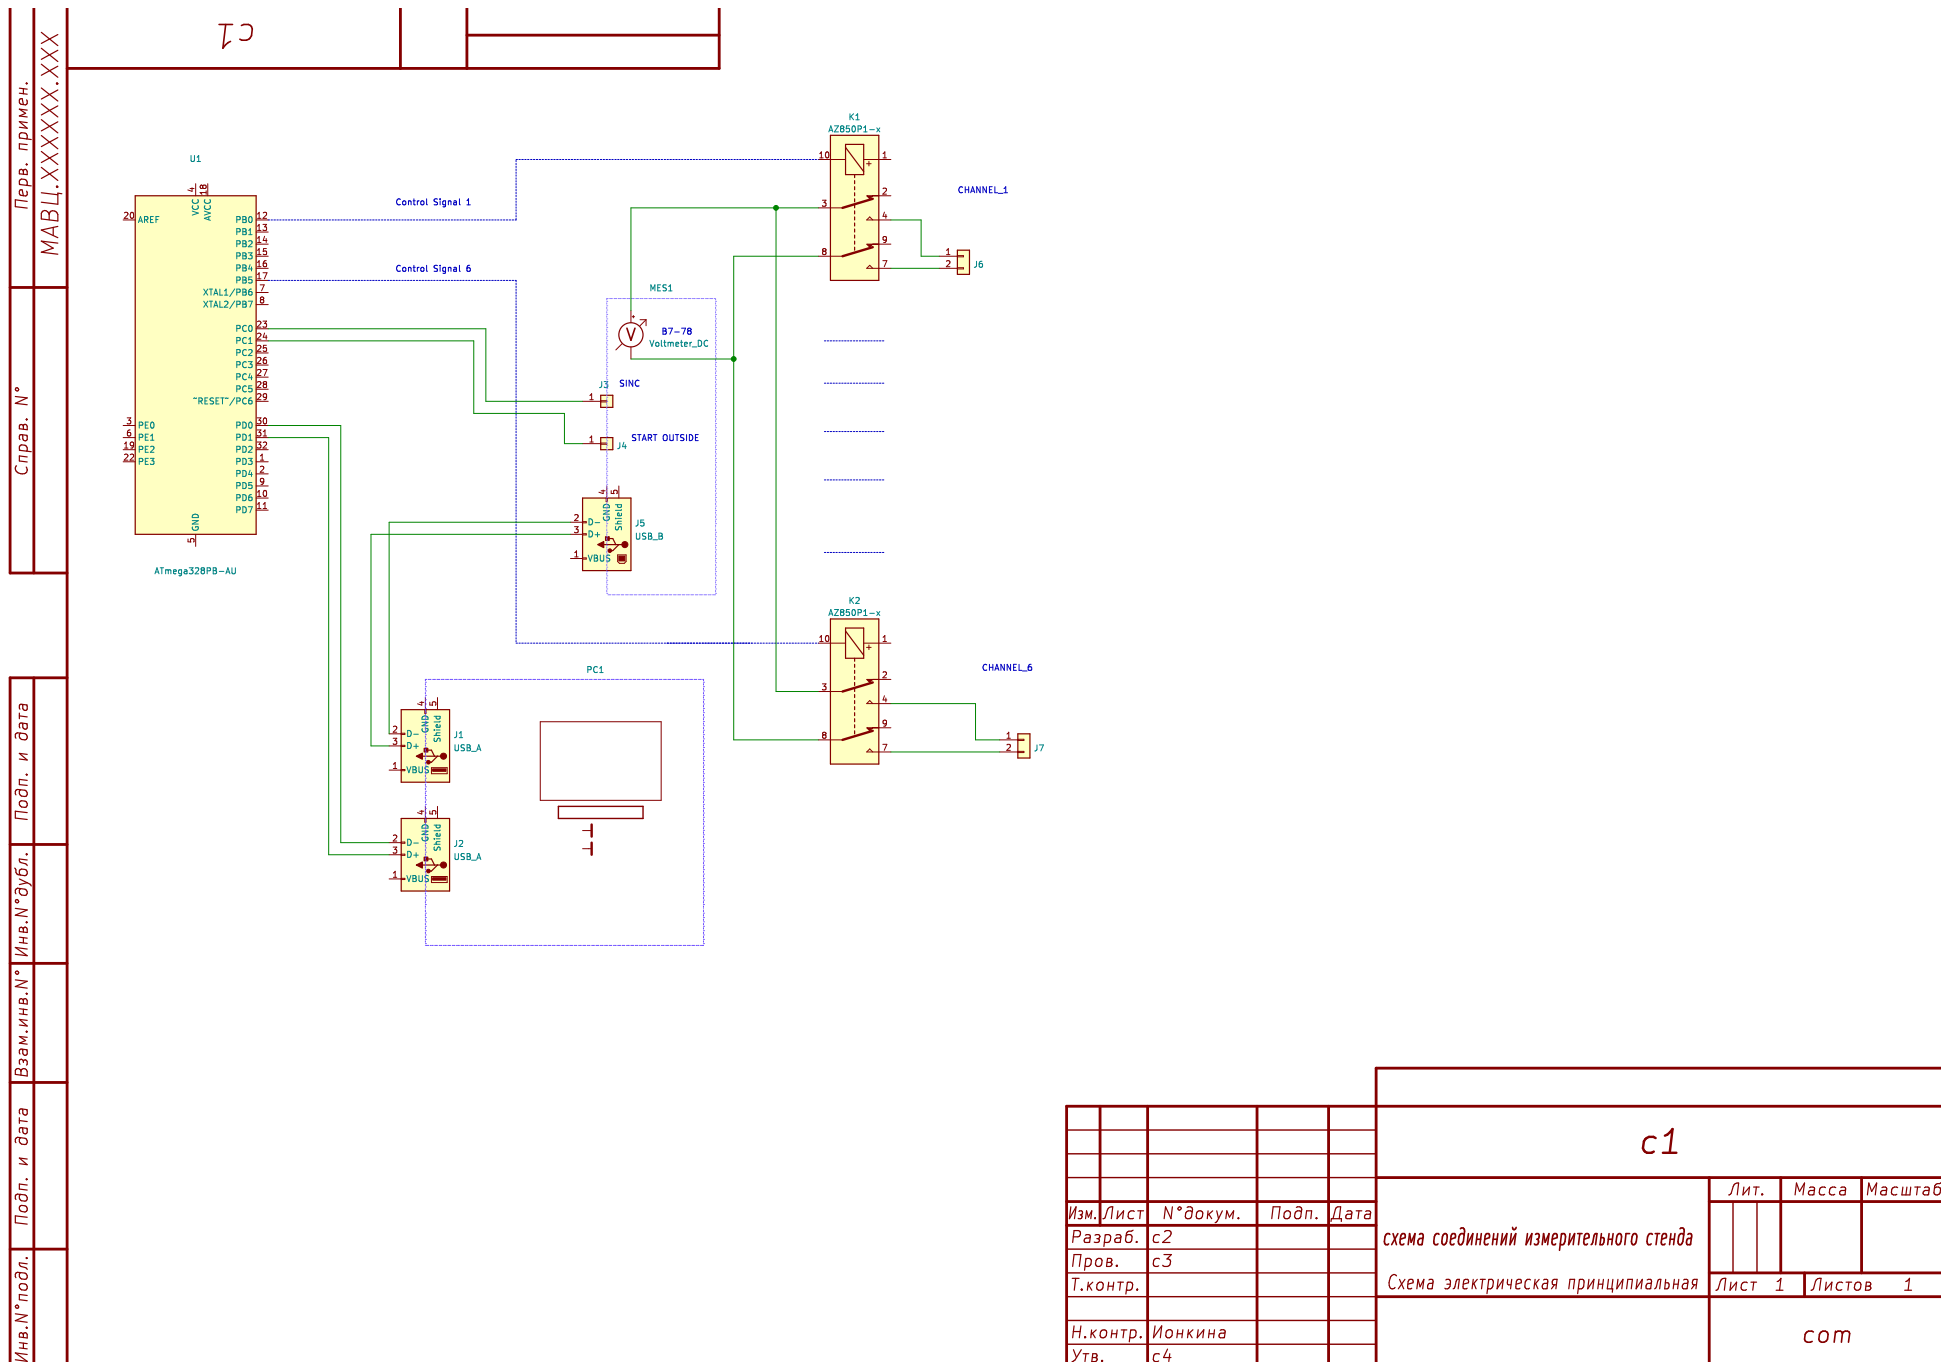
[picture p115: page 1]
