antondrroid/V_meter_013/stend_e4/pdf/stend_Schematic_wo_title_v0.pdf

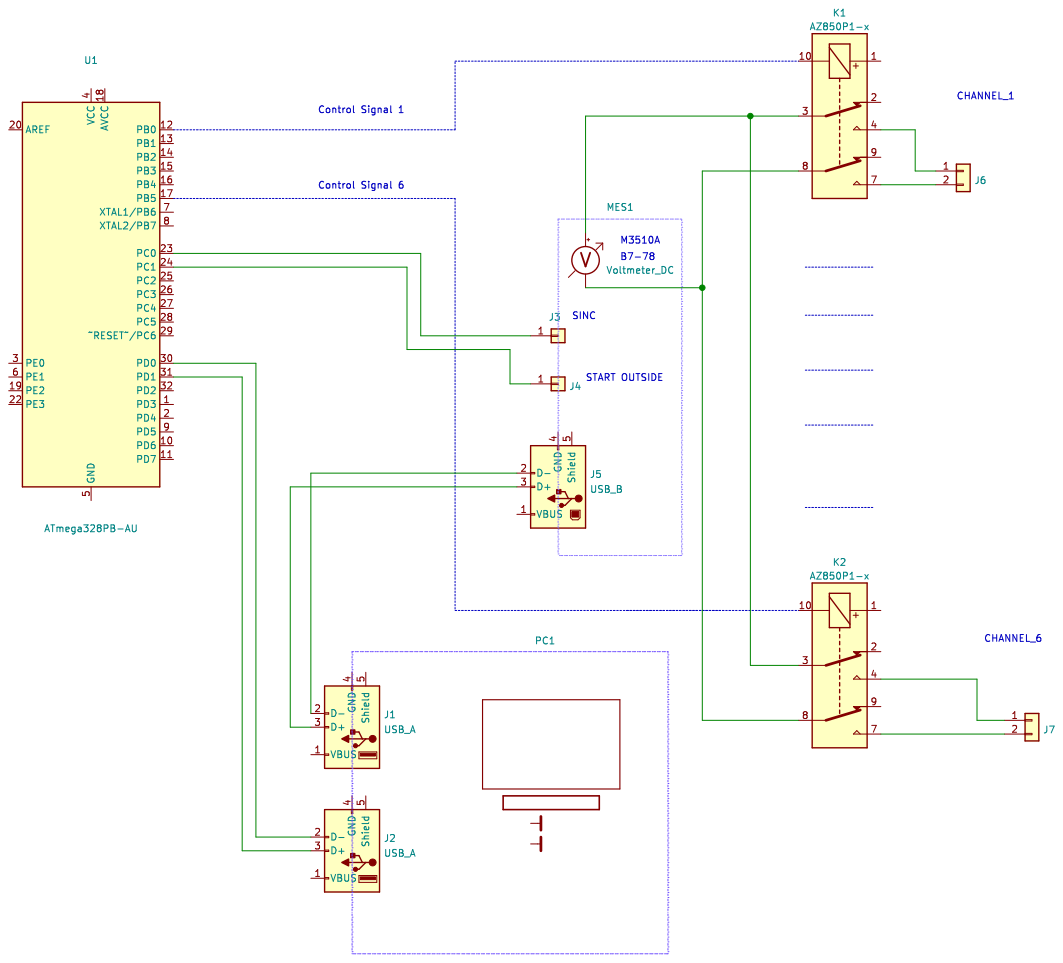
[picture p116: page 1]
