antondrroid/V_meter_013/soft_MCU/multimeter/board_project/drawings/power_8266_Schematic.pdf

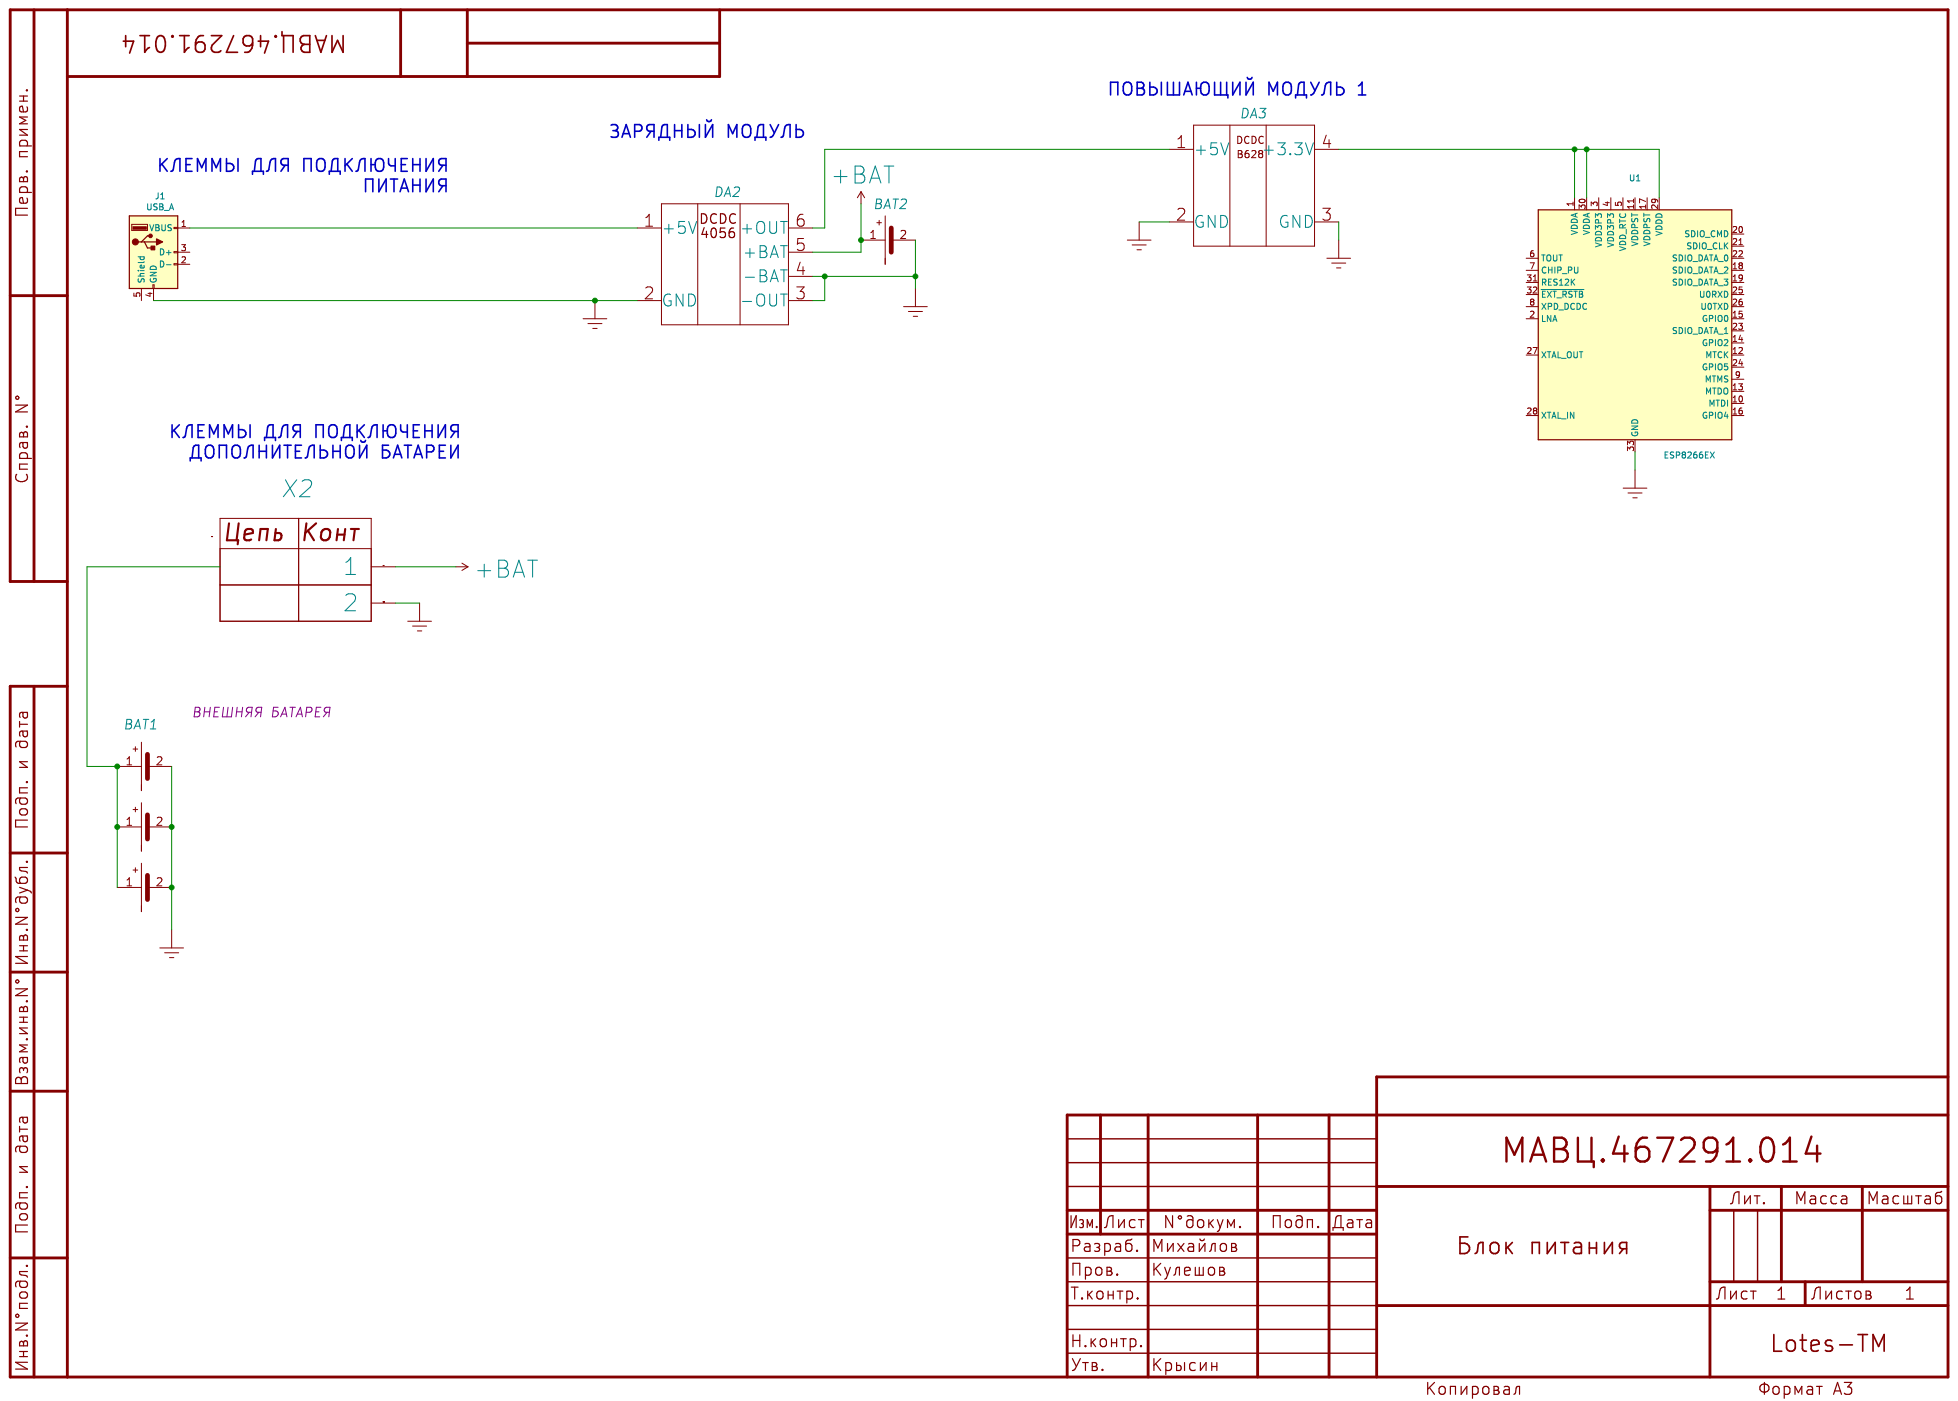
[picture p117: page 1]
