antondrroid/V_meter_013/soft_MCU/multimeter/drawings/schem/register Schematic.pdf

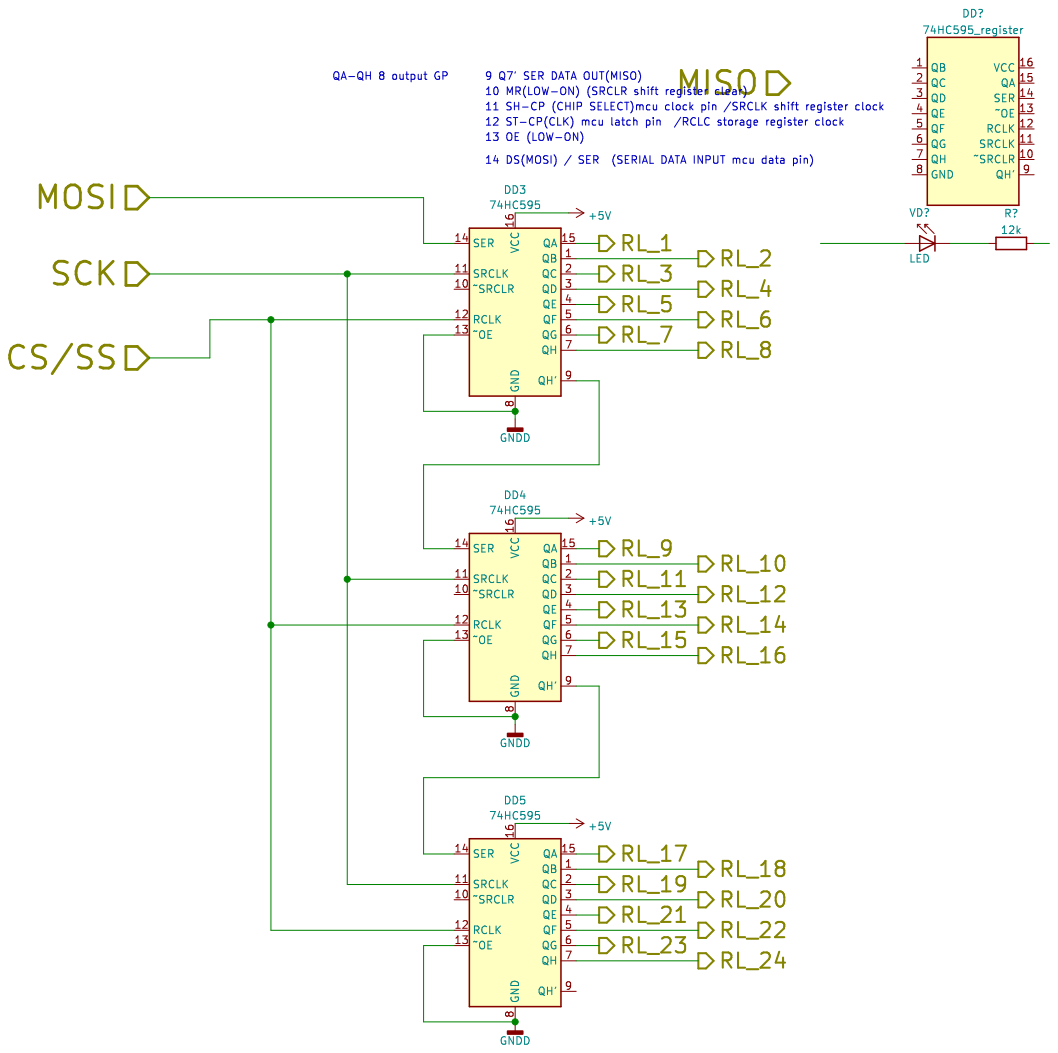
[picture p118: page 1]
