antondrroid/V_meter_013/stend_e3/stend_main4_dummy/~rawings/~3/Printing Print Schematic_v1.pdf

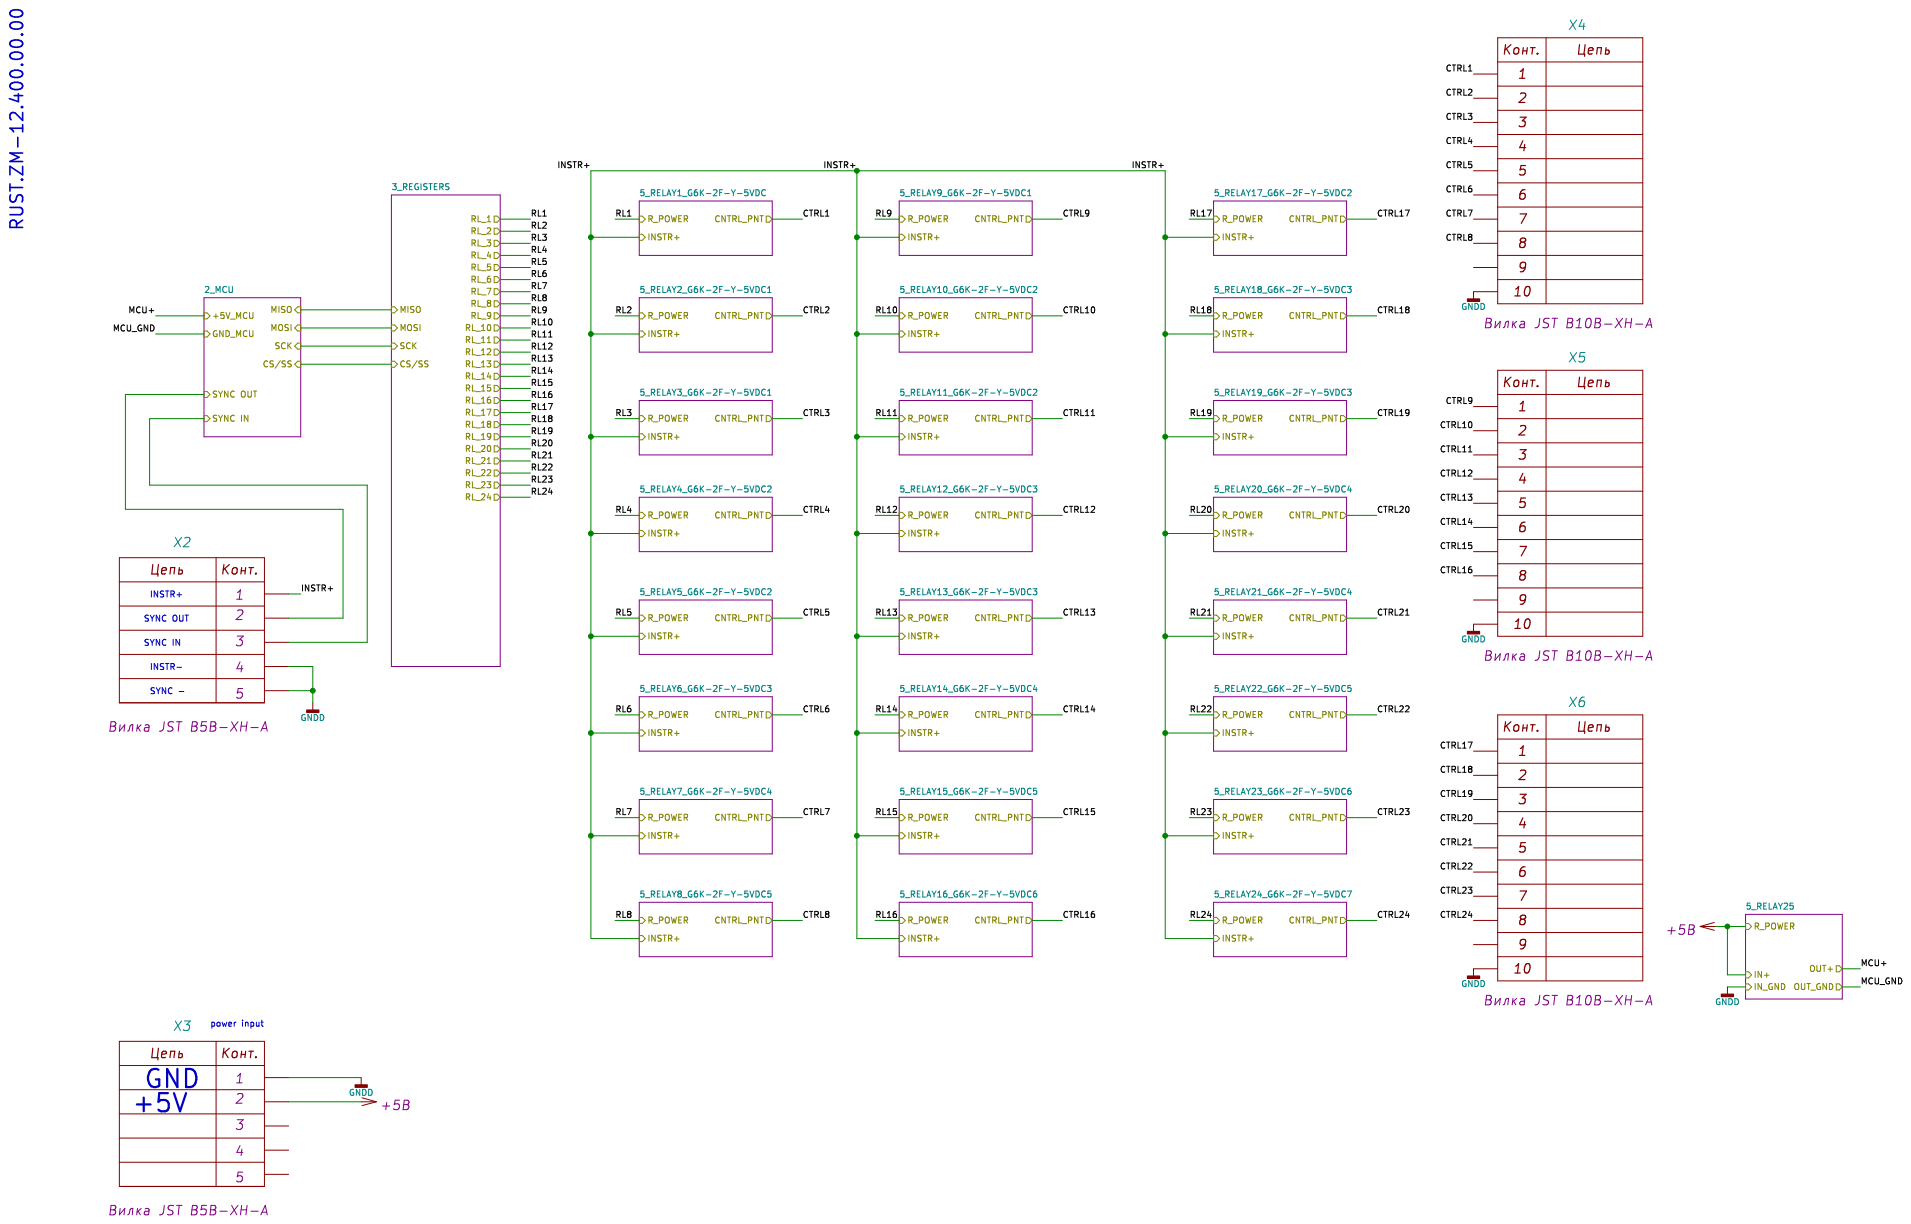
[picture p119: page 1]

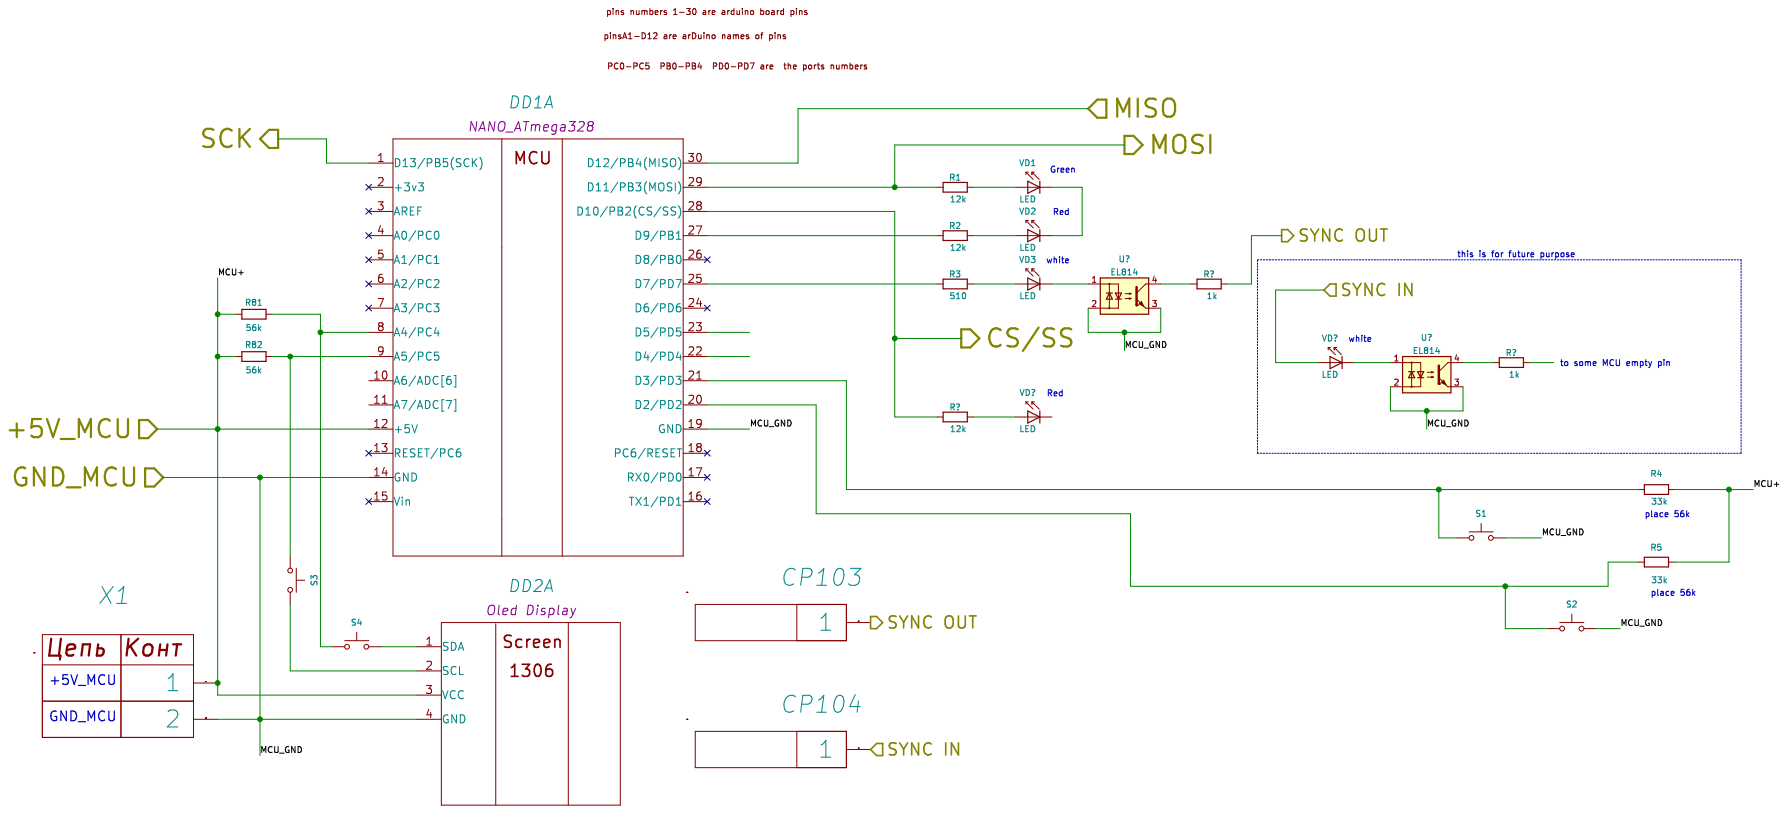
[picture p120: page 2]

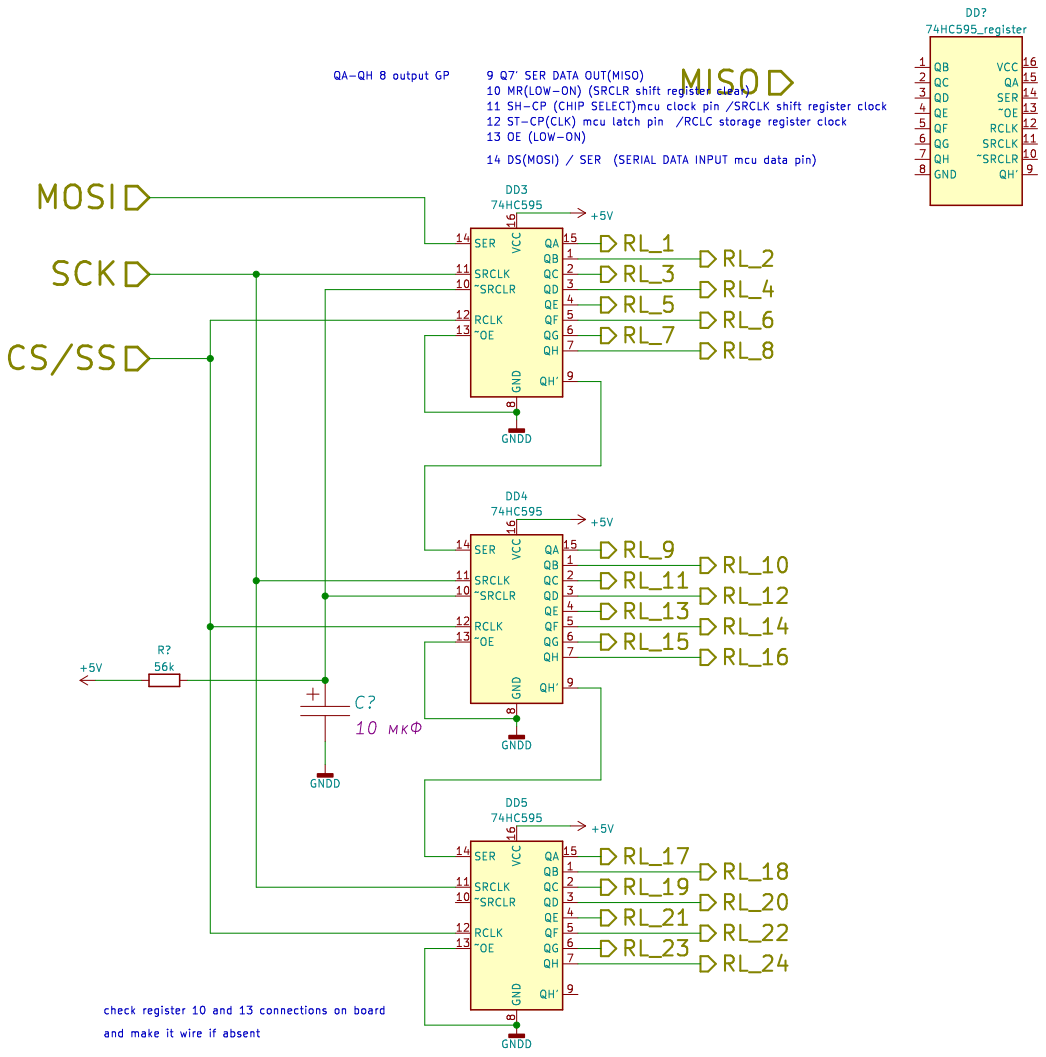
[picture p121: page 3]

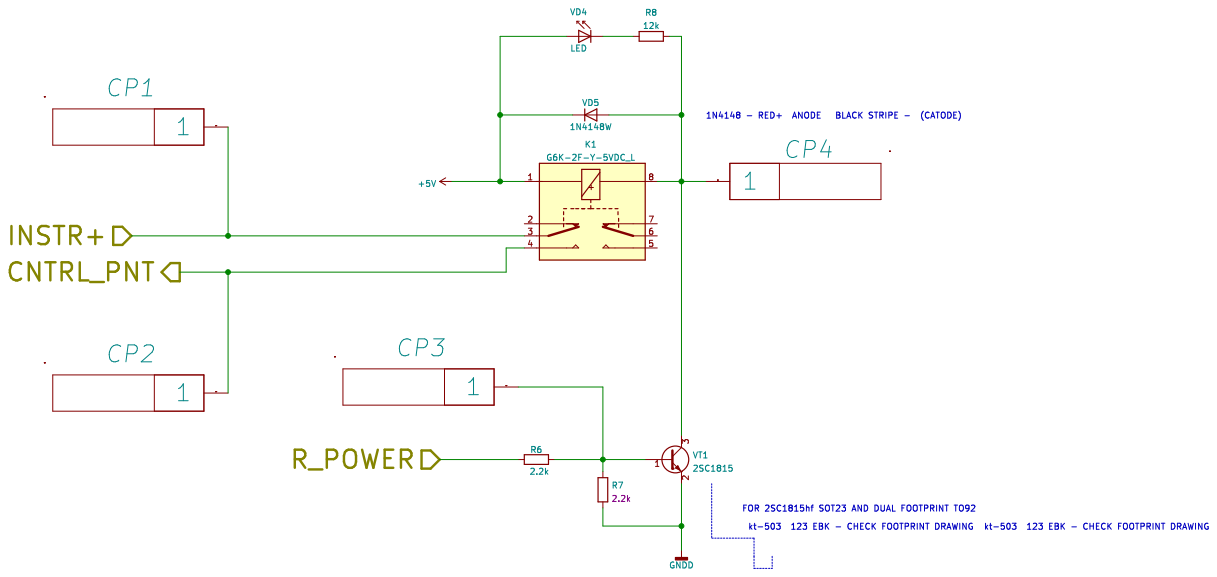
[picture p122: page 4]
