antondrroid/V_meter_013/stend_e3/stend_main4_dummy/~rawings/~3/Schematic page30 fujitsu_signal_relay.pdf

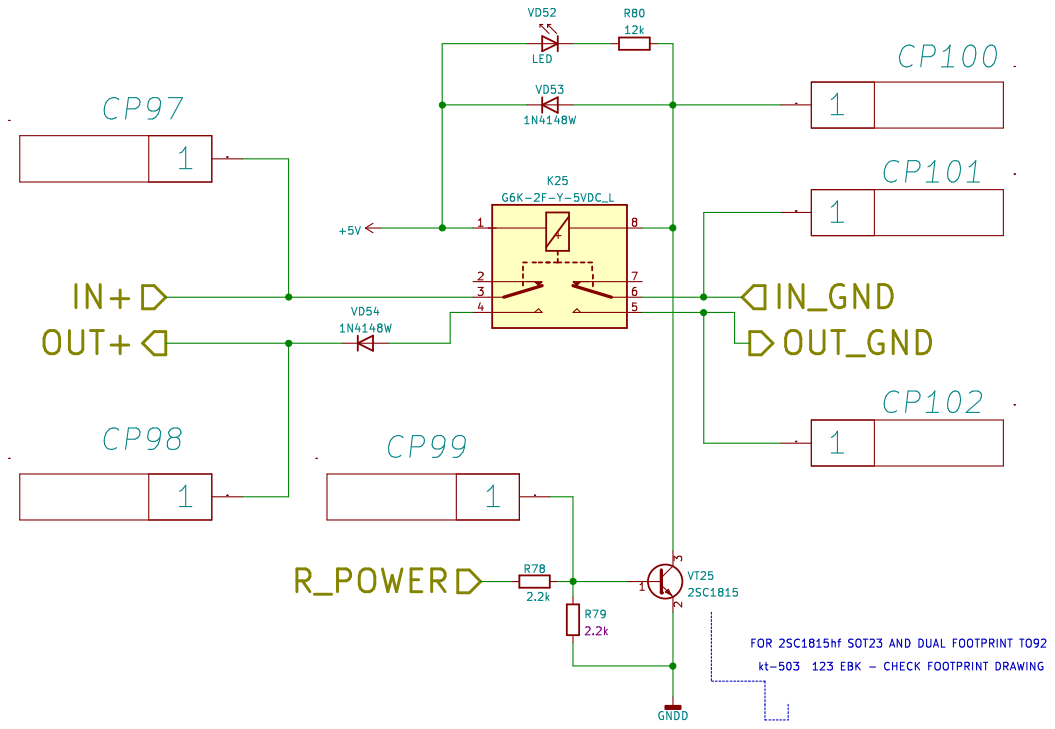
[picture p123: page 1]
