antondrroid/V_meter_013/DATA/KICAD_Template/~emplate/raspberrypi_hat/raspberrypi_hat.kicad_pcb

## KiCad design DATA/KICAD_Template/~emplate/raspberrypi_hat/raspberrypi_hat.kicad_pcb (2024-08-06)

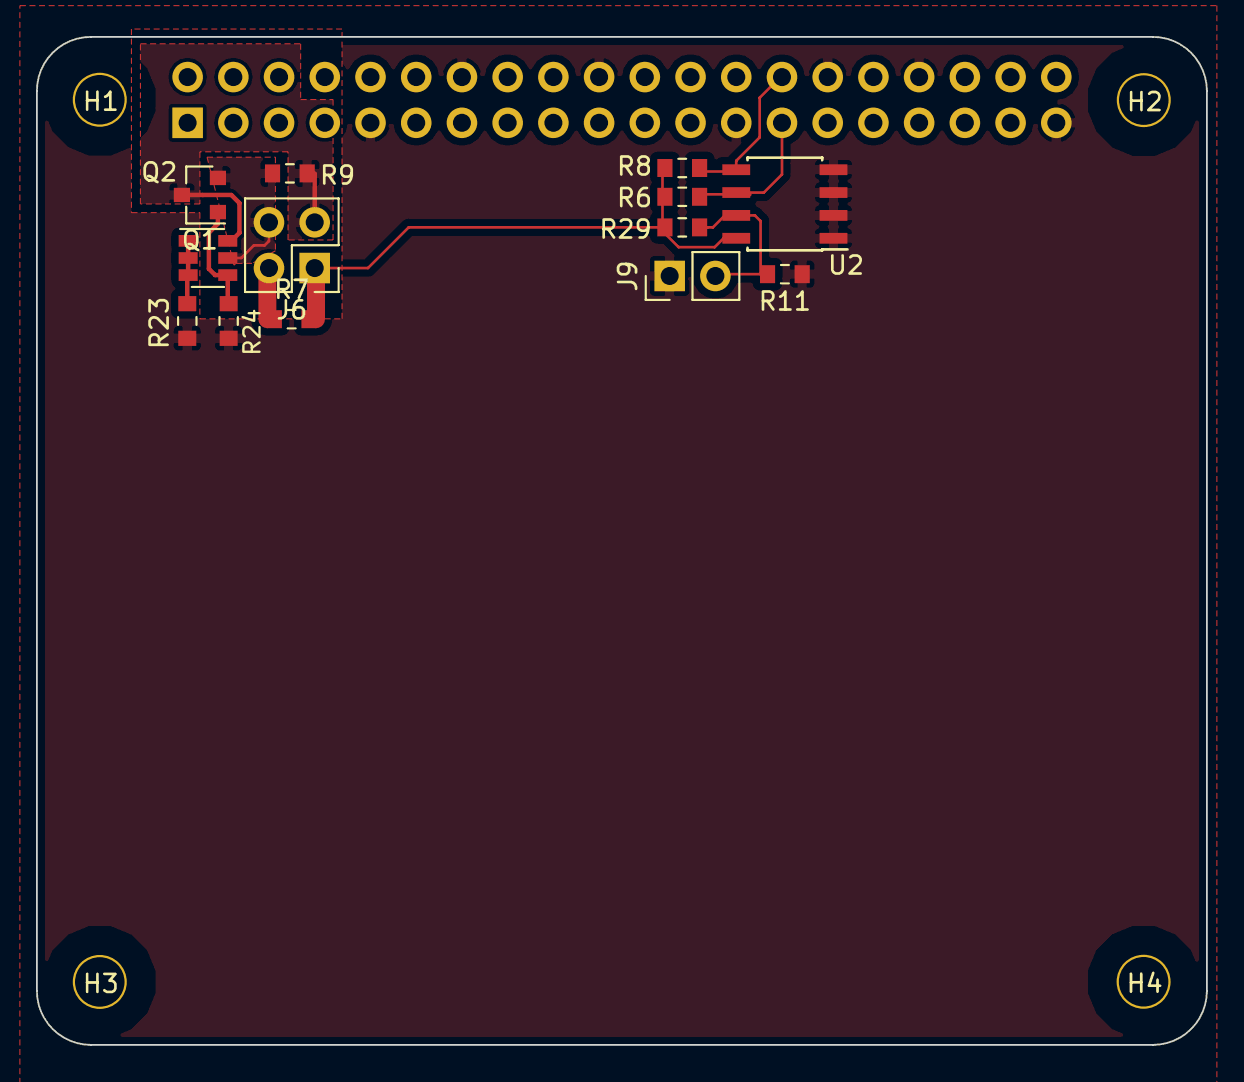
[picture p129: board raspberrypi_hat.kicad_pcb from above]

Board: 4 copper layers, 65.0 x 56.0 mm, 18 parts (1 on the bottom side), 10 nets.

Parts:
H1, H2, H3, H4: 3mm_Mounting_Hole; NPTH_3mm_ID
J3: 40HAT; PinSocket_2x20_P2.54mm_Vertical
J6: CONN_02X02; PinHeader_2x02_P2.54mm_Vertical
J9: CONN_01X02; PinHeader_1x02_P2.54mm_Vertical
Q1: DMG2305UX; SOT-23
Q2: DMMT5401; SOT-23-6
R6, R8: 3.9K; R_0603_1608Metric_Pad0.84x1.00mm_HandSolder
R7, R9, R11: DNP; R_0603_1608Metric_Pad0.84x1.00mm_HandSolder
R23, R24: 22; R_0603_1608Metric_Pad0.84x1.00mm_HandSolder
R29: 10K; R_0603_1608Metric_Pad0.84x1.00mm_HandSolder
U2: CAT24C32; SOIC-8_3.9x4.9mm_P1.27mm

Connections:
/ID_SC_EEPROM: J3.28, R8.2, U2.5
/ID_SD_EEPROM: J3.27, R6.2, U2.6
/P3V3: J6.1, R6.1, R7.2, R8.1, R29.1, U2.8
/P3V3_HAT: J3.1, J6.2, R7.1
/P5V: J6.3, Q1.3, Q2.6, R9.2
/P5V_HAT: J3.2, J3.4, J6.4, Q1.2, Q2.5, R9.1
GND: J3.6, J3.9, J3.14, J3.20, J3.25, J3.30, J3.34, J3.39, J9.1, R11.2, R23.2, R24.2, U2.1, U2.2, U2.3, U2.4
unnamed: J9.2, R11.1, R29.2, U2.7
unnamed: Q1.1, Q2.4, R24.1
unnamed: Q2.1, Q2.2, Q2.3, R23.1
