antondrroid/V_meter_013/DATA/KICAD_Template/~emplate/raspberrypi-gpio-40pin/raspberrypi-gpio-40pin.kicad_pcb

## KiCad design DATA/KICAD_Template/~emplate/raspberrypi-gpio-40pin/raspberrypi-gpio-40pin.kicad_pcb (2024-08-06)

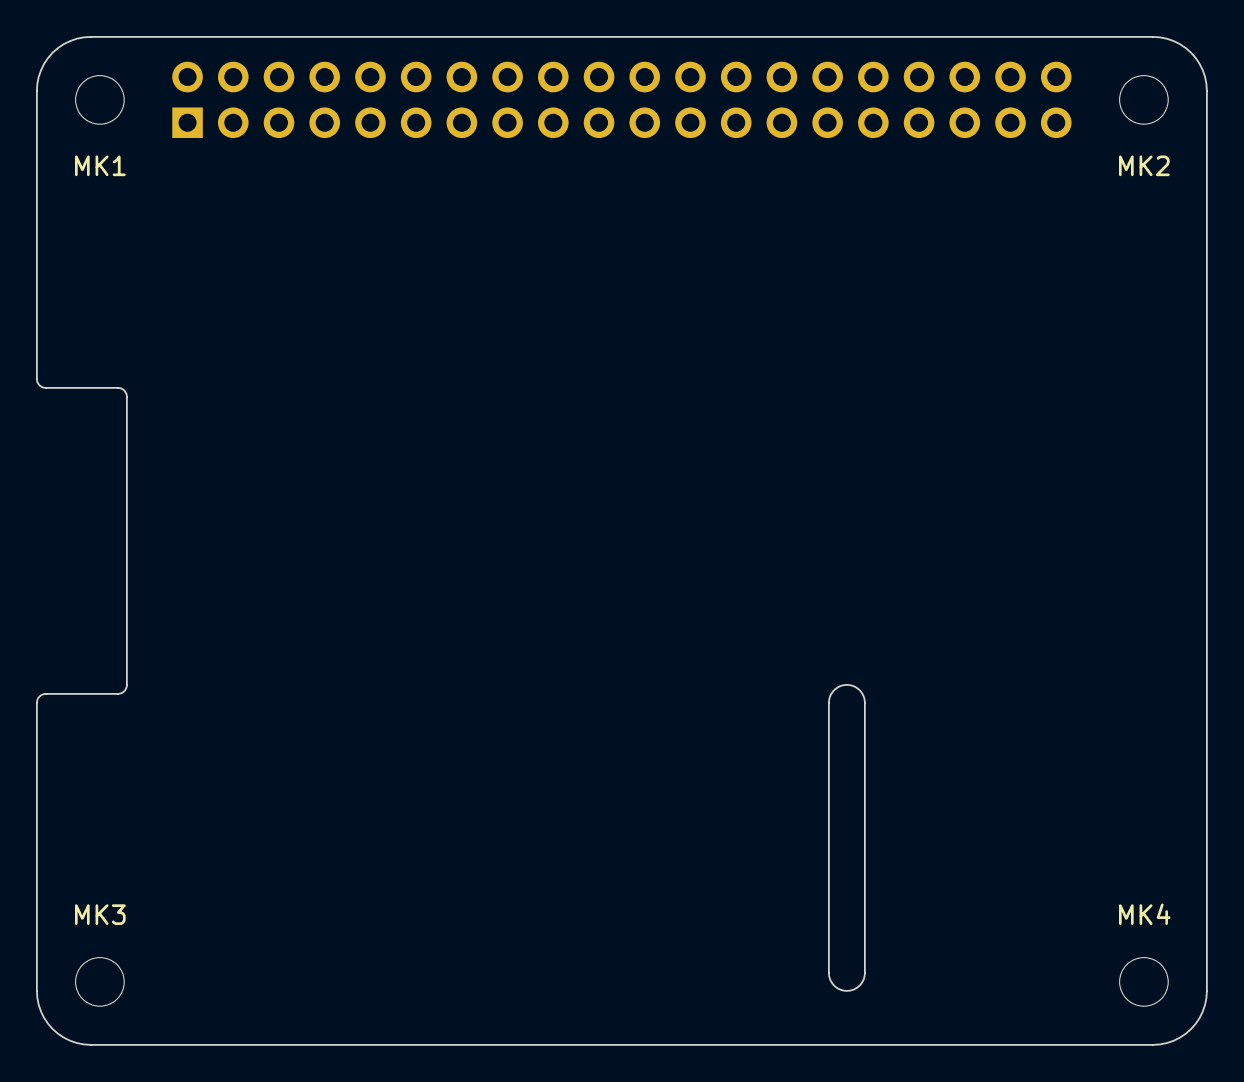
[picture p130: board raspberrypi-gpio-40pin.kicad_pcb from above]

Board: 2 copper layers, 65.0 x 56.0 mm, 5 parts (1 on the bottom side), 3 nets, no tracks yet.

Parts:
MK1, MK2, MK3, MK4: M2.5; MountingHole_2.7mm_M2.5
P1: Conn_02x20_Odd_Even; PinSocket_2x20_P2.54mm_Vertical

Connections:
+3V3: P1.1, P1.17
+5V: P1.2, P1.4
GND: P1.6, P1.9, P1.14, P1.20, P1.25, P1.30, P1.34, P1.39
