antondrroid/V_meter_013/DATA/KICAD_Template/~emplate/Arduino_Mega_R3/Arduino_Mega.kicad_pcb

## KiCad design DATA/KICAD_Template/~emplate/Arduino_Mega_R3/Arduino_Mega.kicad_pcb (2024-08-06)

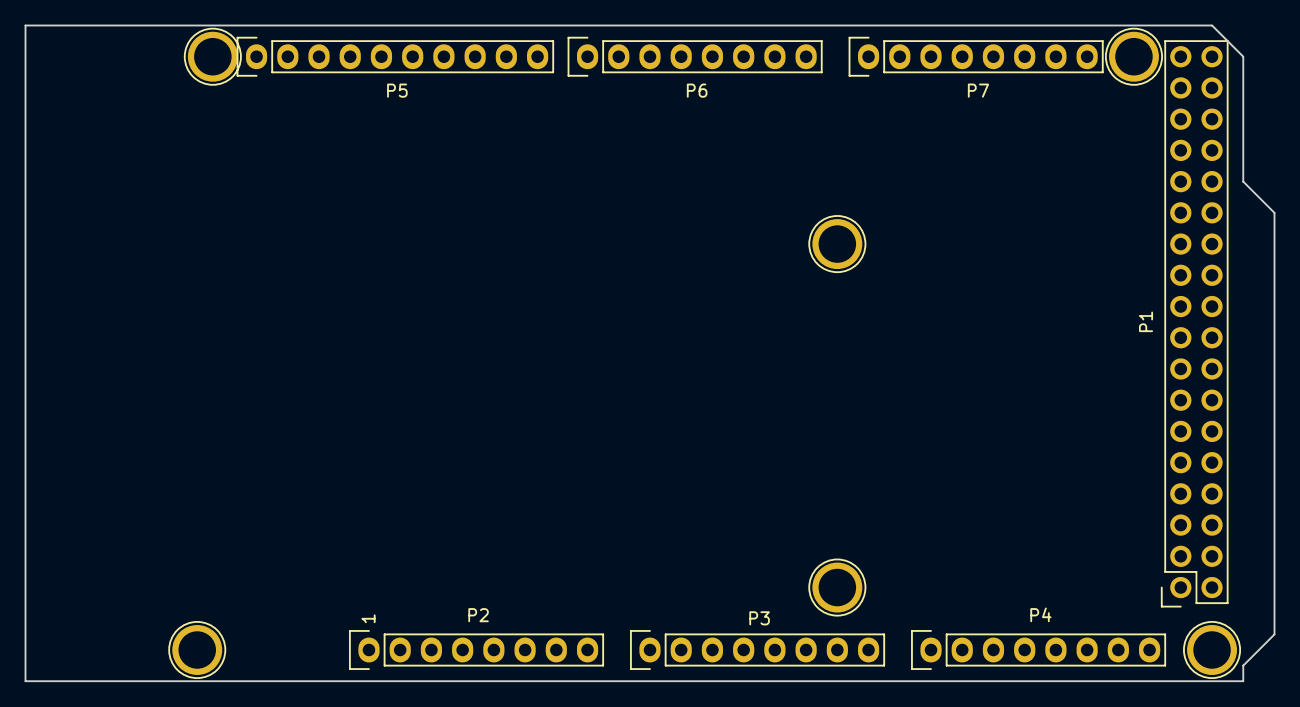
[picture p131: board Arduino_Mega.kicad_pcb from above]

Board: 2 copper layers, 101.6 x 53.3 mm, 13 parts (0 on the bottom side), 2 nets, no tracks yet.

Parts:
P1: Digital; Socket_Strip_Arduino_2x18
P2: Power; Socket_Strip_Arduino_1x08
P3, P4: Analog; Socket_Strip_Arduino_1x08
P5: PWM; Socket_Strip_Arduino_1x10
P6: PWM; Socket_Strip_Arduino_1x08
P7: Communication; Socket_Strip_Arduino_1x08
P8, P9, P10, P11, P12, P13: CONN_01X01; Arduino_1pin

Connections:
+5V: P1.35, P1.36, P2.5
GND: P1.1, P1.2, P2.6, P2.7, P5.4
