antondrroid/V_meter_013/DATA/KICAD_Template/~emplate/Arduino_Mini/Arduino_Mini.kicad_pcb

## KiCad design DATA/KICAD_Template/~emplate/Arduino_Mini/Arduino_Mini.kicad_pcb (2024-08-06)

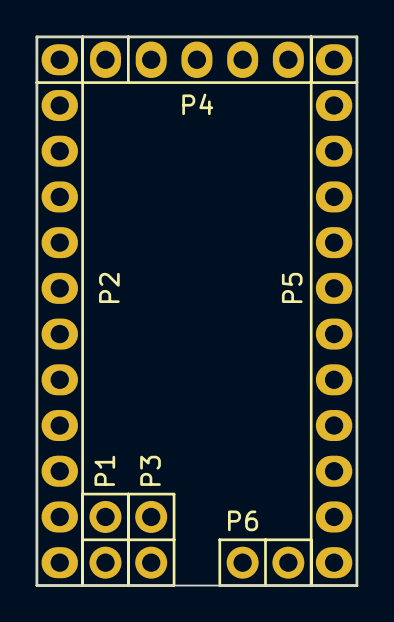
[picture p132: board Arduino_Mini.kicad_pcb from above]

Board: 2 copper layers, 17.8 x 30.5 mm, 6 parts (0 on the bottom side), 5 nets, no tracks yet.

Parts:
P1, P3: ADC; Socket_Strip_Arduino_1x02
P2: Digital; Socket_Strip_Arduino_1x12
P4: COM; Socket_Strip_Arduino_1x05
P5: Analog; Socket_Strip_Arduino_1x12
P6: PWR; Socket_Strip_Arduino_1x02

Connections:
+5V: P4.4, P5.4, P6.1
/0(Rx): P2.2, P4.3
/1(Tx): P2.1, P4.2
/Reset: P2.3, P4.1, P5.3
GND: P2.4, P4.5, P5.2, P6.2
