antondrroid/V_meter_013/DATA/KICAD_Template/~emplate/Arduino_Nano/Arduino_Nano.kicad_pcb

## KiCad design DATA/KICAD_Template/~emplate/Arduino_Nano/Arduino_Nano.kicad_pcb (2024-08-06)

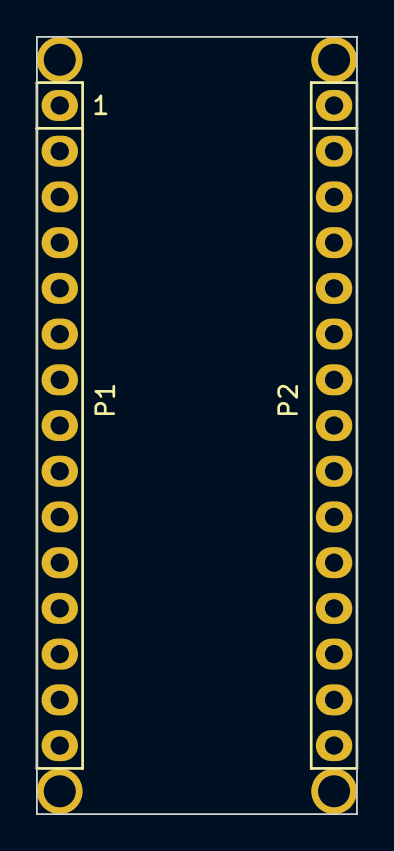
[picture p133: board Arduino_Nano.kicad_pcb from above]

Board: 2 copper layers, 17.8 x 43.2 mm, 6 parts (0 on the bottom side), 2 nets, no tracks yet.

Parts:
P1: Digital; Socket_Strip_Arduino_1x15
P2: Analog; Socket_Strip_Arduino_1x15
P3, P4, P5, P6: CONN_01X01; 1pin_Nano

Connections:
/Reset: P1.3, P2.3
GND: P1.4, P2.2
