antondrroid/V_meter_013/DATA/KICAD_Template/~emplate/Arduino_Micro/Arduino_Micro.kicad_pcb

## KiCad design DATA/KICAD_Template/~emplate/Arduino_Micro/Arduino_Micro.kicad_pcb (2024-08-06)

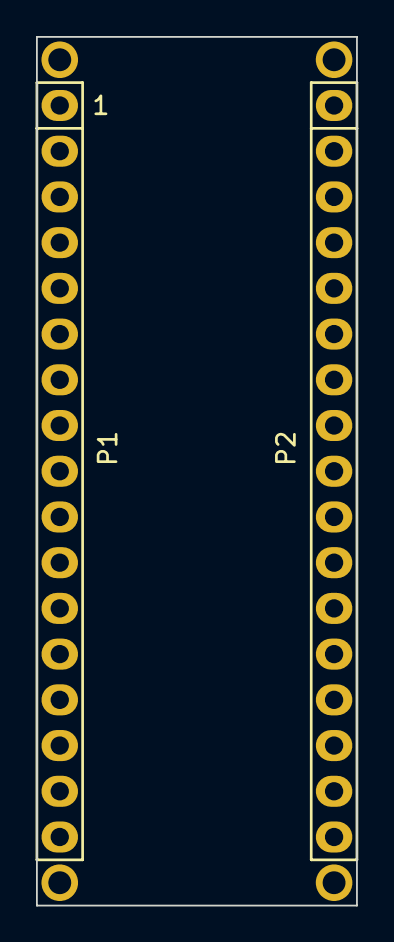
[picture p134: board Arduino_Micro.kicad_pcb from above]

Board: 2 copper layers, 17.8 x 48.3 mm, 6 parts (0 on the bottom side), 2 nets, no tracks yet.

Parts:
P1: Digital; Socket_Strip_Arduino_1x17
P2: Analog; Socket_Strip_Arduino_1x17
P3, P4, P5, P6: CONN_01X01; 1pin_Micro

Connections:
/Reset: P1.5, P2.5
GND: P1.6, P2.4
