antondrroid/V_meter_013/DATA/KICAD_Template/~emplate/Arduino_Pro_Mini/Arduino_Pro_Mini.kicad_pcb

## KiCad design DATA/KICAD_Template/~emplate/Arduino_Pro_Mini/Arduino_Pro_Mini.kicad_pcb (2024-08-06)

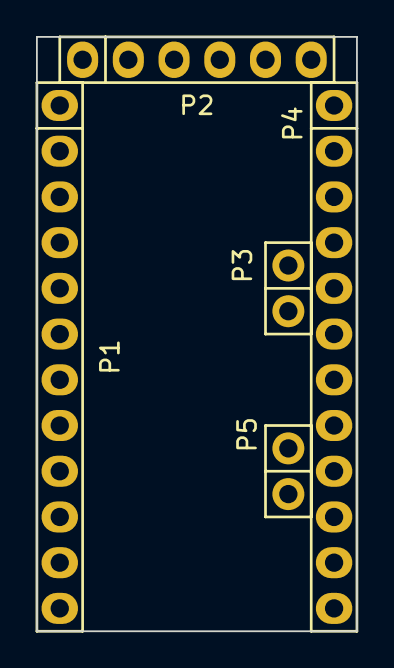
[picture p135: board Arduino_Pro_Mini.kicad_pcb from above]

Board: 2 copper layers, 17.8 x 33.0 mm, 5 parts (0 on the bottom side), 5 nets, no tracks yet.

Parts:
P1: Digital; Socket_Strip_Arduino_1x12
P2: COM; Socket_Strip_Arduino_1x06
P3, P5: ADC; Socket_Strip_Arduino_1x02
P4: Analog; Socket_Strip_Arduino_1x12

Connections:
/0(Rx): P1.2, P2.3
/1(Tx): P1.1, P2.2
/Reset: P1.3, P4.3
GND: P1.4, P2.5, P2.6, P4.2
VCC: P2.4, P4.4
