antondrroid/V_meter_013/DATA/KICAD_Template/~emplate/Arduino_Uno_R3/Arduino_Uno.kicad_pcb

## KiCad design DATA/KICAD_Template/~emplate/Arduino_Uno_R3/Arduino_Uno.kicad_pcb (2024-08-06)


Board: 2 copper layers, 68.6 x 53.3 mm, 8 parts (0 on the bottom side), 3 nets, no tracks yet.

Parts:
P1: Power; Socket_Strip_Arduino_1x08
P2: Analog; Socket_Strip_Arduino_1x06
P3: Digital; Socket_Strip_Arduino_1x10
P4: Digital; Socket_Strip_Arduino_1x08
P5, P6, P7, P8: CONN_01X01; Arduino_1pin

Connections:
/A4(SDA): P2.5, P3.2
/A5(SCL): P2.6, P3.1
GND: P1.6, P1.7, P3.4
