antondrroid/V_meter_013/stend_e3/stend_main3_stencil/stend_main_stencil.kicad_pcb

## KiCad design stend_e3/stend_main3_stencil/stend_main_stencil.kicad_pcb (2024-08-06)

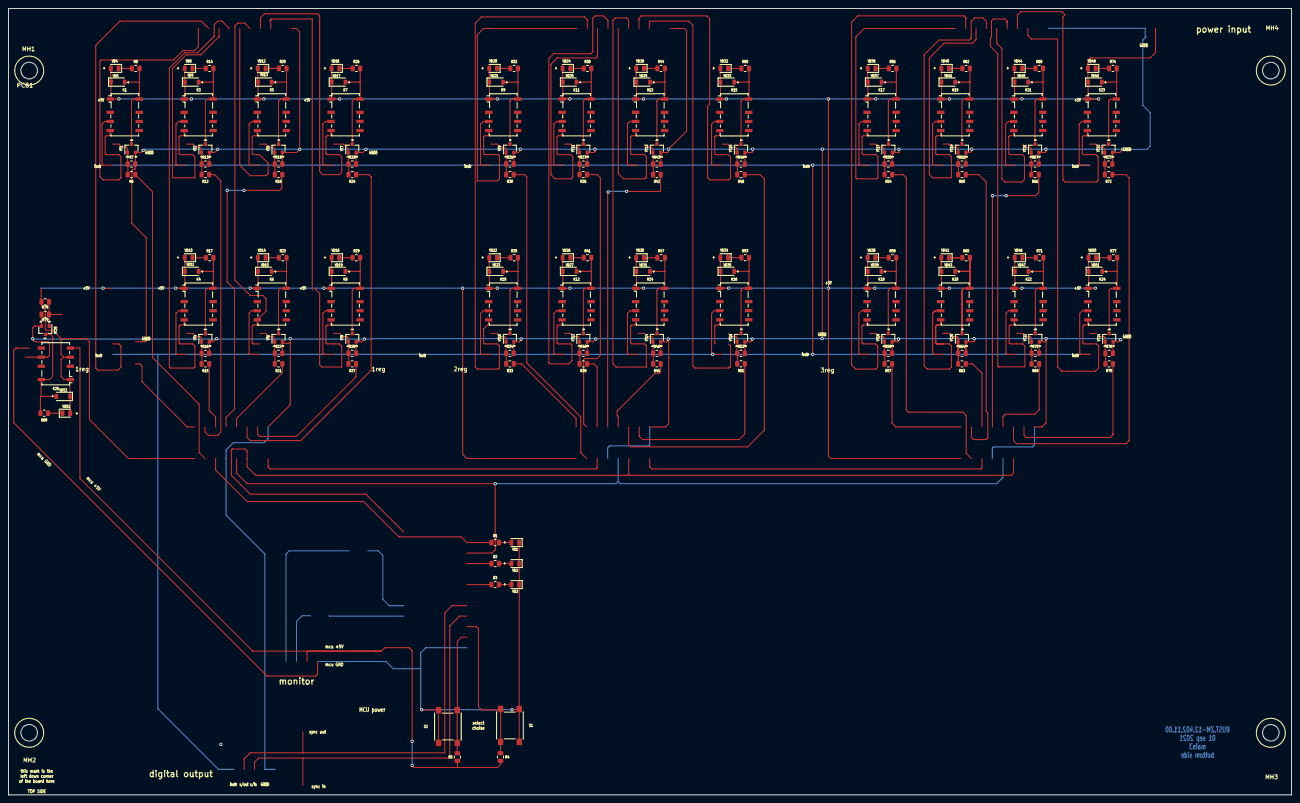
[picture p137: board stend_main_stencil.kicad_pcb from above]

Board: 2 copper layers, 310.0 x 190.0 mm, 179 parts (0 on the bottom side), 82 nets.

Parts:
K1, K3, K4, K5, K6, K7, K8, K9, K10, K11, K12, K13, K14, K15, K16, K17, K18, K19, K20, K21, K22, K23, K24, K25: G6K-2F-Y-5VDC_L; Relay_DPDT_Omron_G6K-2F-Y
PCB1: board_symbol_190x310; board_fp_190x310
R1, R2, R3, R4, R5: 33k; R_0805_2012Metric
R6, R12, R15, R18, R21, R24, R27, R30, R33, R36, R39, R42, R45, R48, R51, R54, R57, R60, R63, R66, R69, R72, R75, R78: 2.2k; R_0805_2012Metric
R7, R13, R16, R19, R22, R25, R28, R31, R34, R37, R40, R43, R46, R49, R52, R55, R58, R61, R64, R67, R70, R73, R76, R79: 2.2kvert; R_0805_2012Metric
R8, R14, R17, R20, R23, R26, R29, R32, R35, R38, R41, R44, R47, R50, R53, R56, R59, R62, R65, R68, R71, R74, R77, R80: 12k; R_0805_2012Metric
S1, S2: taktile button KLS7; SW_Push_2P1T_6x6mm
VD1, VD2, VD3, VD4, VD8, VD10, VD12, VD14, VD16, VD18, VD20, VD22, VD24, VD26, VD28, VD30, VD32, VD34, VD36, VD38, VD40, VD42, VD44, VD46, VD48, VD50, VD52: LED; LED_0805_2012Metric
VD5, VD9, VD11, VD13, VD15, VD17, VD19, VD21, VD23, VD25, VD27, VD29, VD31, VD33, VD35, VD37, VD39, VD41, VD43, VD45, VD47, VD49, VD51, VD53: 1N4148W; D_SOD-123
VT1, VT3, VT4, VT5, VT6, VT7, VT8, VT9, VT10, VT11, VT12, VT13, VT14, VT15, VT16, VT17, VT18, VT19, VT20, VT21, VT22, VT23, VT24, VT25: 2SC1815; SOT-23_MY_C_E_Silk

Connections:
+5V: K1.1, K3.1, K4.1, K5.1, K6.1, K7.1, K8.1, K9.1, K10.1, K11.1, K12.1, K13.1, K14.1, K15.1, K16.1, K17.1, K18.1, K19.1, K20.1, K21.1, K22.1, K23.1, K24.1, K25.1, K25.3, R78.1, VD4.2 (A), VD5.1 (K), VD8.2 (A), VD9.1 (K), VD10.2 (A), VD11.1 (K), VD12.2 (A), VD13.1 (K), VD14.2 (A), VD15.1 (K), VD16.2 (A), VD17.1 (K), VD18.2 (A), VD19.1 (K), VD20.2 (A), VD21.1 (K), VD22.2 (A), VD23.1 (K), VD24.2 (A), VD25.1 (K), VD26.2 (A), VD27.1 (K), VD28.2 (A), VD29.1 (K), VD30.2 (A), VD31.1 (K), VD32.2 (A), VD33.1 (K), VD34.2 (A), VD35.1 (K), VD36.2 (A), VD37.1 (K), VD38.2 (A), VD39.1 (K), VD40.2 (A), VD41.1 (K), VD42.2 (A), VD43.1 (K), VD44.2 (A), VD45.1 (K), VD46.2 (A), VD47.1 (K), VD48.2 (A), VD49.1 (K), VD50.2 (A), VD51.1 (K), VD52.2 (A), VD53.1 (K)
/INSTR+: K1.3, K3.3, K4.3, K5.3, K6.3, K7.3, K8.3, K9.3, K10.3, K11.3, K12.3, K13.3, K14.3, K15.3, K16.3, K17.3, K18.3, K19.3, K20.3, K21.3, K22.3, K23.3, K24.3
/MCU+: K25.4, R4.2, R5.1
/MCU_GND: K25.5, S1.2, S2.2, VD1.1 (K), VD2.1 (K), VD3.1 (K)
GNDD: K25.6, R7.2, R13.2, R16.2, R19.2, R22.2, R25.2, R28.2, R31.2, R34.2, R37.2, R40.2, R43.2, R46.2, R49.2, R52.2, R55.2, R58.2, R61.2, R64.2, R67.2, R70.2, R73.2, R76.2, R79.2, VT1.2 (E), VT3.2 (E), VT4.2 (E), VT5.2 (E), VT6.2 (E), VT7.2 (E), VT8.2 (E), VT9.2 (E), VT10.2 (E), VT11.2 (E), VT12.2 (E), VT13.2 (E), VT14.2 (E), VT15.2 (E), VT16.2 (E), VT17.2 (E), VT18.2 (E), VT19.2 (E), VT20.2 (E), VT21.2 (E), VT22.2 (E), VT23.2 (E), VT24.2 (E), VT25.2 (E)
unnamed: R6.2, R7.1, VT1.1 (B)
unnamed: K1.8, R8.2, VD5.2 (A), VT1.3 (C)
unnamed: R12.2, R13.1, VT3.1 (B)
unnamed: K3.8, R14.2, VD9.2 (A), VT3.3 (C)
unnamed: R15.2, R16.1, VT4.1 (B)
unnamed: K4.8, R17.2, VD11.2 (A), VT4.3 (C)
unnamed: R18.2, R19.1, VT5.1 (B)
unnamed: K5.8, R20.2, VD13.2 (A), VT5.3 (C)
unnamed: R21.2, R22.1, VT6.1 (B)
unnamed: K6.8, R23.2, VD15.2 (A), VT6.3 (C)
unnamed: R24.2, R25.1, VT7.1 (B)
unnamed: K7.8, R26.2, VD17.2 (A), VT7.3 (C)
unnamed: R27.2, R28.1, VT8.1 (B)
unnamed: K8.8, R29.2, VD19.2 (A), VT8.3 (C)
unnamed: R30.2, R31.1, VT9.1 (B)
unnamed: K9.8, R32.2, VD21.2 (A), VT9.3 (C)
unnamed: R33.2, R34.1, VT10.1 (B)
unnamed: K10.8, R35.2, VD23.2 (A), VT10.3 (C)
unnamed: R36.2, R37.1, VT11.1 (B)
unnamed: K11.8, R38.2, VD25.2 (A), VT11.3 (C)
unnamed: R39.2, R40.1, VT12.1 (B)
unnamed: K12.8, R41.2, VD27.2 (A), VT12.3 (C)
unnamed: R42.2, R43.1, VT13.1 (B)
unnamed: K13.8, R44.2, VD29.2 (A), VT13.3 (C)
unnamed: R45.2, R46.1, VT14.1 (B)
unnamed: K14.8, R47.2, VD31.2 (A), VT14.3 (C)
unnamed: R48.2, R49.1, VT15.1 (B)
unnamed: K15.8, R50.2, VD33.2 (A), VT15.3 (C)
unnamed: R51.2, R52.1, VT16.1 (B)
unnamed: K16.8, R53.2, VD35.2 (A), VT16.3 (C)
unnamed: R54.2, R55.1, VT17.1 (B)
unnamed: K17.8, R56.2, VD37.2 (A), VT17.3 (C)
unnamed: R57.2, R58.1, VT18.1 (B)
unnamed: K18.8, R59.2, VD39.2 (A), VT18.3 (C)
unnamed: R60.2, R61.1, VT19.1 (B)
unnamed: K19.8, R62.2, VD41.2 (A), VT19.3 (C)
unnamed: R63.2, R64.1, VT20.1 (B)
unnamed: K20.8, R65.2, VD43.2 (A), VT20.3 (C)
unnamed: R66.2, R67.1, VT21.1 (B)
unnamed: K21.8, R68.2, VD45.2 (A), VT21.3 (C)
unnamed: R69.2, R70.1, VT22.1 (B)
unnamed: K22.8, R71.2, VD47.2 (A), VT22.3 (C)
unnamed: R72.2, R73.1, VT23.1 (B)
unnamed: K23.8, R74.2, VD49.2 (A), VT23.3 (C)
unnamed: R75.2, R76.1, VT24.1 (B)
unnamed: K24.8, R77.2, VD51.2 (A), VT24.3 (C)
unnamed: R78.2, R79.1, VT25.1 (B)
unnamed: K25.8, R80.2, VD53.2 (A), VT25.3 (C)
unnamed: R5.2, S2.1
unnamed: R4.1, S1.1
unnamed: R1.2, VD1.2 (A)
unnamed: R2.2, VD2.2 (A)
unnamed: R3.2, VD3.2 (A)
unnamed: R8.1, VD4.1 (K)
unnamed: R14.1, VD8.1 (K)
unnamed: R17.1, VD10.1 (K)
unnamed: R20.1, VD12.1 (K)
unnamed: R23.1, VD14.1 (K)
unnamed: R26.1, VD16.1 (K)
unnamed: R29.1, VD18.1 (K)
unnamed: R32.1, VD20.1 (K)
unnamed: R35.1, VD22.1 (K)
unnamed: R38.1, VD24.1 (K)
unnamed: R41.1, VD26.1 (K)
unnamed: R44.1, VD28.1 (K)
unnamed: R47.1, VD30.1 (K)
unnamed: R50.1, VD32.1 (K)
unnamed: R53.1, VD34.1 (K)
unnamed: R56.1, VD36.1 (K)
unnamed: R59.1, VD38.1 (K)
unnamed: R62.1, VD40.1 (K)
unnamed: R65.1, VD42.1 (K)
unnamed: R68.1, VD44.1 (K)
unnamed: R71.1, VD46.1 (K)
unnamed: R74.1, VD48.1 (K)
unnamed: R77.1, VD50.1 (K)
unnamed: R80.1, VD52.1 (K)
