antondrroid/V_meter_013/soft_MCU/multimeter/Soft/multi_013/main.h

/*
 * main.h
 *
 * Created: 2/19/2020 2:51:00 PM
 *  Author: john
 */ 
#ifndef MAIN_H_
#define MAIN_H_
//--------------------insert from main.h
//?????????
#define F_CPU 16000000L
#define DEBAG
//?????????
#include <avr/io.h>
#include <avr/interrupt.h>
#include <util/delay.h>
#include <stdio.h>
//#include <avr/pgmspace.h>
#include <stdlib.h>
#include <string.h>
#include <avr/wdt.h>
#include "adc.h"
//?????????  //this was russian comments
//#include "usart.h" //it's in usart.c
//?????????  //this was russian comments
#endif /* MAIN_H_ */
