antondrroid/V_meter_013/soft_MCU/multimeter/Soft/multi_000/~dc.h

/*
 * adc.h
 *
 * Created: 11/25/2020 10:55:05 AM
 *  Author: john
 */ 


#ifndef ADC_H_
#define ADC_H_
#include "main.h"
void ADC_Init(void);    //prototype
unsigned int ADC_convert (void);



#endif /* ADC_H_ */
