antondrroid/V_meter_013/soft_MCU/multimeter/Soft/multi_000/~dt.h

/*
 * adt.h
 *
 * Created: 12/2/2020 5:29:37 AM
 *  Author: anton
 */ 


#ifndef ADT_H_
#define ADT_H_
#include "main.h"
void ADT_Init(void);    //prototype
unsigned int ADT_convert (void);




#endif /* ADT_H_ */
